MakersAsylumIndia/Arcade/datasheets/How-It-Works-MAX7219-8x8-LED-Matrix-768x463.webp

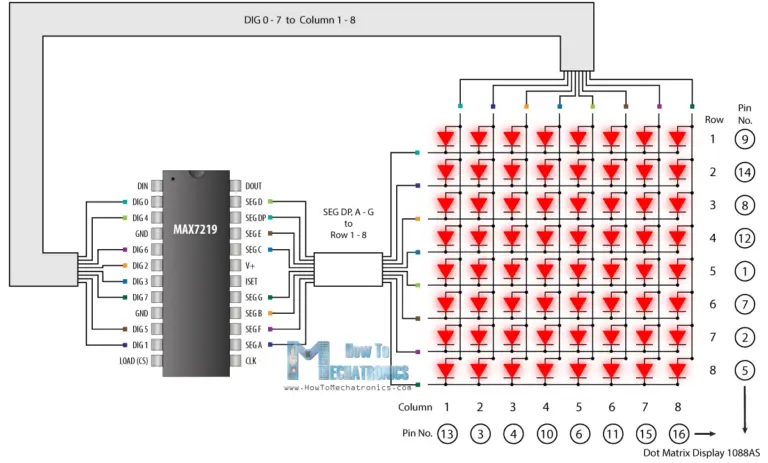
datasheets/How-It-Works-MAX7219-8x8-LED-Matrix-768x463.webp
