MakersAsylumIndia/Arcade/datasheets/led_matrix_fabprint.png

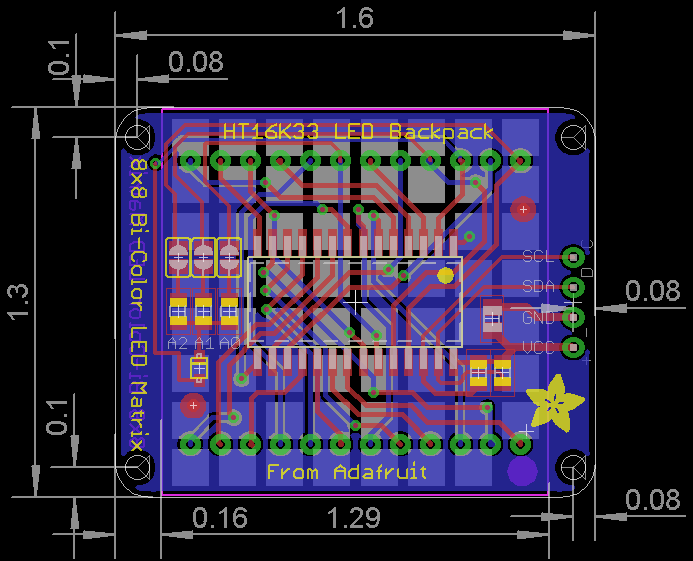
datasheets/led_matrix_fabprint.png
