MakersAsylumIndia/Arcade/datasheets/MAX7219-8-Digit-LED-Display-Driver.jpg

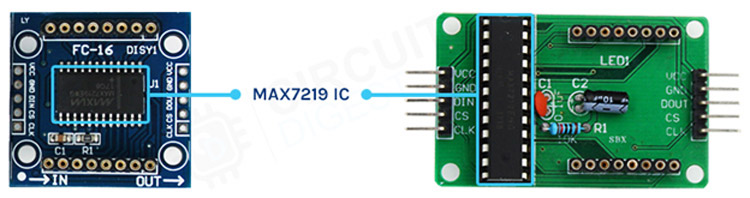
datasheets/MAX7219-8-Digit-LED-Display-Driver.jpg
