MakersAsylumIndia/Arcade/datasheets/max7219-8x8-dot-led-matrix-display-module3-1000x1000.png

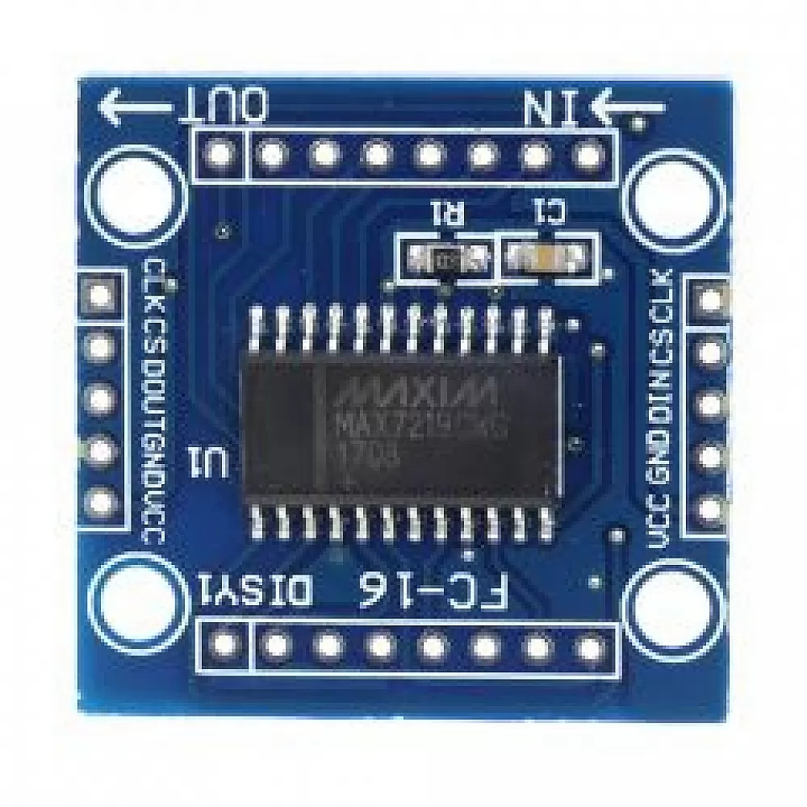
datasheets/max7219-8x8-dot-led-matrix-display-module3-1000x1000.png
