MakersAsylumIndia/Arcade/datasheets/MAX7219-LED-Dot-Matrix-Display-Module-Circuit-Diagram.png

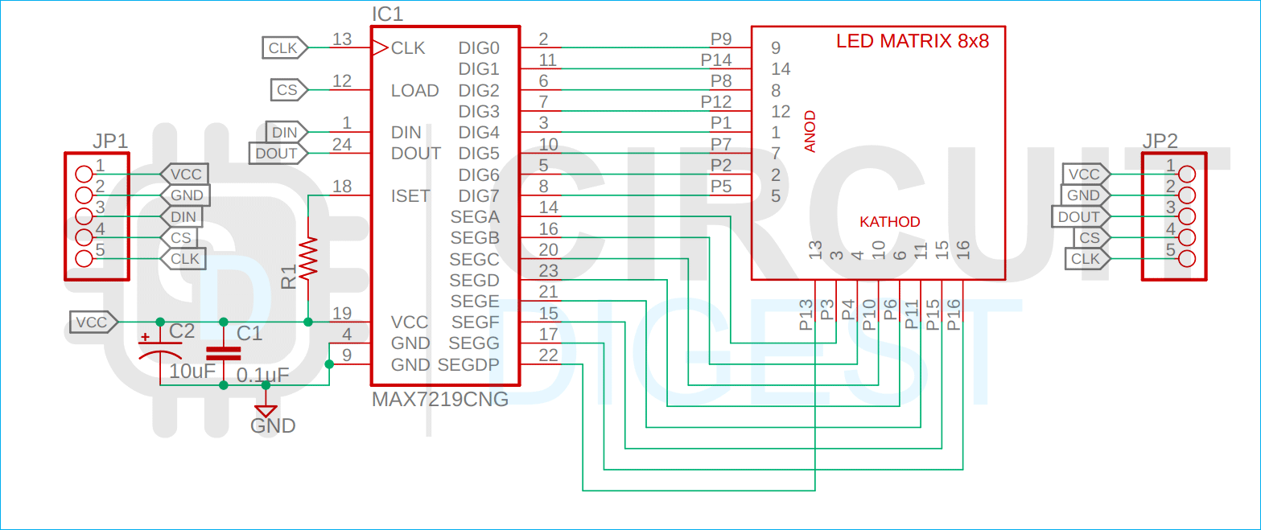
datasheets/MAX7219-LED-Dot-Matrix-Display-Module-Circuit-Diagram.png
