MakersAsylumIndia/Arcade/datasheets/original.jpg

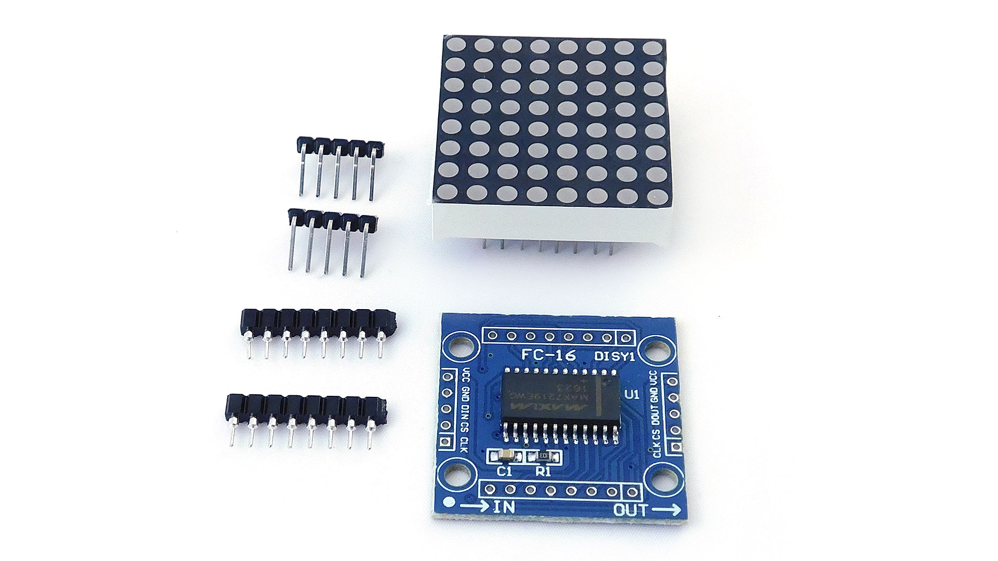
datasheets/original.jpg
