MakersAsylumIndia/Arcade/enclosure/images_prototype/proto_01.jpeg

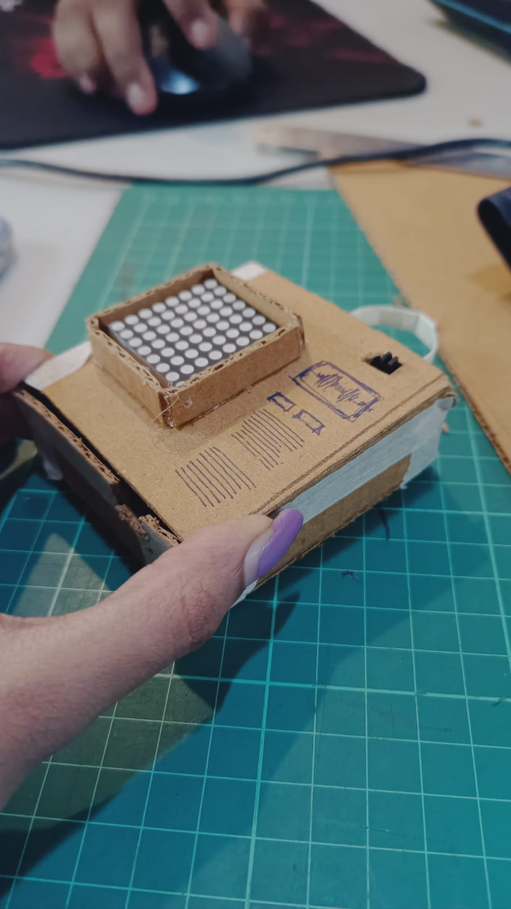
enclosure/images_prototype/proto_01.jpeg
