MakersAsylumIndia/Arcade/enclosure/images_prototype/proto_02.jpeg

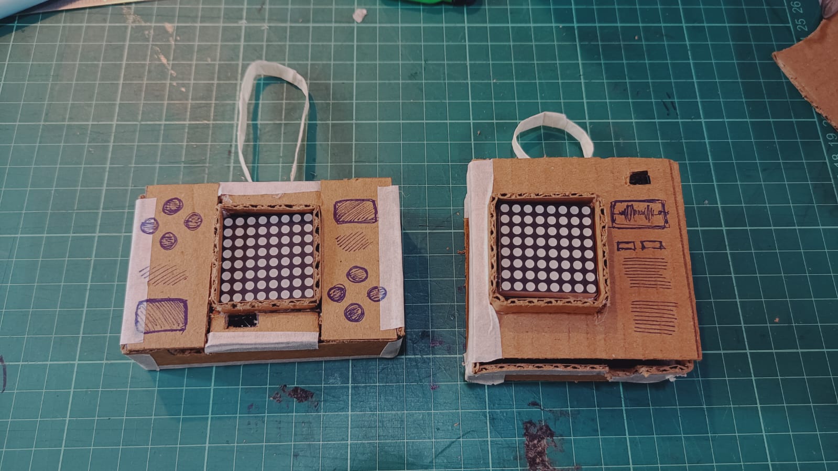
enclosure/images_prototype/proto_02.jpeg
