MakersAsylumIndia/Arcade/enclosure/images_prototype/proto_03.jpeg

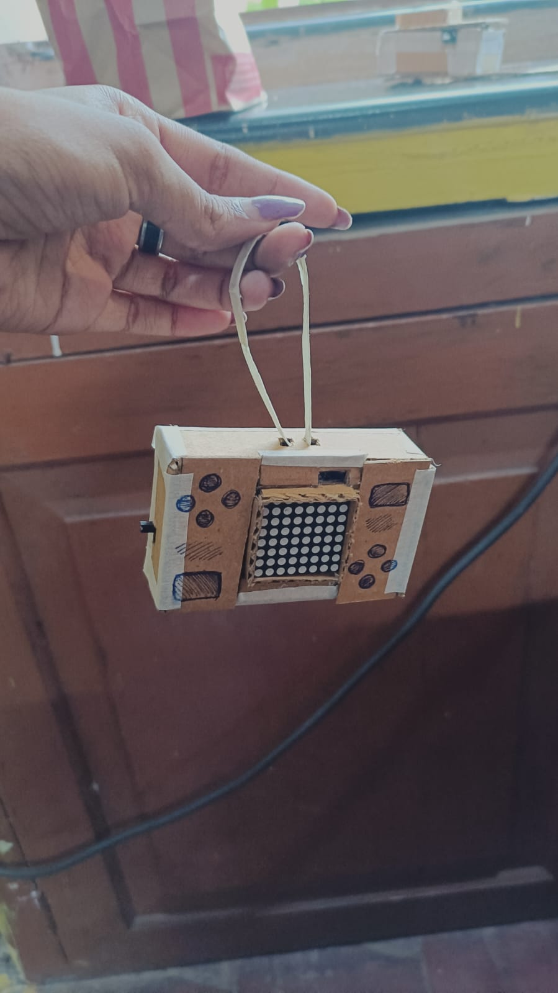
enclosure/images_prototype/proto_03.jpeg
