MakersAsylumIndia/Arcade/enclosure/images_prototype/proto_04.jpeg

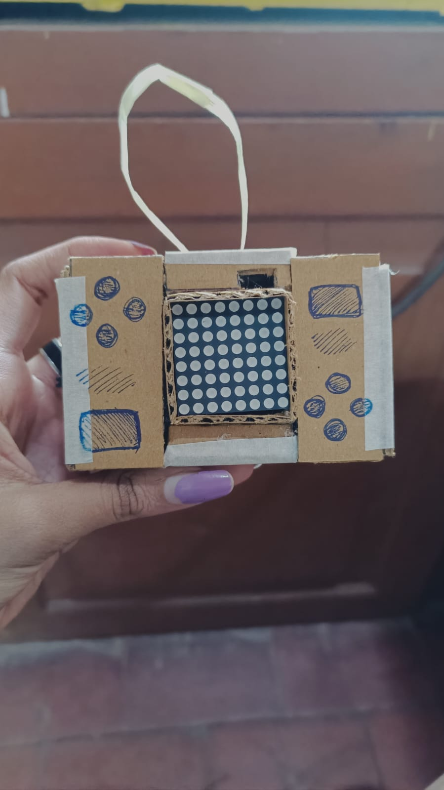
enclosure/images_prototype/proto_04.jpeg
