MakersAsylumIndia/Arcade/enclosure/images_prototype/proto_05.jpeg

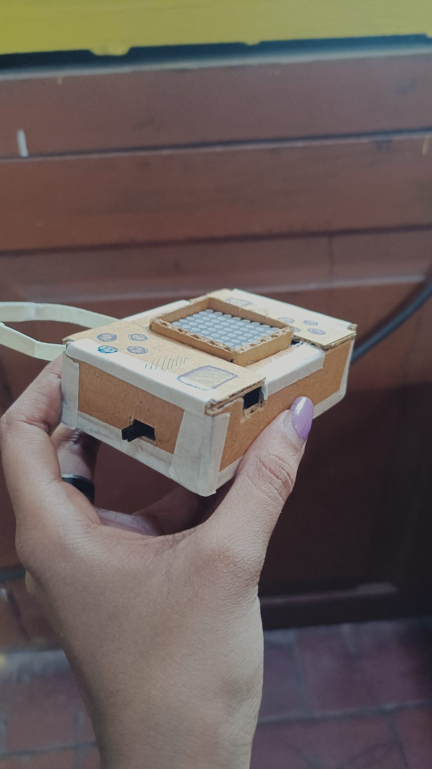
enclosure/images_prototype/proto_05.jpeg
