MakersAsylumIndia/Arcade/enclosure/images_prototype/proto_06.jpeg

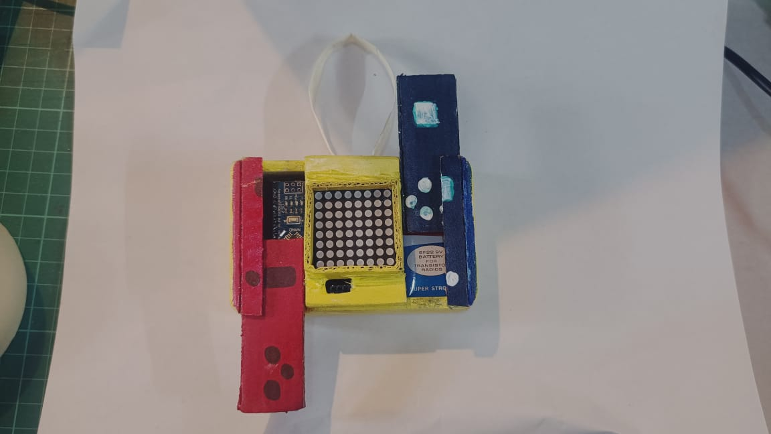
enclosure/images_prototype/proto_06.jpeg
