MakersAsylumIndia/Arcade/enclosure/images_prototype/proto_07.jpeg

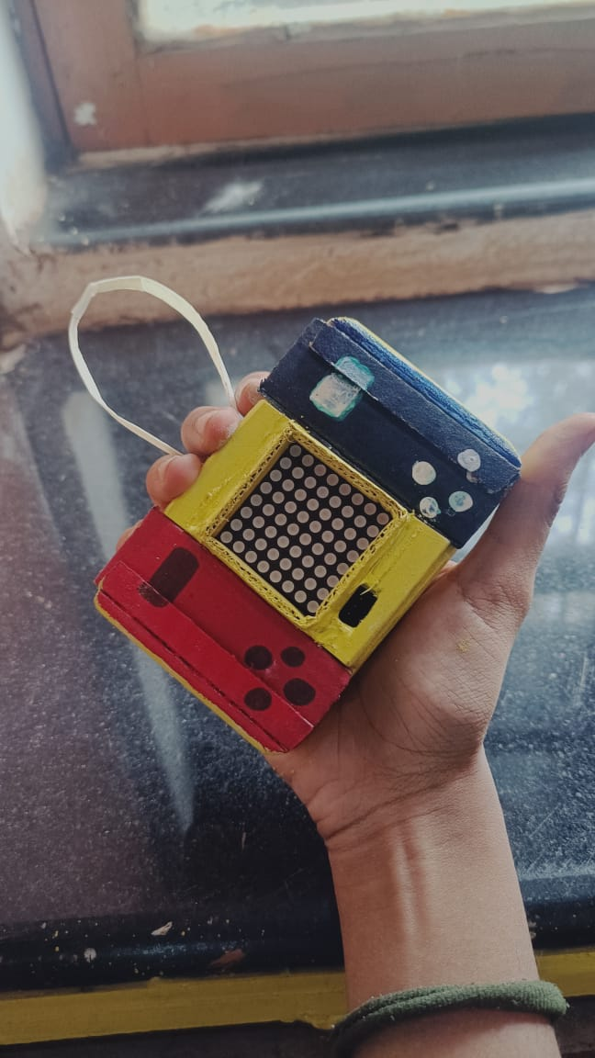
enclosure/images_prototype/proto_07.jpeg
