MakersAsylumIndia/Arcade/enclosure/images_prototype/proto_08.jpeg

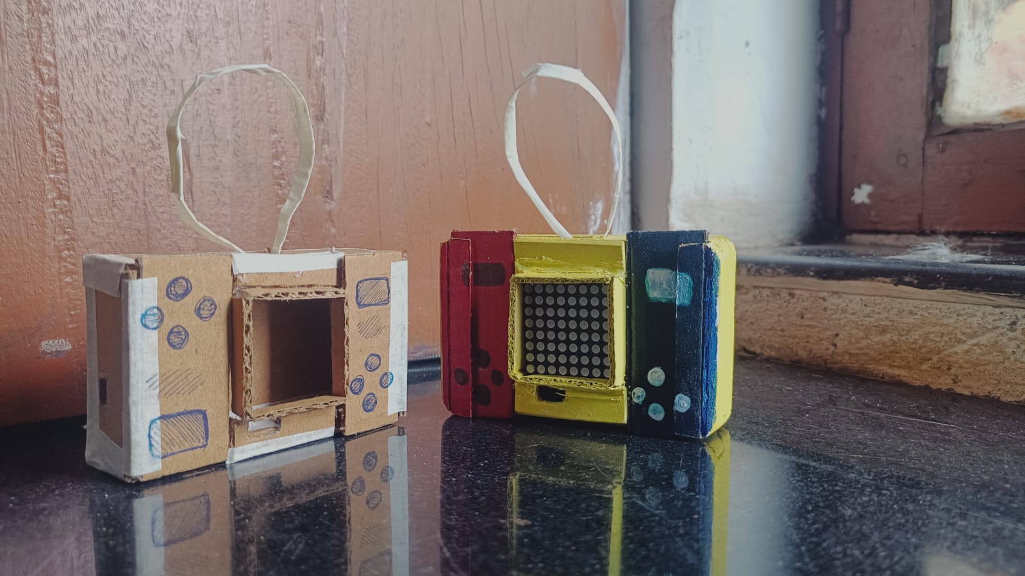
enclosure/images_prototype/proto_08.jpeg
