MakersAsylumIndia/Arcade/enclosure/images_prototype/proto_09.jpeg

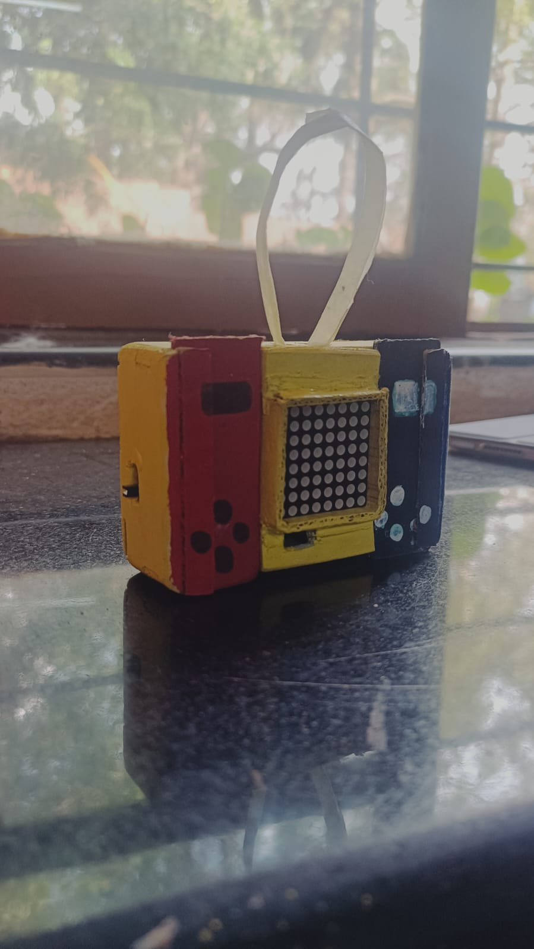
enclosure/images_prototype/proto_09.jpeg
