MakersAsylumIndia/Arcade/enclosure/images_prototype/TheThing_Arcade_v1_01.png

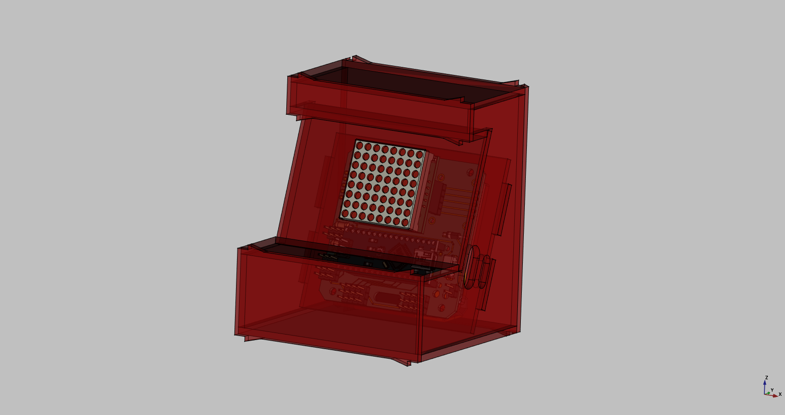
enclosure/images_prototype/TheThing_Arcade_v1_01.png
