MakersAsylumIndia/Arcade/enclosure/renders/Arcade_v7_01.png

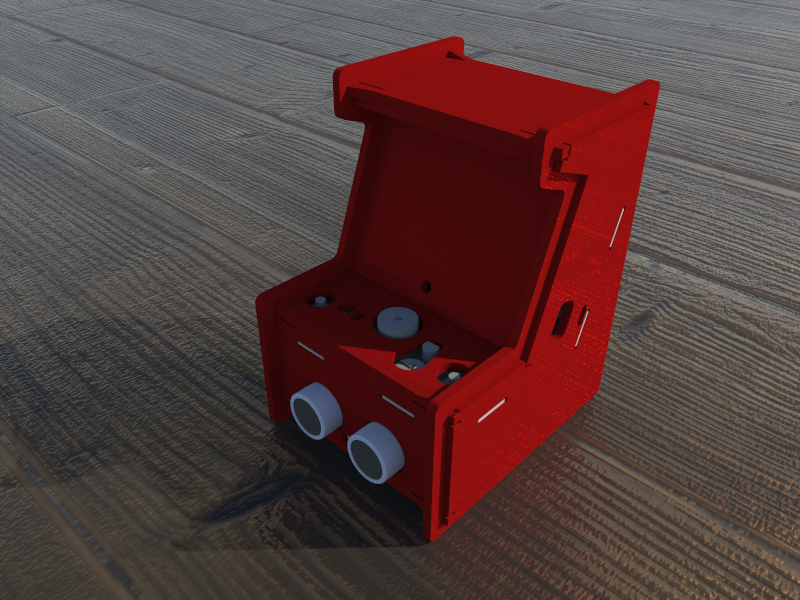
enclosure/renders/Arcade_v7_01.png
