MakersAsylumIndia/Arcade/enclosure/renders/Arcade_v7_02.png

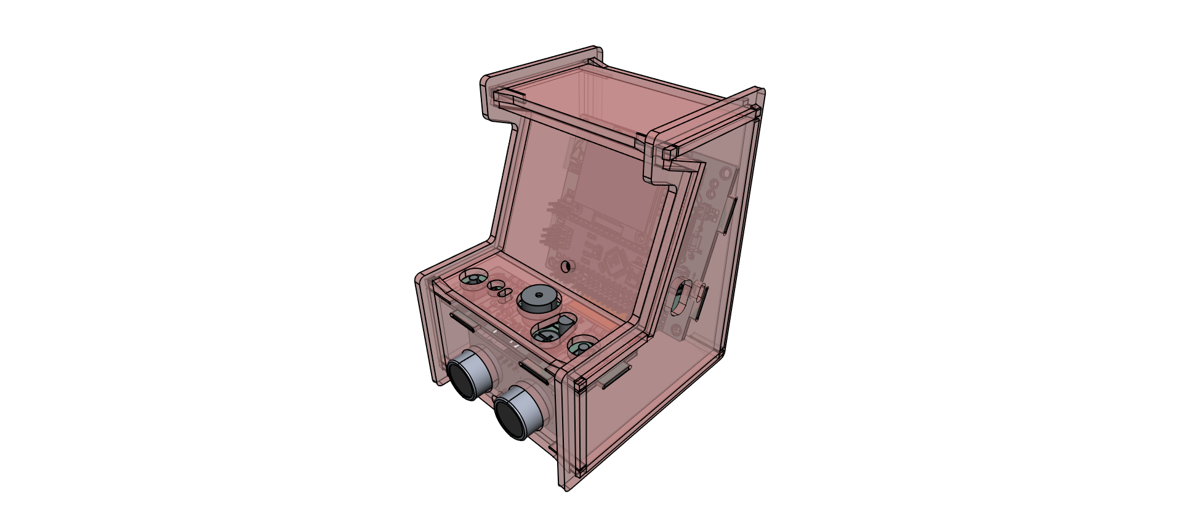
enclosure/renders/Arcade_v7_02.png
