MakersAsylumIndia/Arcade/enclosure/renders/Arcade_v7_04.png

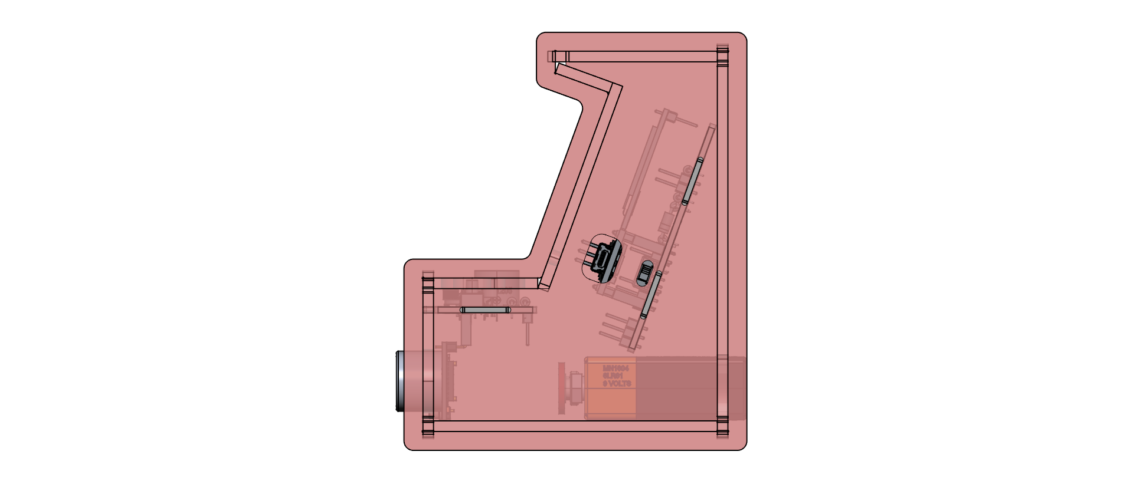
enclosure/renders/Arcade_v7_04.png
