MakersAsylumIndia/Arcade/enclosure/renders/Arcade_v7_09.png

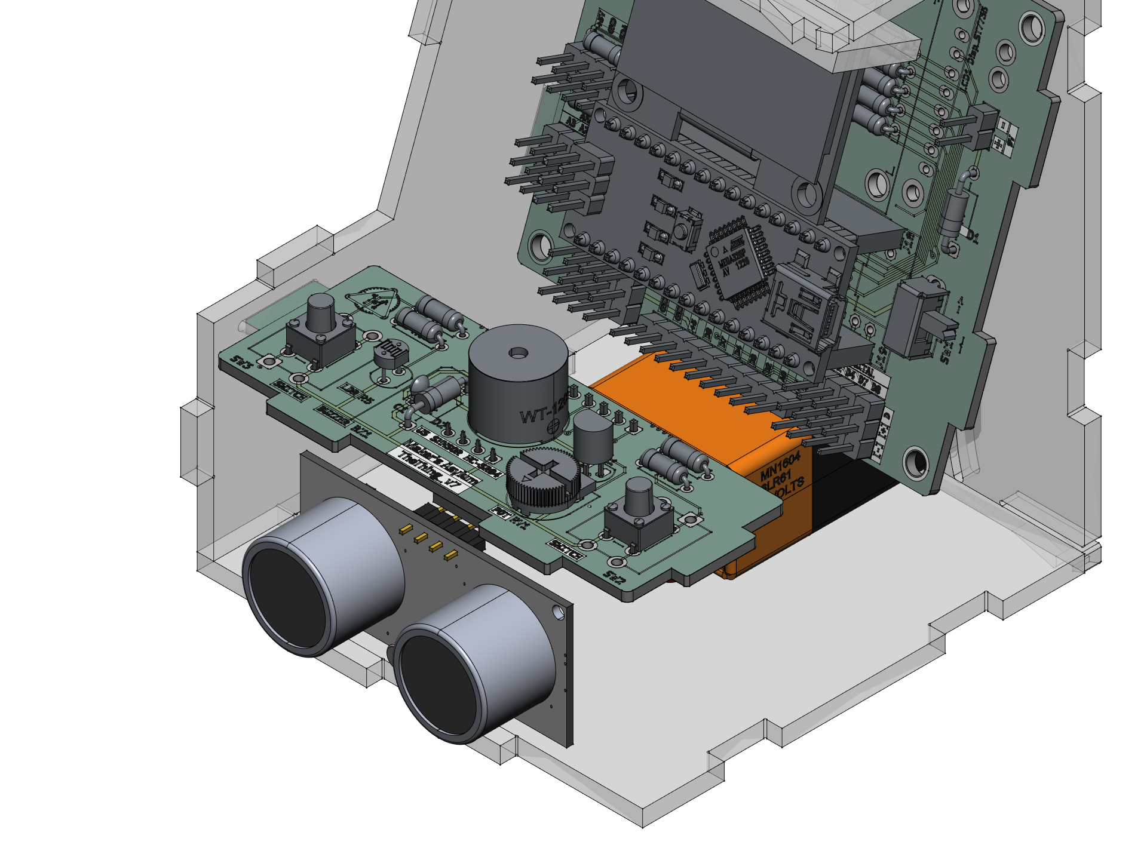
enclosure/renders/Arcade_v7_09.png
