MakersAsylumIndia/Arcade/enclosure/renders/Arcade_v7_10.png

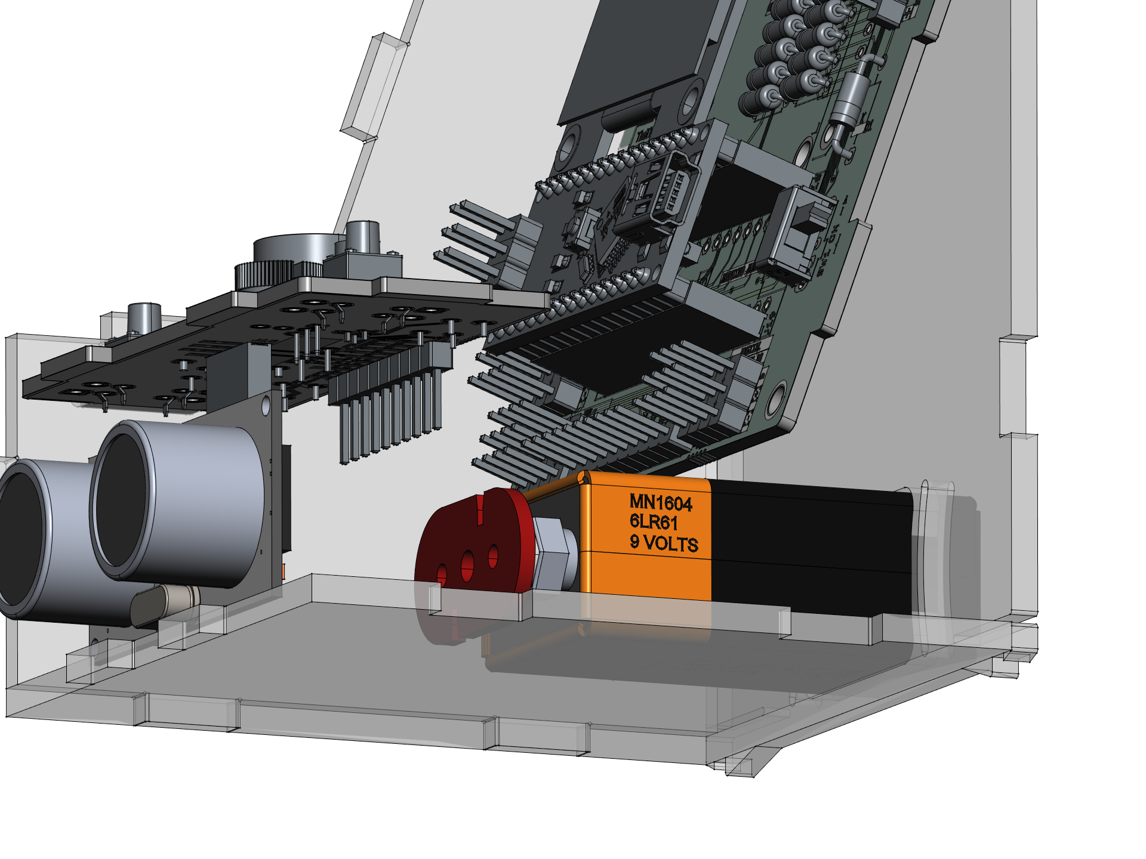
enclosure/renders/Arcade_v7_10.png
