MakersAsylumIndia/Arcade/enclosure/renders/Arcade_v7_11.png

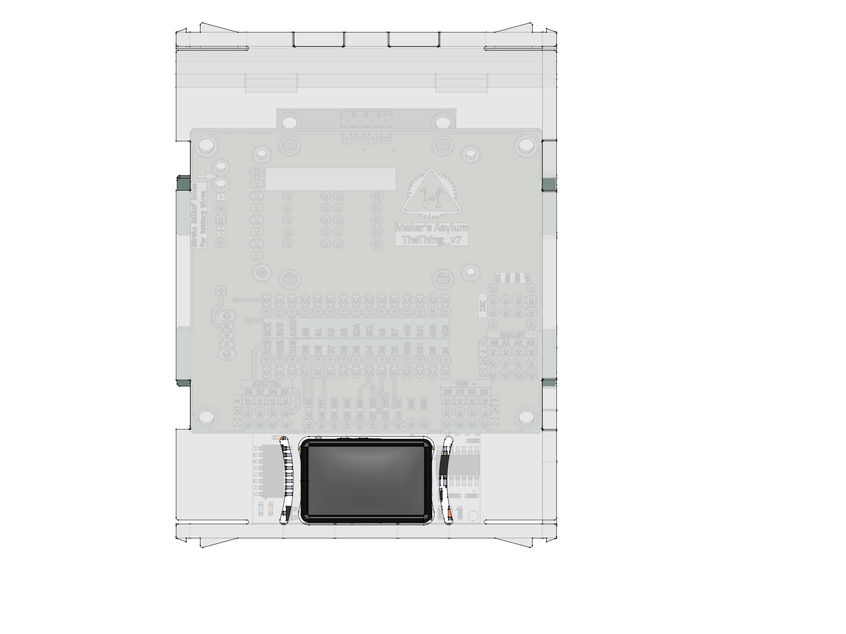
enclosure/renders/Arcade_v7_11.png
