MakersAsylumIndia/Arcade/enclosure/renders/Arcade_v7_12.png

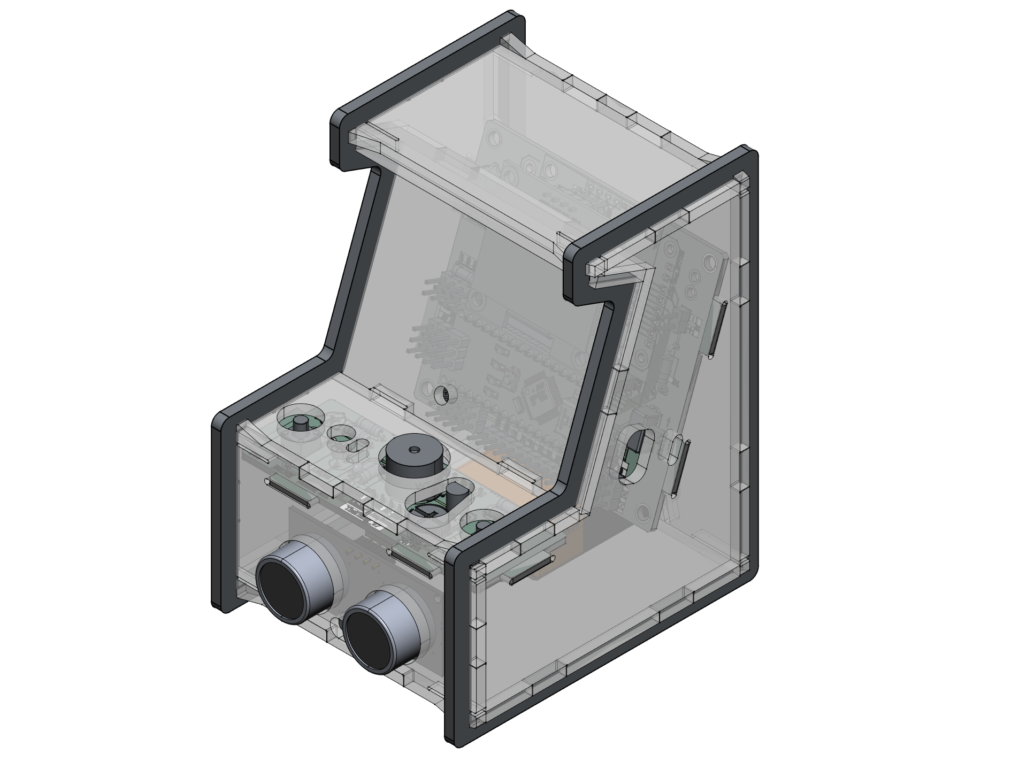
enclosure/renders/Arcade_v7_12.png
