MakersAsylumIndia/Arcade/enclosure/renders/Arcade_v7_13.png

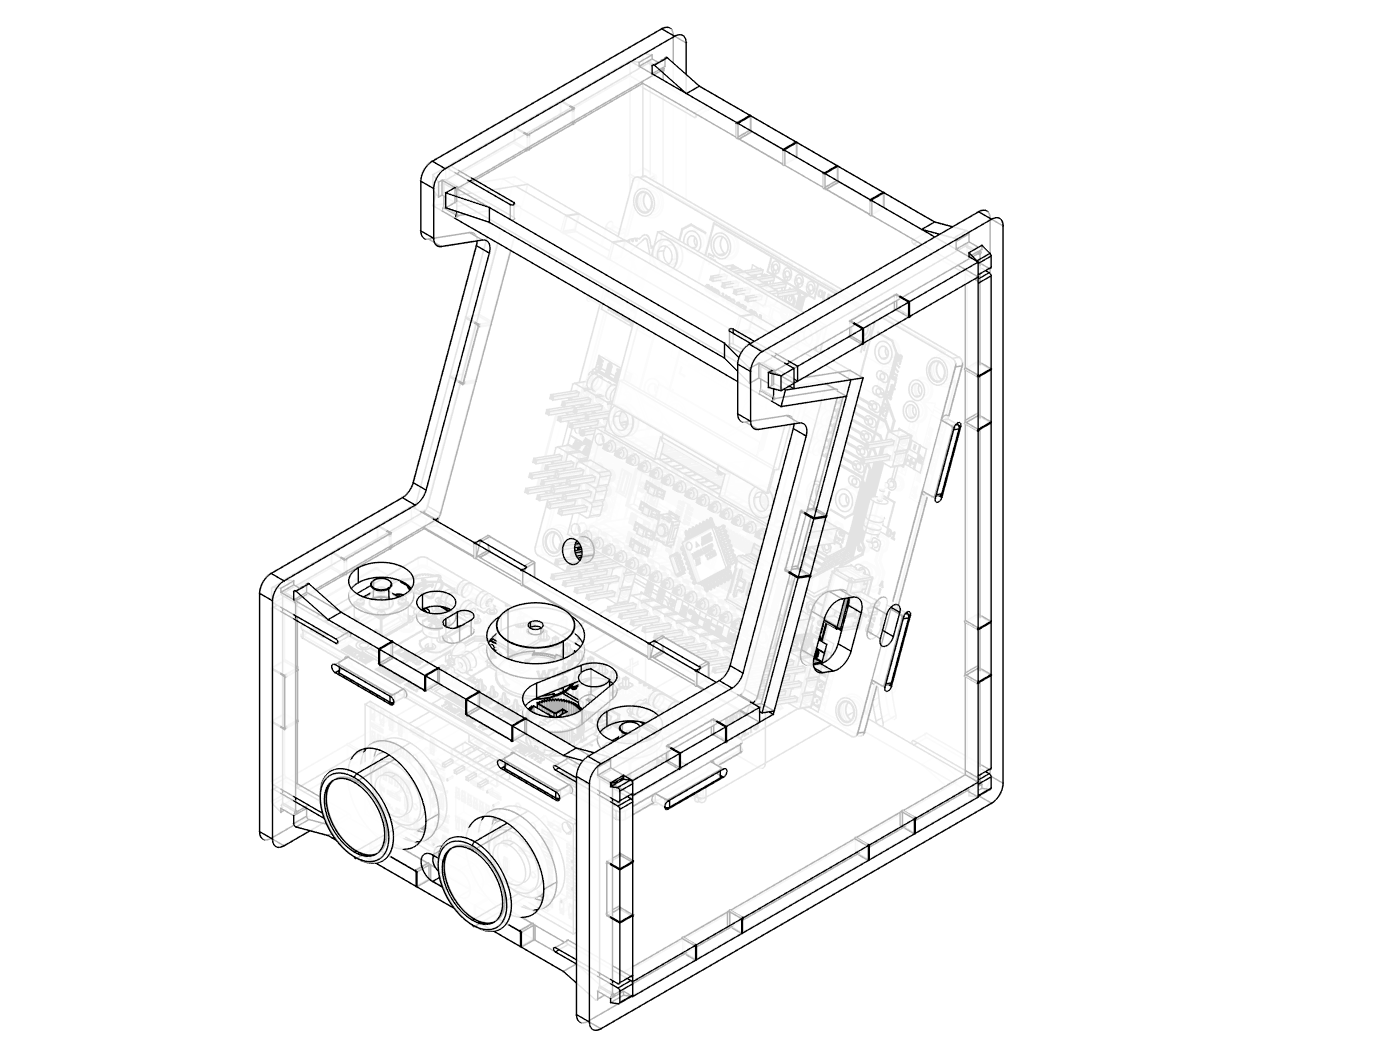
enclosure/renders/Arcade_v7_13.png
