MakersAsylumIndia/Arcade/enclosure/renders/TheThing_v5_TD01_pg2.png

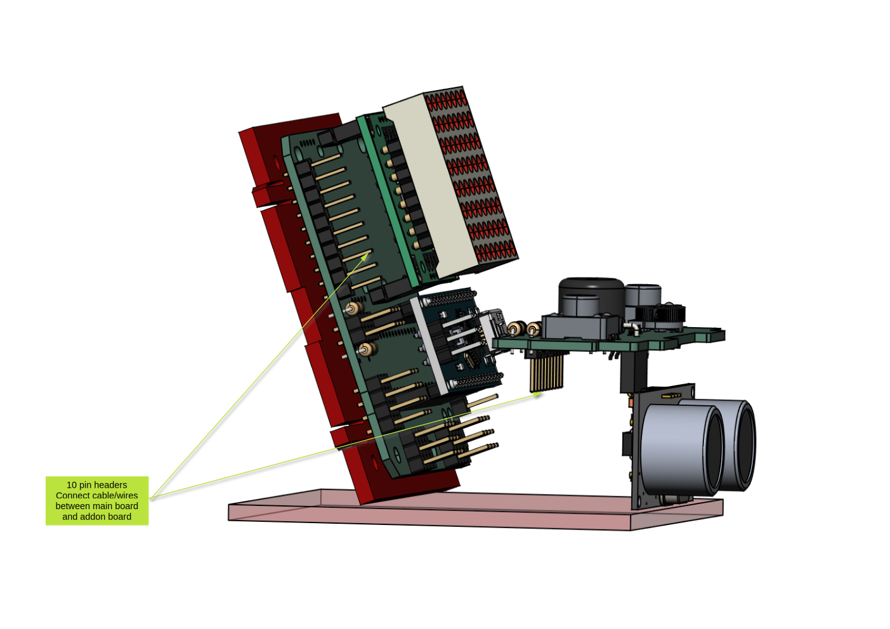
enclosure/renders/TheThing_v5_TD01_pg2.png
