MakersAsylumIndia/Arcade/hardware_PCB/TheThing_v8/images/TheThing_pcb_02.png

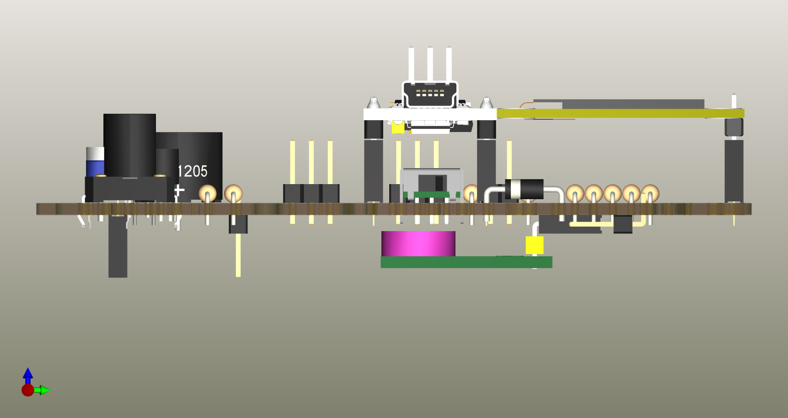
hardware_PCB/TheThing_v8/images/TheThing_pcb_02.png
