MakersAsylumIndia/Arcade/hardware_PCB/TheThing_v8/images/TheThing_pcb_03.png

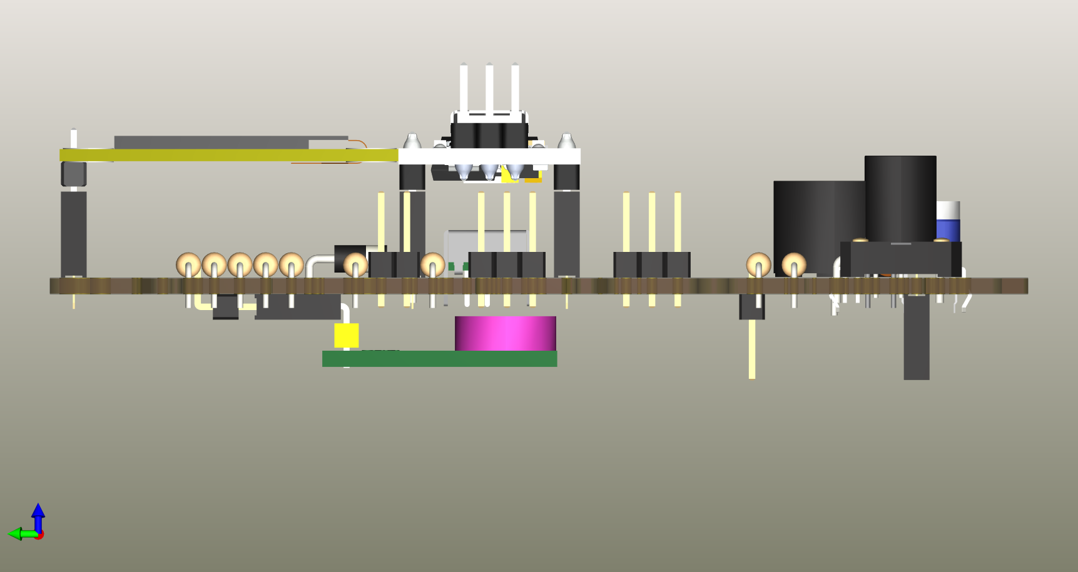
hardware_PCB/TheThing_v8/images/TheThing_pcb_03.png
