MakersAsylumIndia/Arcade/hardware_PCB/TheThing_v8/images/TheThing_pcb_07.png

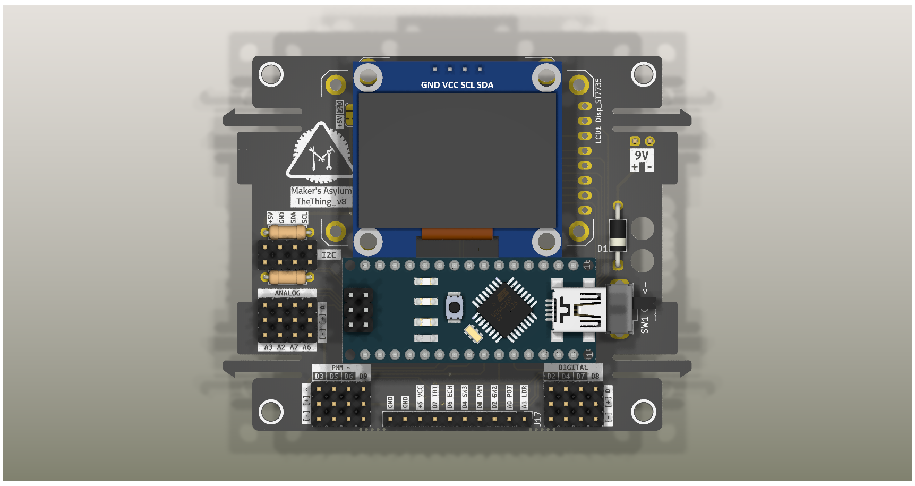
hardware_PCB/TheThing_v8/images/TheThing_pcb_07.png
