MakersAsylumIndia/Arcade/hardware_PCB/TheThing_v8/images/TheThing_pcb_10.png

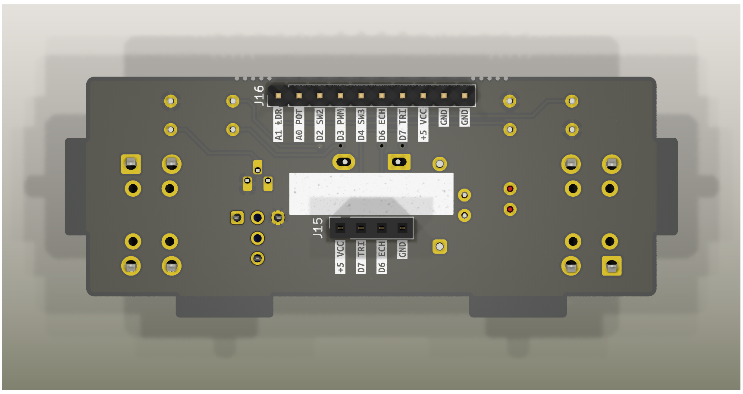
hardware_PCB/TheThing_v8/images/TheThing_pcb_10.png
