MakersAsylumIndia/Arcade/hardware_PCB/TheThing_v8/images/TheThing_pcb_12.png

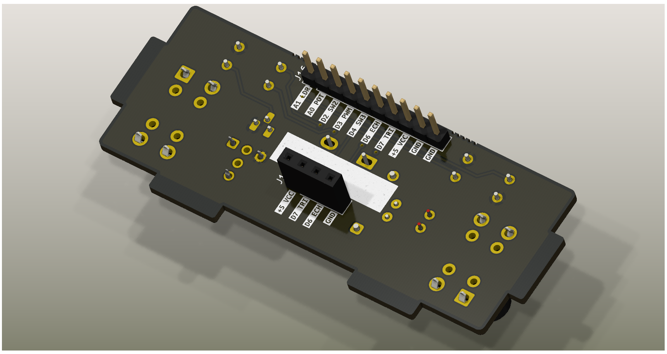
hardware_PCB/TheThing_v8/images/TheThing_pcb_12.png
