MakersAsylumIndia/Arcade/hardware_PCB/TheThing_v8/images/TheThing_PCB_B.png

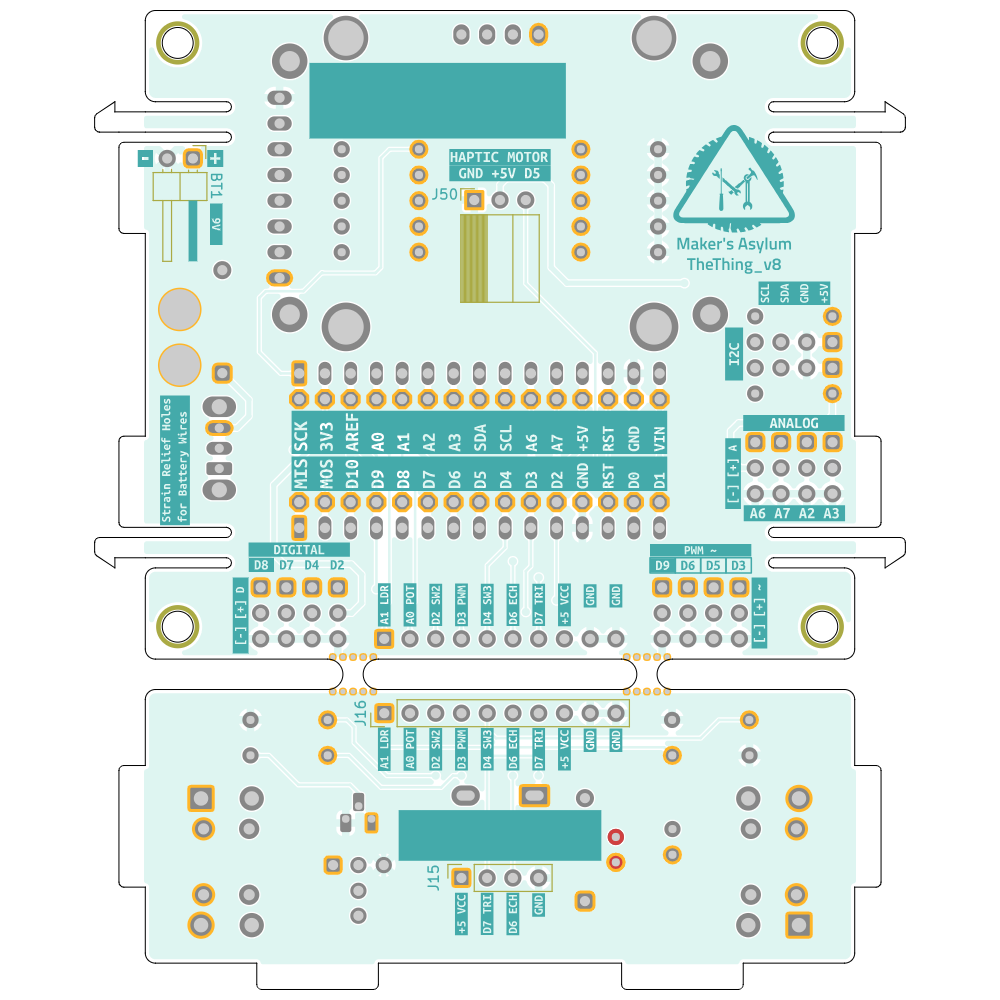
hardware_PCB/TheThing_v8/images/TheThing_PCB_B.png
