MakersAsylumIndia/Arcade/hardware_PCB/TheThing_v8/images/TheThing_PCB_F.png

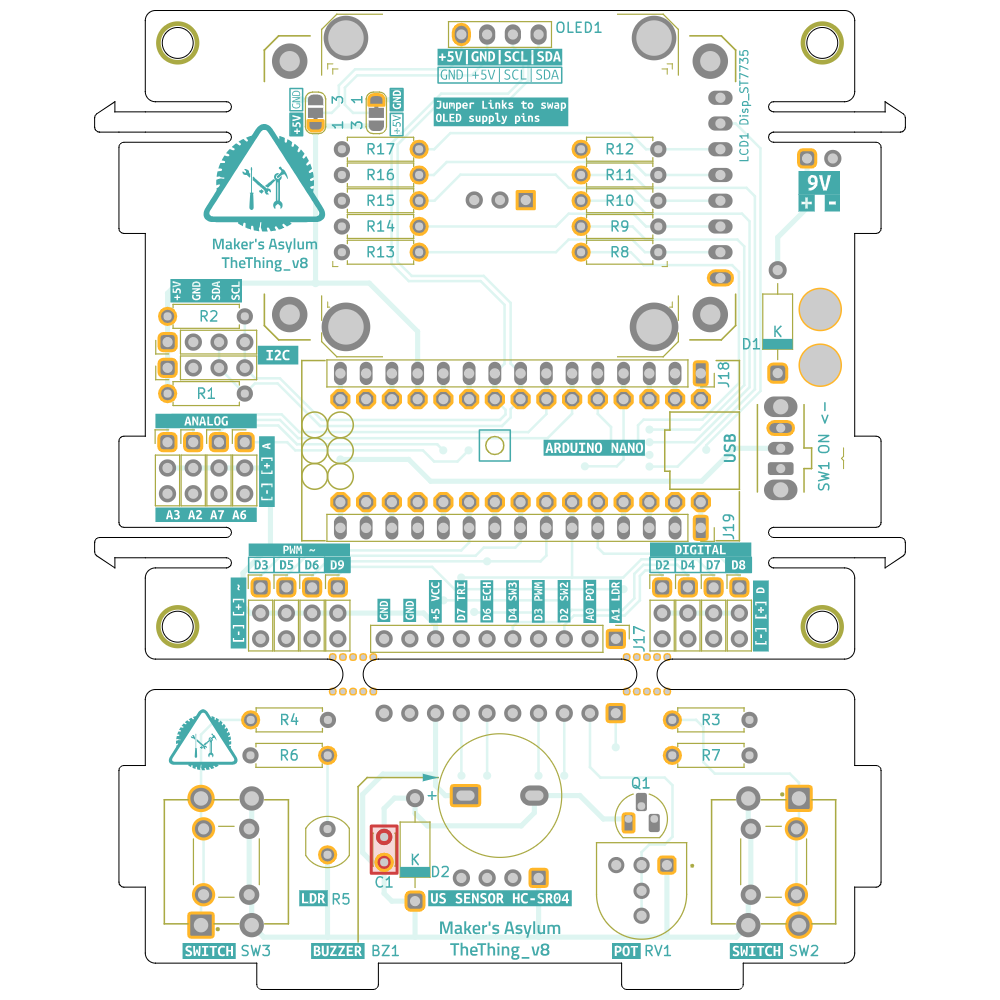
hardware_PCB/TheThing_v8/images/TheThing_PCB_F.png
