MakersAsylumIndia/Arcade/hardware_PCB/TheThing_v8/vegg_production/MA_TheThing_v8_vegg/TheThing_pcb_06.png

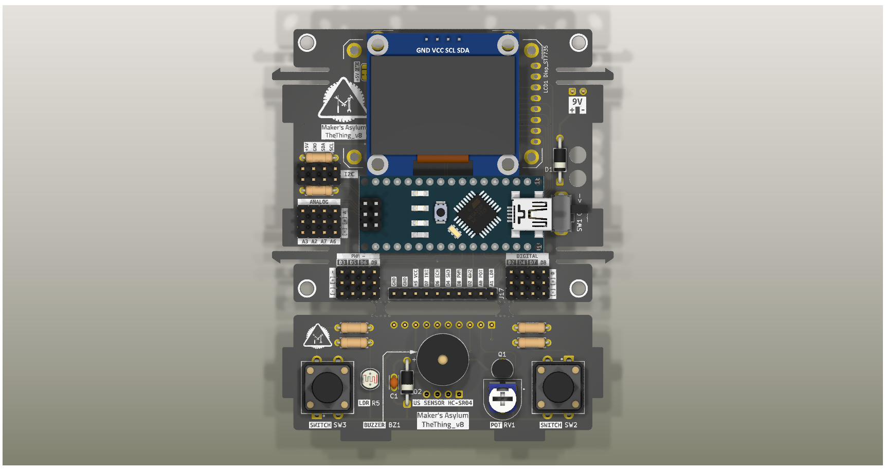
hardware_PCB/TheThing_v8/vegg_production/MA_TheThing_v8_vegg/TheThing_pcb_06.png
