MakersAsylumIndia/Arcade/kicad_v5/TheThing/images/TheThing_pcb_07.png

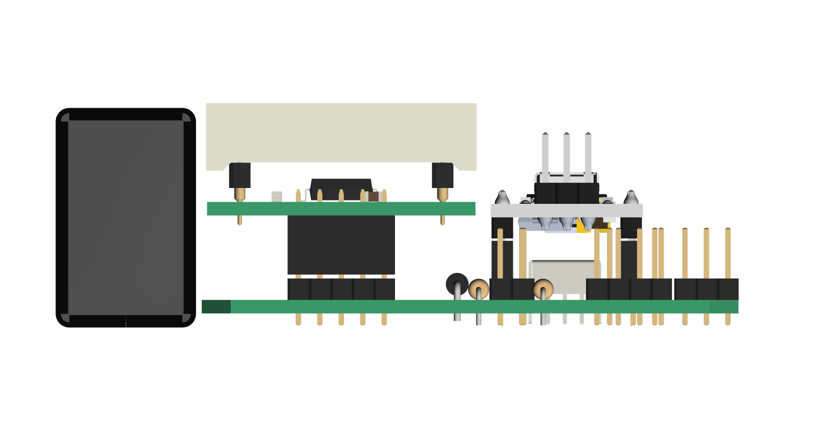
kicad_v5/TheThing/images/TheThing_pcb_07.png
