MakersAsylumIndia/Arcade/enclosure/DXF/TheThing_v8B_tabs_export_fix1-Sketch.dxf

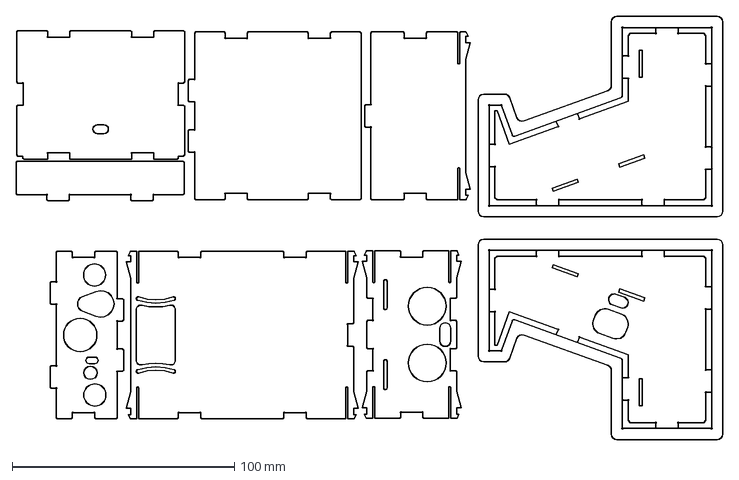
[picture p103: CAD file, 2025-10-11]
enclosure/DXF/TheThing_v8B_tabs_export_fix1-Sketch.dxf
318.2 x 190.6 mm
