MakersAsylumIndia/Arcade/enclosure/footprints_for_kicad/HC_SR04.FCStd

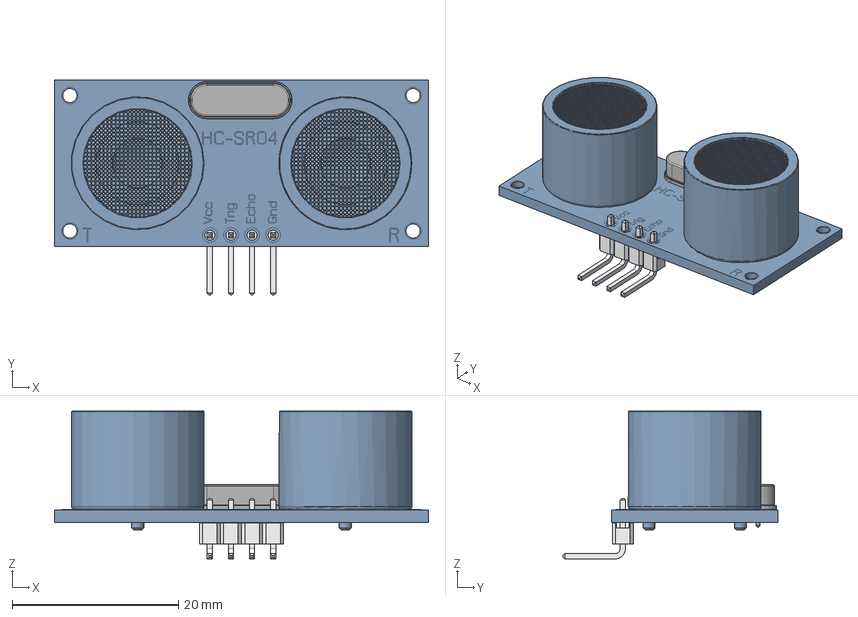
[picture p104: CAD file, 2025-11-04]
enclosure/footprints_for_kicad/HC_SR04.FCStd
45.0 x 25.8 x 17.8 mm
Quarz
Platine
Pins_4fach_90Grad_001
HC_SR04_gitter_001
HC_SR04_gitter_002
