MakersAsylumIndia/Arcade/enclosure/footprints_for_kicad/Tactile_Switch/TL1105BF160Q.step

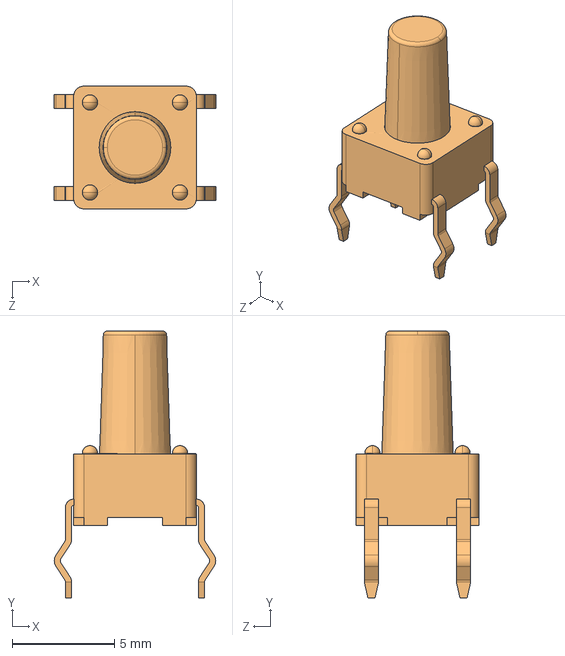
[picture p105: CAD file, 2024-11-12]
enclosure/footprints_for_kicad/Tactile_Switch/TL1105BF160Q.step
7.89 x 13.0 x 6.00 mm
Body1.STEP
Body2.STEP
