MakersAsylumIndia/Arcade/enclosure/TheThing_v8.FCStd

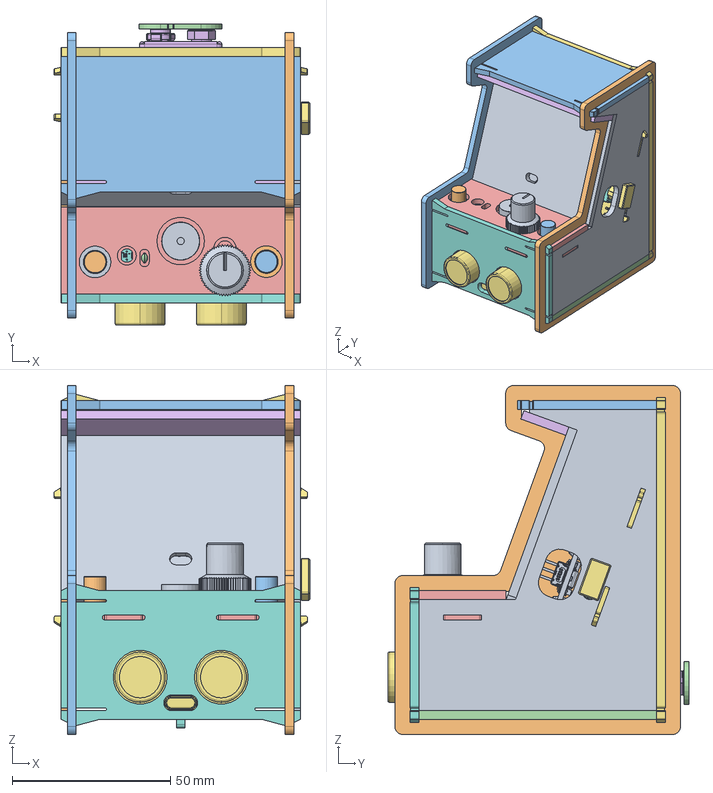
[picture p106: CAD file, 2026-05-04]
enclosure/TheThing_v8.FCStd
80.8 x 95.1 x 110.2 mm
Body_right
Body_left
Body_top
Body_bottom
Body_keys
Body_under
Body_back
Body_front
Body_face
Body_right_clip
Body_left_clip
_68005_cp005_cp
_68005_cp005_cp003
_68005_cp005_cp004
hc-sr04
SW_CuK_OS102011MA1QN1_SPDT_Angled001
PinHeader_1x04_P2.54mm_Vertical007
R_Axial_DIN0207_L6.3mm_D2.5mm_P7.62mm_Horizontal035
D_DO-41_SOD81_P10.16mm_Horizontal008
PinHeader_1x10_P2.54mm_Vertical004
PinHeader_1x03_P2.54mm_Vertical047
R_Axial_DIN0207_L6.3mm_D2.5mm_P7.62mm_Horizontal036
R_Axial_DIN0207_L6.3mm_D2.5mm_P7.62mm_Horizontal037
PinSocket_1x15_P2.54mm_Vertical
arduino_nano
arduino_nano006
R_Axial_DIN0207_L6.3mm_D2.5mm_P7.62mm_Horizontal038
PinHeader_1x03_P2.54mm_Vertical048
PinHeader_1x03_P2.54mm_Vertical049
PinHeader_1x03_P2.54mm_Vertical050
PinHeader_1x03_P2.54mm_Vertical051
Display_OLED-1_3-128X64
Display_OLED-1_3-128X072
Display_OLED-1_3-128X073
PinSocket_1x04_P2.54mm_Vertical001
PinSocket_1x15_P2.54mm_Vertical004
R_Axial_DIN0207_L6.3mm_D2.5mm_P7.62mm_Horizontal039
R_Axial_DIN0207_L6.3mm_D2.5mm_P7.62mm_Horizontal040
PinHeader_1x03_P2.54mm_Vertical052
R_Axial_DIN0207_L6.3mm_D2.5mm_P7.62mm_Horizontal041
PinHeader_1x03_P2.54mm_Vertical053
R_Axial_DIN0207_L6.3mm_D2.5mm_P7.62mm_Horizontal042
R_Axial_DIN0207_L6.3mm_D2.5mm_P7.62mm_Horizontal043
R_Axial_DIN0207_L6.3mm_D2.5mm_P7.62mm_Horizontal044
PinHeader_1x03_P2.54mm_Vertical054
R_Axial_DIN0207_L6.3mm_D2.5mm_P7.62mm_Horizontal045
PinHeader_1x03_P2.54mm_Vertical055
R_Axial_DIN0207_L6.3mm_D2.5mm_P7.62mm_Horizontal046
PinHeader_1x03_P2.54mm_Vertical056
PinHeader_1x03_P2.54mm_Vertical057
PinHeader_1x04_P2.54mm_Vertical008
PinHeader_1x03_P2.54mm_Vertical058
PinSocket_1x03_P2.54mm_Horizontal_haptic
PinSocket_1x03_P2.54mm_Horizontal_haptic001
PinSocket_1x03_P2.54mm_Horizontal_haptic002
PinSocket_1x03_P2.54mm_Horizontal_haptic003
PinSocket_1x03_P2.54mm_Horizontal_haptic004
PinSocket_1x03_P2.54mm_Horizontal_haptic005
PinSocket_1x03_P2.54mm_Horizontal_haptic006
PinSocket_1x03_P2.54mm_Horizontal_haptic007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
