MakersAsylumIndia/Arcade/fabricate/DXF/#TheThing_v3_tabs.dxf

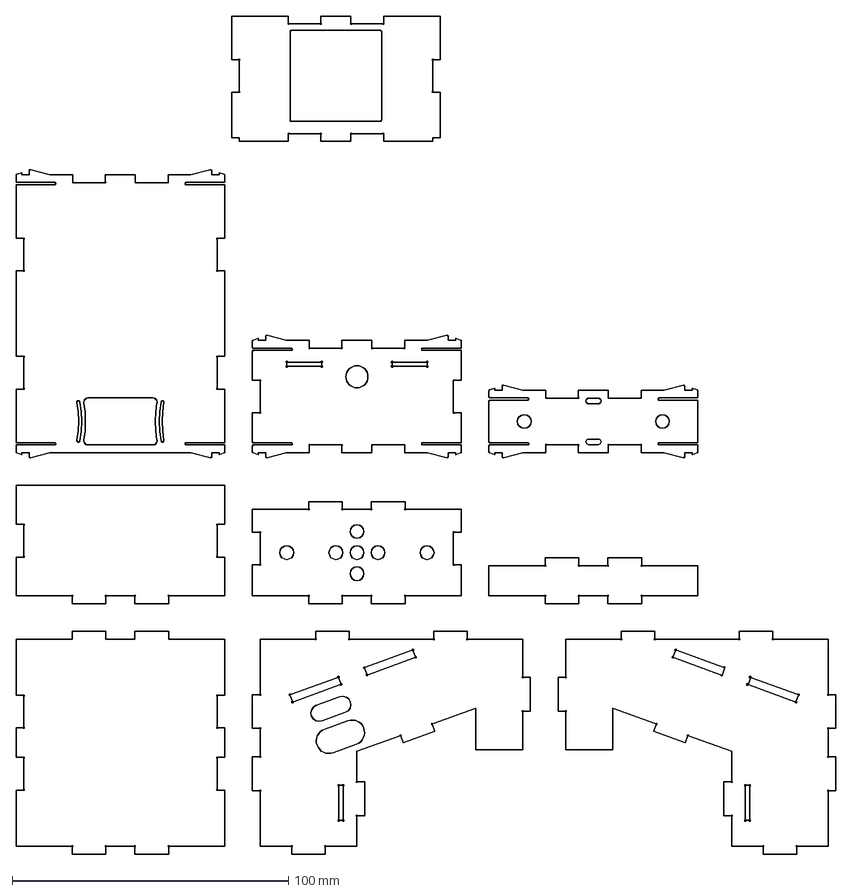
[picture p107: CAD file, 2025-02-07]
fabricate/DXF/#TheThing_v3_tabs.dxf
296.8 x 303.3 mm
