MakersAsylumIndia/Arcade/fabricate/TheThing_v3_multijoin.FCStd

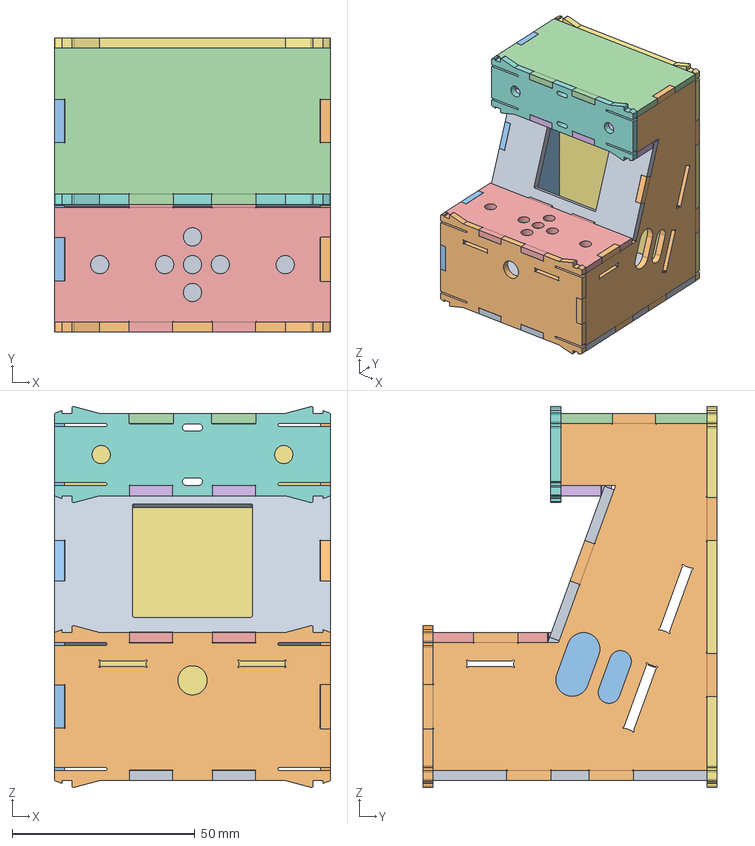
[picture p108: CAD file, 2024-12-13]
fabricate/TheThing_v3_multijoin.FCStd
75.6 x 80.6 x 104.4 mm
Pad014_tab
Pocket011_tab
Pocket013_tab
Pad013_tab
Pad015_tab
Pad016_tab
Pocket007_tab
Pocket_tab
