MakersAsylumIndia/Arcade/hardware_PCB/TheThing_v8/3D_models/PinSocket_1x03_P2.54mm_Horizontal_haptic.step

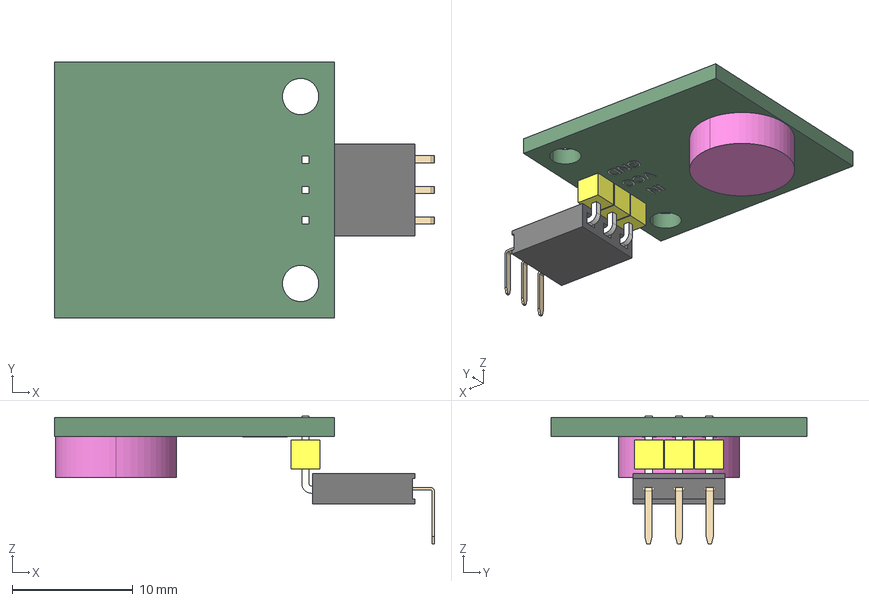
[picture p109: CAD file, 2025-08-25]
hardware_PCB/TheThing_v8/3D_models/PinSocket_1x03_P2.54mm_Horizontal_haptic.step
31.5 x 21.2 x 10.6 mm
