MakersAsylumIndia/Arcade/enclosure/3D_print/TheThing_v8-trimpot_knob_v4.step

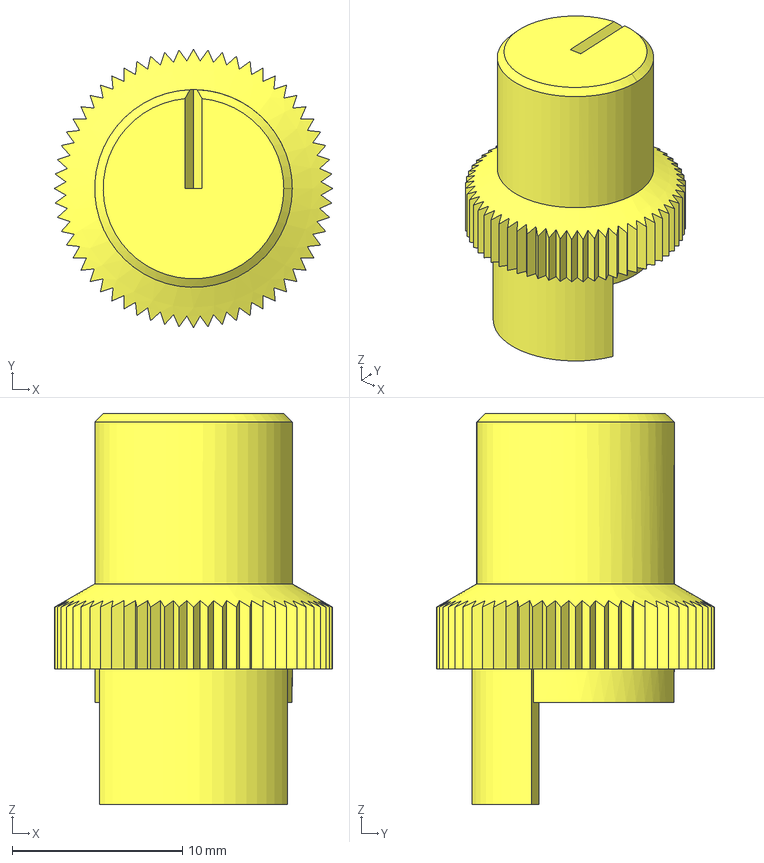
[picture p110: CAD file, 2026-05-04]
enclosure/3D_print/TheThing_v8-trimpot_knob_v4.step
16.3 x 16.3 x 22.9 mm
