MakersAsylumIndia/Arcade/enclosure/footprints_for_kicad/pot_knob-BodyChamfer.step

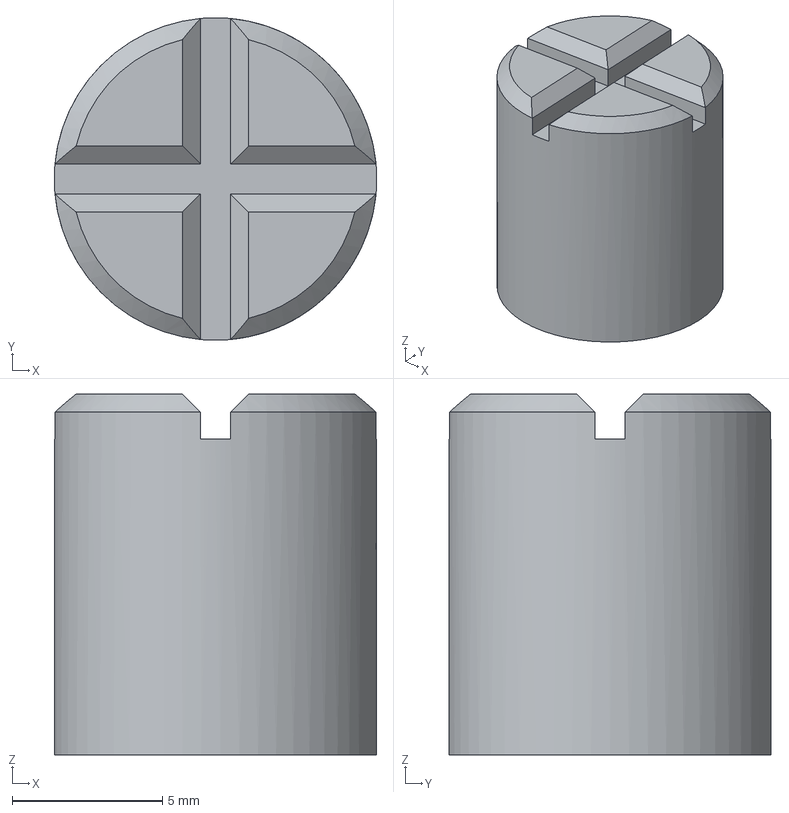
[picture p111: CAD file, 2025-07-18]
enclosure/footprints_for_kicad/pot_knob-BodyChamfer.step
10.7 x 10.7 x 12.0 mm
