MakersAsylumIndia/Arcade/enclosure/3D_print/TheThing_v8-trimpot_knob_v3.3mf

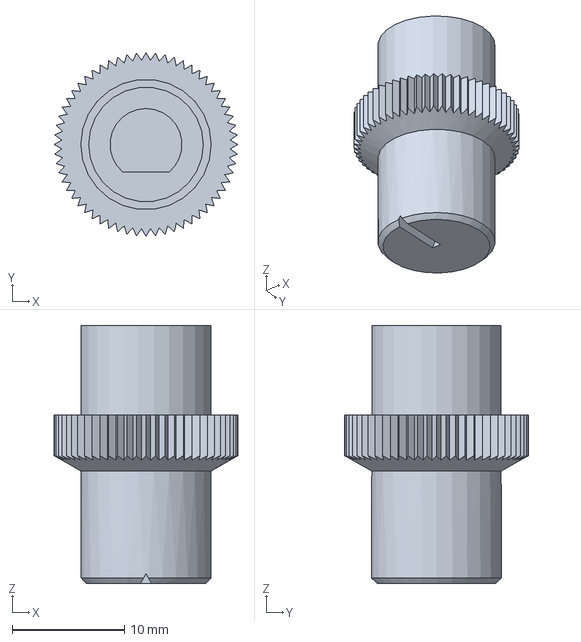
[picture p113: CAD file, 2025-11-04]
enclosure/3D_print/TheThing_v8-trimpot_knob_v3.3mf
16.3 x 16.3 x 22.9 mm
