MakersAsylumIndia/Arcade/enclosure/footprints_for_kicad/pot_knob.FCStd

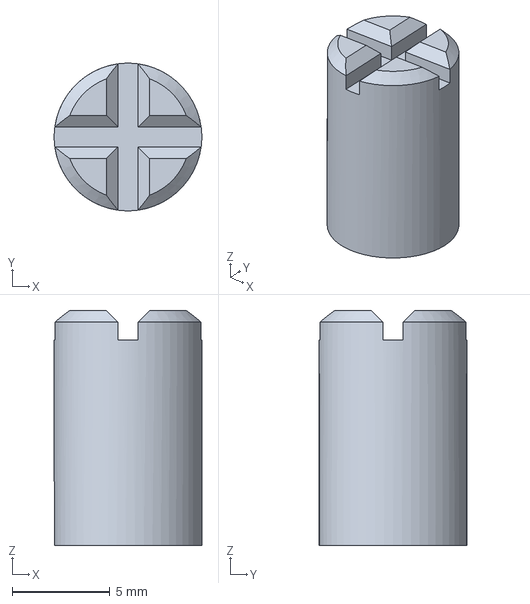
[picture p114: CAD file, 2025-07-18]
enclosure/footprints_for_kicad/pot_knob.FCStd
7.54 x 7.54 x 12.0 mm
