MakersAsylumIndia/Arcade/fabricate/DXF/TheThing_v3-right_clip.dxf

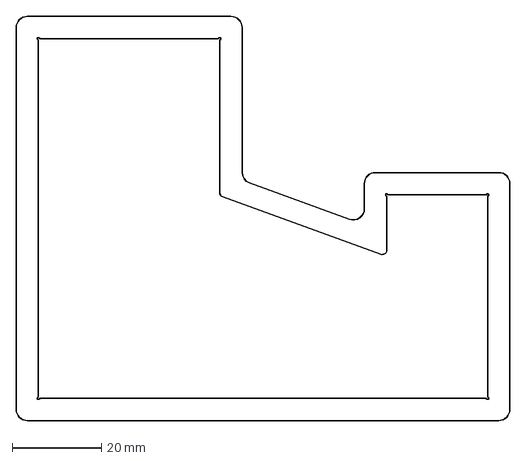
[picture p115: CAD file, 2024-11-12]
fabricate/DXF/TheThing_v3-right_clip.dxf
110.6 x 90.6 mm
