MakersAsylumIndia/Arcade/fabricate/FC-16_v1.FCStd

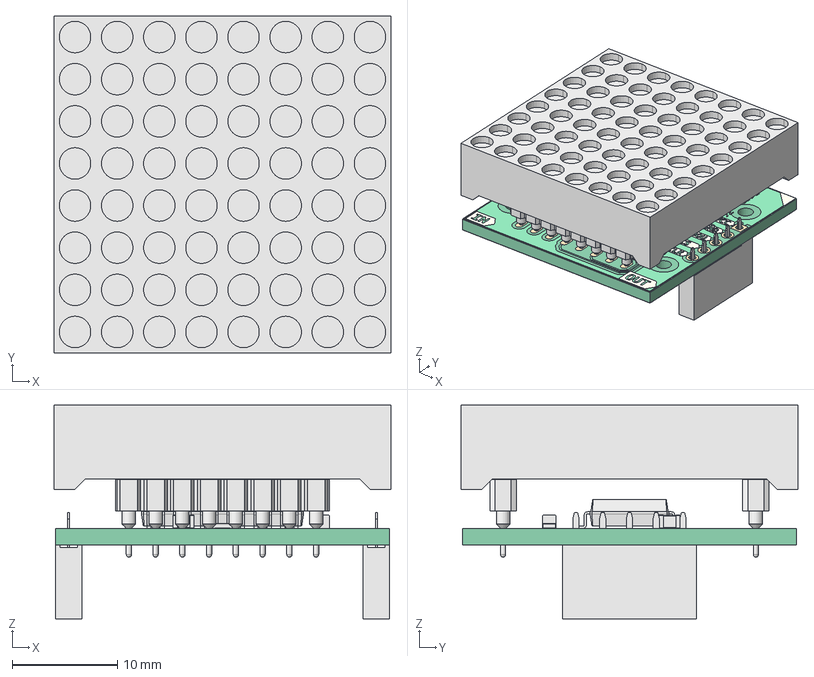
[picture p116: CAD file, 2023-06-06]
fabricate/FC-16_v1.FCStd
32.0 x 32.0 x 20.3 mm
Pcb_8d0b
topPads_8d0b
topTracks_8d0b
topZones_8d0b
botPads_8d0b
botTracks_8d0b
botZones_8d0b
botSilks_144d
topSilks_1999
C1_C_0805_2012Metric_cfb301e16dec x 2
8x8_LED_M1088AS
8x8_LED_M1088AS001
8x8_LED_M1088AS002
8x8_LED_M1088AS003
8x8_LED_M1088AS004
8x8_LED_M1088AS005
8x8_LED_M1088AS006
8x8_LED_M1088AS007
8x8_LED_M1088AS008
8x8_LED_M1088AS009
8x8_LED_M1088AS010
8x8_LED_M1088AS011
8x8_LED_M1088AS012
8x8_LED_M1088AS013
8x8_LED_M1088AS014
8x8_LED_M1088AS015
8x8_LED_M1088AS016
8x8_LED_M1088AS017
8x8_LED_M1088AS018
8x8_LED_M1088AS019
8x8_LED_M1088AS020
8x8_LED_M1088AS021
8x8_LED_M1088AS022
8x8_LED_M1088AS023
8x8_LED_M1088AS024
8x8_LED_M1088AS025
8x8_LED_M1088AS026
8x8_LED_M1088AS027
8x8_LED_M1088AS028
8x8_LED_M1088AS029
8x8_LED_M1088AS030
8x8_LED_M1088AS031
8x8_LED_M1088AS032
8x8_LED_M1088AS033
8x8_LED_M1088AS034
R1_R_0805_2012Metric_cfec1ef89428
U1_SOIC_24W_75x154mm_P127mm_1b15a27e0f1a
J1_PinSocket_1x05_P254mm_Vertical_976f558c7c31 x 2
