MakersAsylumIndia/Arcade/hardware_PCB/TheThing_v8/3D_models/PinSocket_1x02_P2.54mm_Horizontal.step

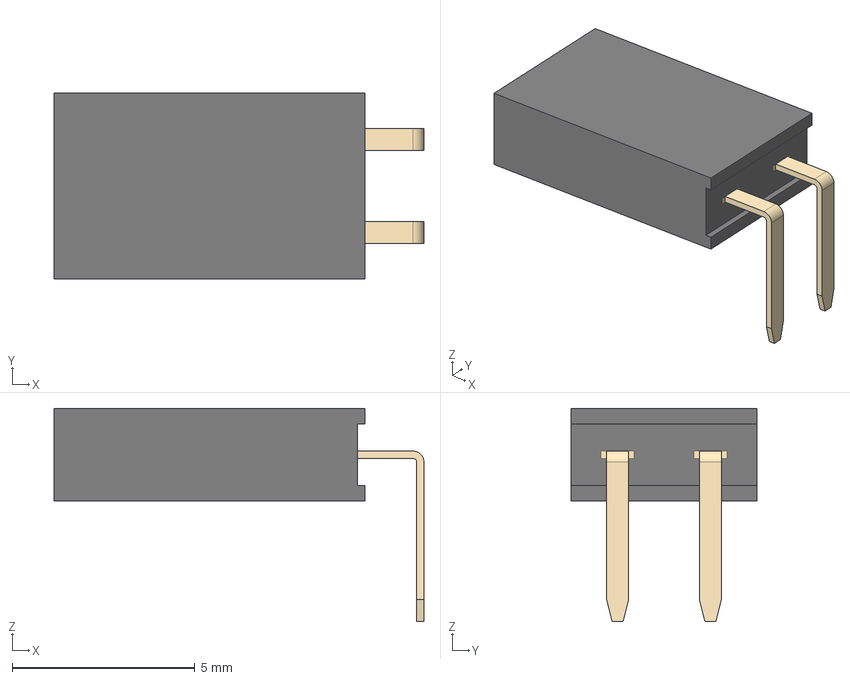
[picture p117: CAD file, 2025-08-25]
hardware_PCB/TheThing_v8/3D_models/PinSocket_1x02_P2.54mm_Horizontal.step
10.1 x 5.08 x 5.84 mm
