MakersAsylumIndia/Arcade/enclosure/3D_print/TheThing_v8-trimpot_knob_v3x50nos.3mf

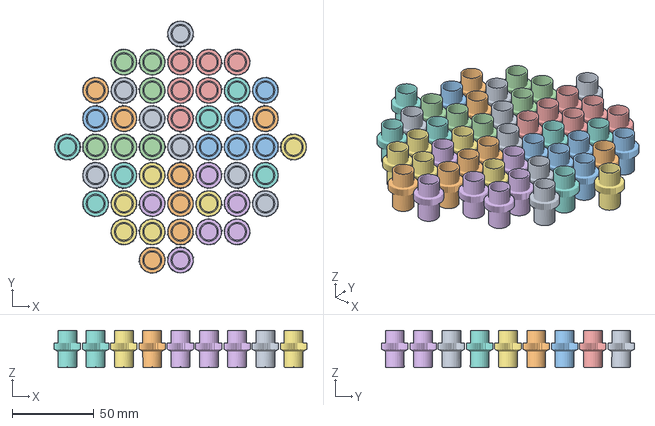
[picture p118: CAD file, 2025-11-04]
enclosure/3D_print/TheThing_v8-trimpot_knob_v3x50nos.3mf
155.1 x 155.1 x 23.0 mm
TheThing_v8-trimpot_knob_v3.stl x 50
