MakersAsylumIndia/Arcade/enclosure/footprints_for_kicad/1048 1.2in 8x8 matrix backpack.step

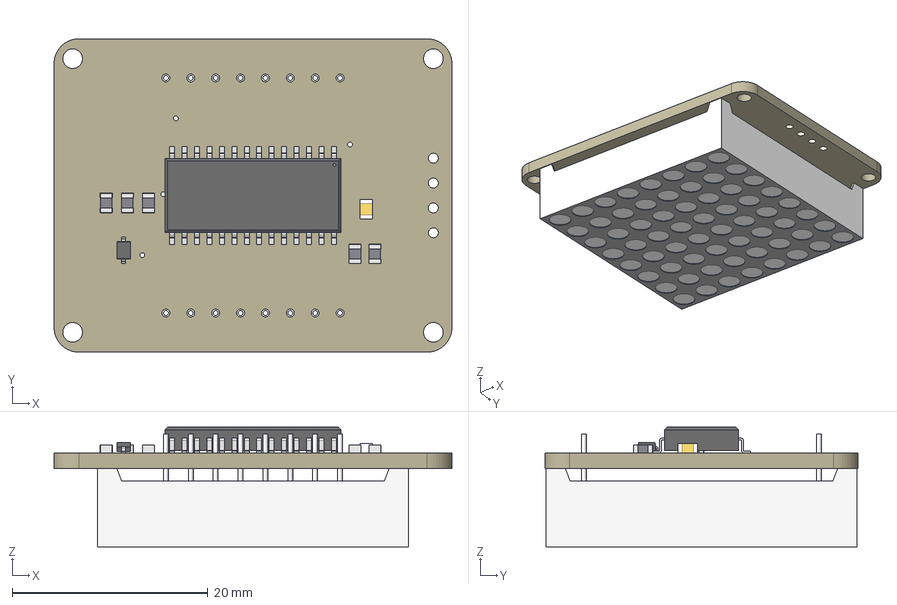
[picture p119: CAD file, 2023-04-18]
enclosure/footprints_for_kicad/1048 1.2in 8x8 matrix backpack.step
40.6 x 32.0 x 12.2 mm
Board
BL-M07C881UR
10K x 5
1N4148
10uF
SOP28_300MIL
