MakersAsylumIndia/Arcade/fabricate/DXF/TheThing_v3-PCB_plate.dxf

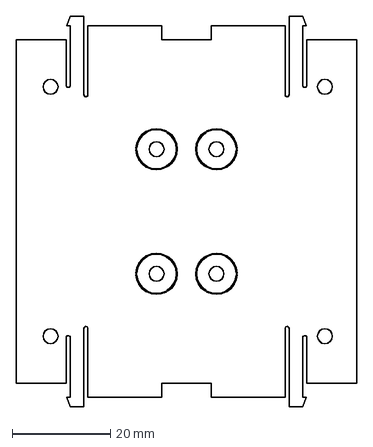
[picture p120: CAD file, 2024-11-12]
fabricate/DXF/TheThing_v3-PCB_plate.dxf
69.4 x 79.6 mm
