MakersAsylumIndia/Arcade/hardware_PCB/TheThing_v8/3D_models/PinSocket_1x03_P2.54mm_Horizontal.step

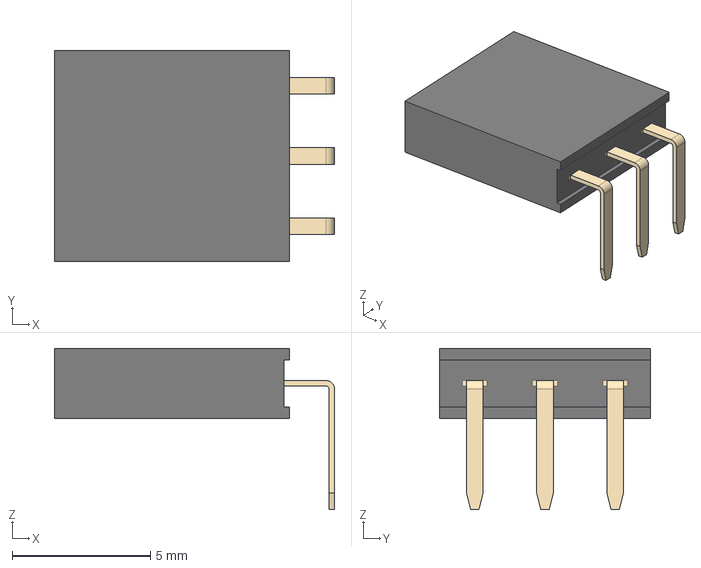
[picture p121: CAD file, 2025-08-25]
hardware_PCB/TheThing_v8/3D_models/PinSocket_1x03_P2.54mm_Horizontal.step
10.1 x 7.62 x 5.84 mm
