MakersAsylumIndia/Arcade/enclosure/3D_print/TheThing_v8-Stopper_bat.step

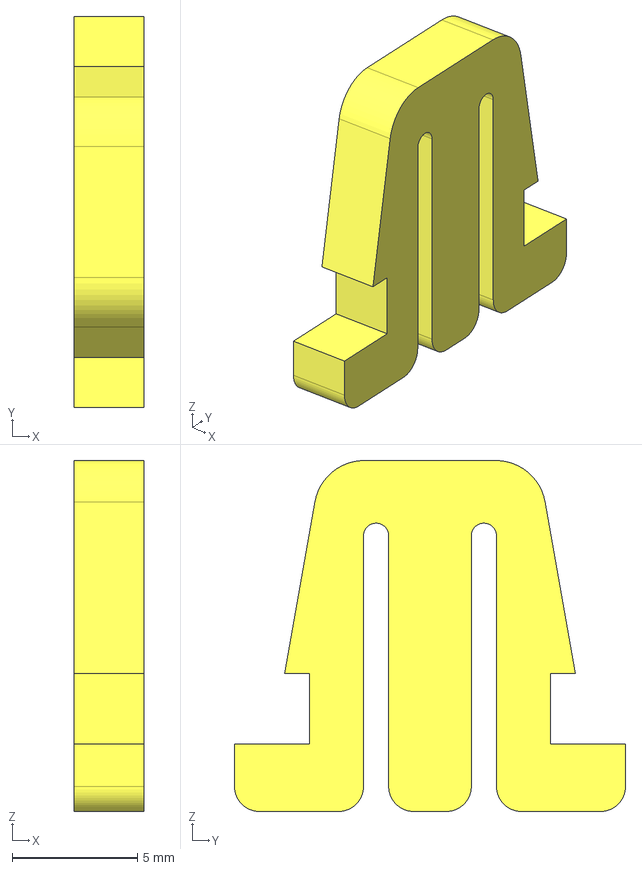
[picture p122: CAD file, 2025-10-29]
enclosure/3D_print/TheThing_v8-Stopper_bat.step
2.80 x 15.6 x 14.0 mm
