MakersAsylumIndia/Arcade/fabricate/DXF/TheThing_v3-left_clip.dxf

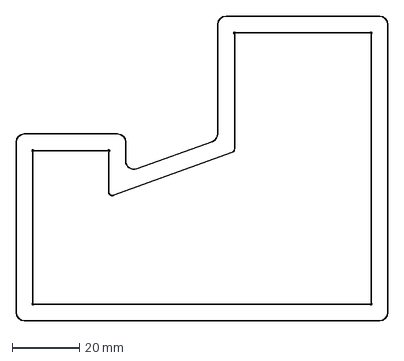
[picture p123: CAD file, 2024-11-12]
fabricate/DXF/TheThing_v3-left_clip.dxf
110.6 x 90.6 mm
