MakersAsylumIndia/Arcade/hardware_PCB/TheThing_v8/3D_models/SW_pushbutton_12mm.step

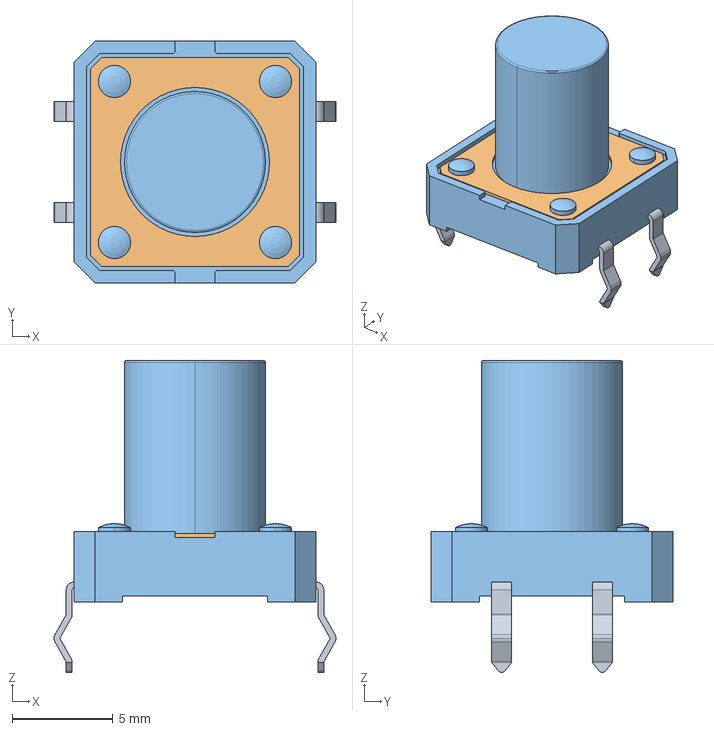
[picture p124: CAD file, 2025-08-25]
hardware_PCB/TheThing_v8/3D_models/SW_pushbutton_12mm.step
14.0 x 12.0 x 15.5 mm
