MakersAsylumIndia/Arcade/enclosure/3D_print/TheThing_v8-switch_slide.step

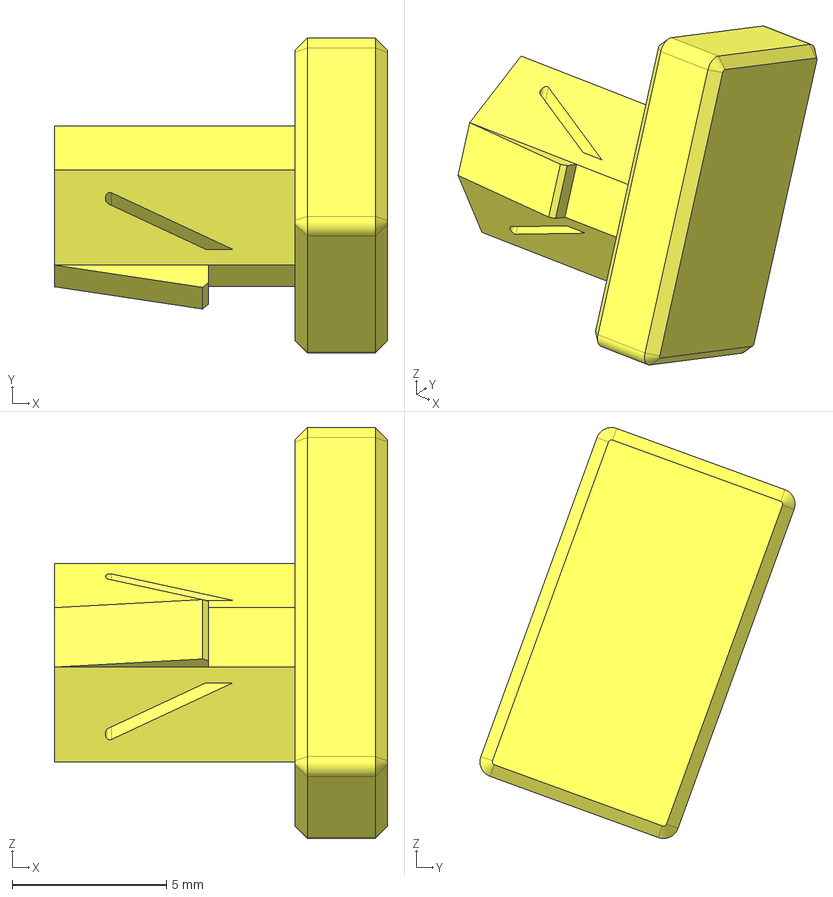
[picture p125: CAD file, 2025-10-29]
enclosure/3D_print/TheThing_v8-switch_slide.step
10.8 x 10.2 x 13.3 mm
