MakersAsylumIndia/Arcade/enclosure/footprints_for_kicad/footprint_LED_matrix_8x8_socket_v2.FCStd

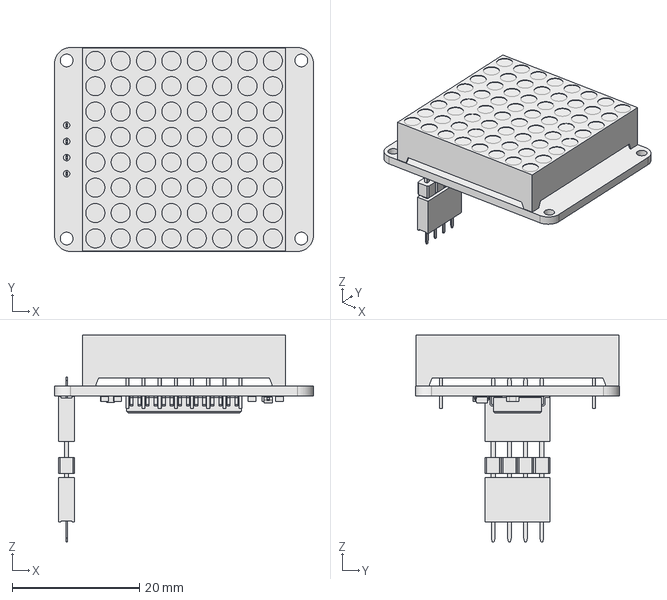
[picture p126: CAD file, 2023-04-18]
enclosure/footprints_for_kicad/footprint_LED_matrix_8x8_socket_v2.FCStd
40.6 x 32.0 x 32.4 mm
