MakersAsylumIndia/Arcade/enclosure/TheThing_v81_tabs_export_fix.FCStd

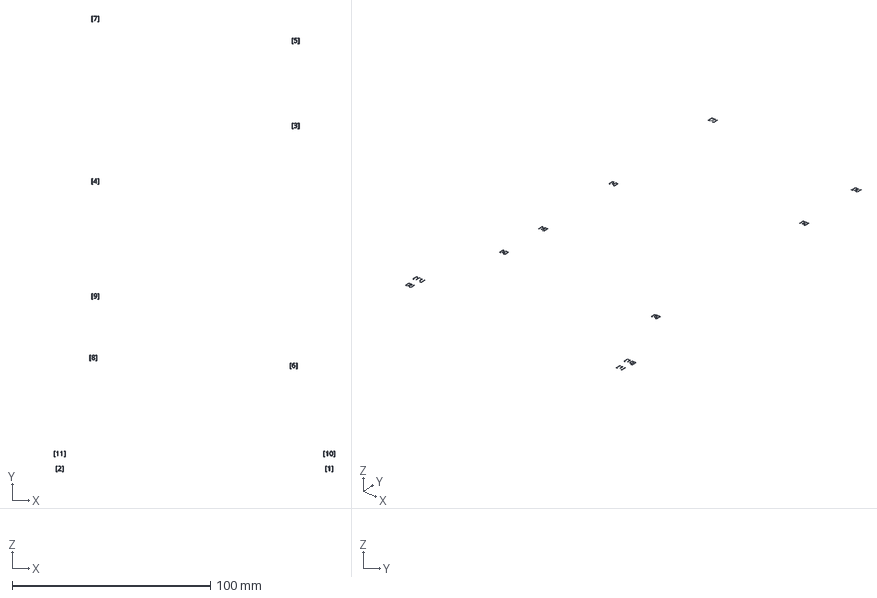
[picture p127: CAD file, 2025-11-04]
enclosure/TheThing_v81_tabs_export_fix.FCStd
141.8 x 230.1 x 0 mm
ShapeString
ShapeString001
ShapeString002
ShapeString003
ShapeString004
ShapeString005
ShapeString006
ShapeString007
ShapeString008
ShapeString009
ShapeString010
