MakersAsylumIndia/Arcade/hardware_PCB/TheThing_v8/3D_models/PinSocket_1x10_P2.54mm_Vertical.step

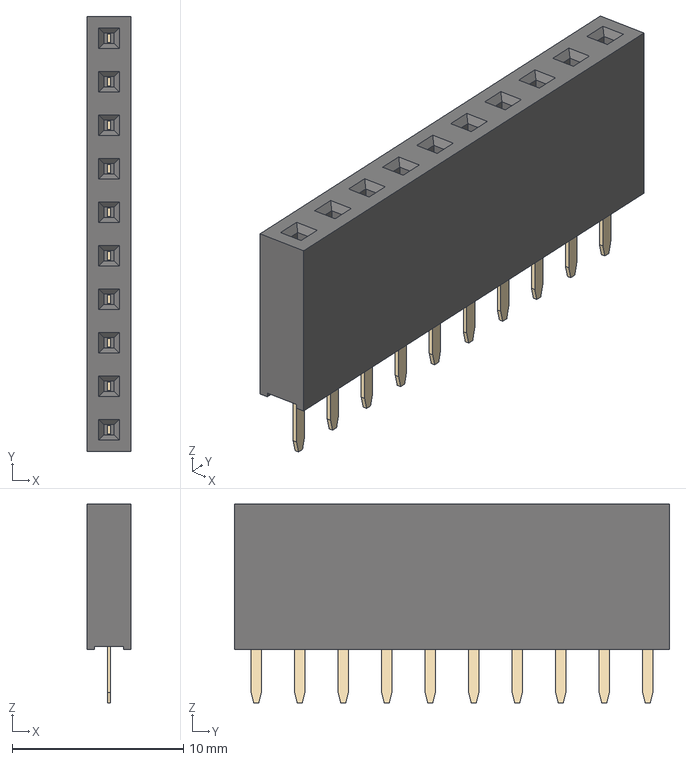
[picture p128: CAD file, 2025-08-25]
hardware_PCB/TheThing_v8/3D_models/PinSocket_1x10_P2.54mm_Vertical.step
2.54 x 25.4 x 11.6 mm
