MakersAsylumIndia/Arcade/enclosure/3D_print/TheThing_v8-Stopper_batx50nos.3mf

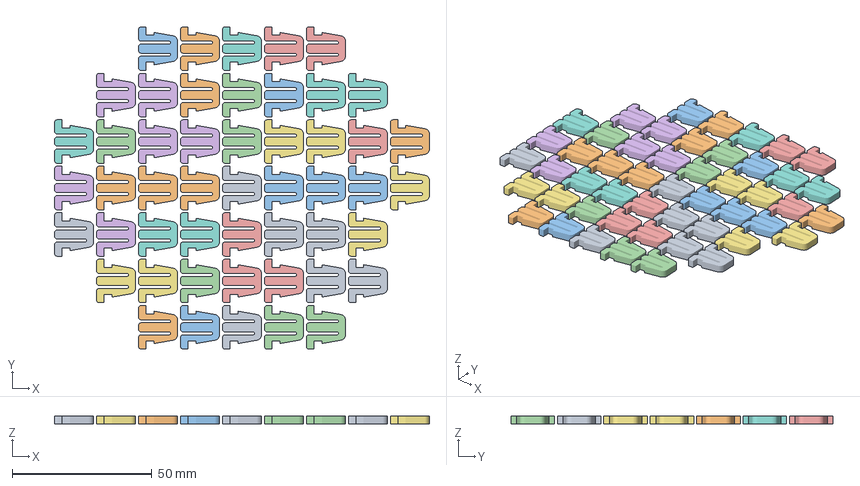
[picture p129: CAD file, 2025-10-16]
enclosure/3D_print/TheThing_v8-Stopper_batx50nos.3mf
134.0 x 115.2 x 2.80 mm
TheThing_v8-Stopper_bat.stl x 50
