MakersAsylumIndia/Arcade/enclosure/footprints_for_kicad/footprint_Arduino_Nano_V2.FCStd

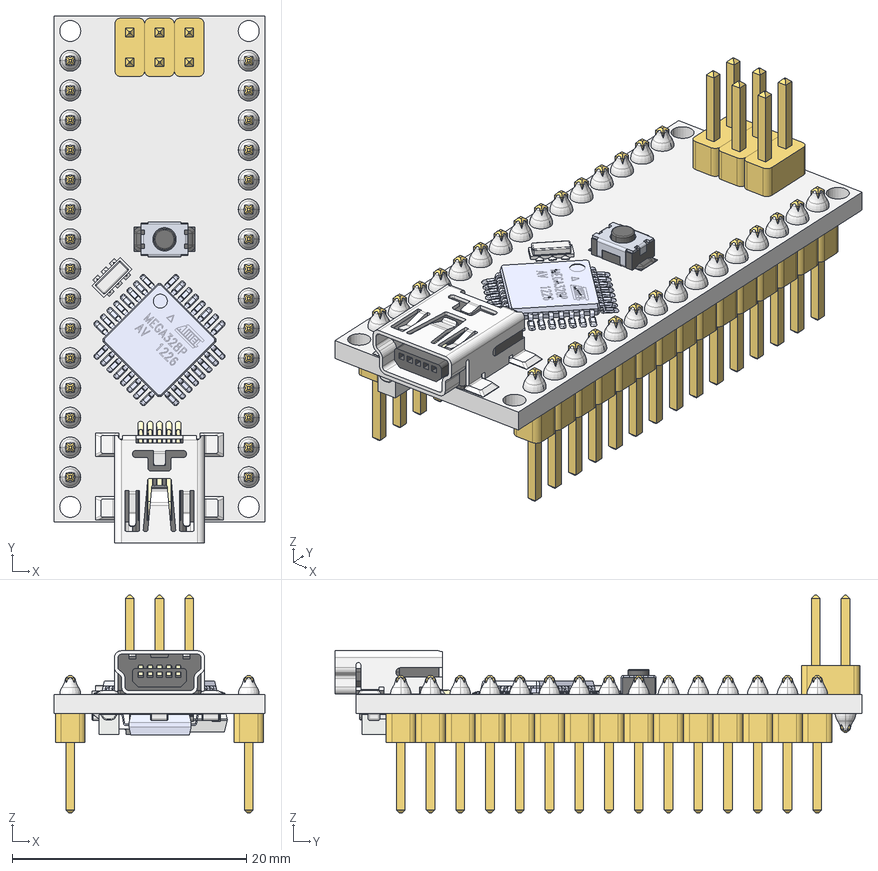
[picture p130: CAD file, 2023-04-18]
enclosure/footprints_for_kicad/footprint_Arduino_Nano_V2.FCStd
18.0 x 45.0 x 18.6 mm
nano-board
2pin_header__02 x 3
15pin_header__ x 2
atmega328
ftdi FT232rl
smt_resistor222 x 5
16mhz crystal - measured
MINIUSBSHELL
MINIUSBCORE
MINI USB CONTACT x 5
cap106C x 2
reset core
reset shell
nano - reg
NANO DIODE
