MakersAsylumIndia/Arcade/enclosure/TheThing_v81_multiJoin_parts.FCStd

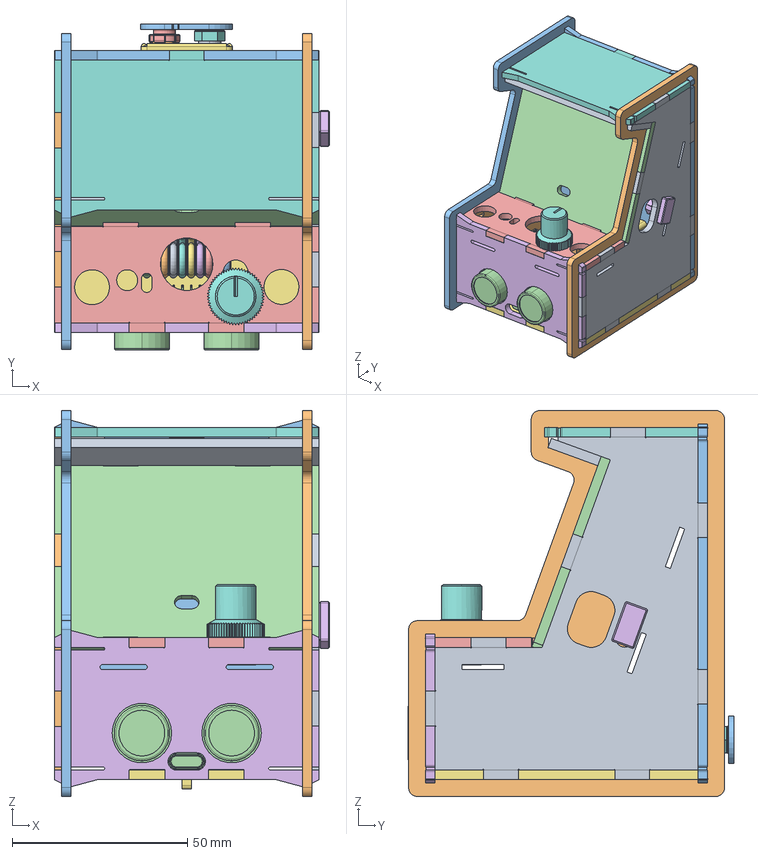
[picture p131: CAD file, 2025-11-04]
enclosure/TheThing_v81_multiJoin_parts.FCStd
78.6 x 93.1 x 110.2 mm
Pad001_tab
Pad002_tab
Pocket_tab
Pocket016_tab
Pad018_tab
Pocket017_tab
Pocket021_tab
Fillet_tab
Pad016_tab
Body_right_clip_tab
Body_left_clip_tab
hc-sr04
User Library-9V Duracell Battery
User Library-9V Duracell Battery001
User Library-9V Duracell Battery002
User Library-9V Duracell Battery003
User Library-9V Duracell Battery004
User Library-9V Duracell Battery005
_68005_cp005_cp
_68005_cp005_cp003
_68005_cp005_cp004
switch_slide
Stopper_bat
trimpot_knob_v3
PinSocket_1x10_P2.54mm_Vertical
PinSocket_1x10_P2.54mm_Vertical001
Cable_flat_10x
