MakersAsylumIndia/Arcade/enclosure/footprints_for_kicad/footprint_Arduino_Nano.FCStd

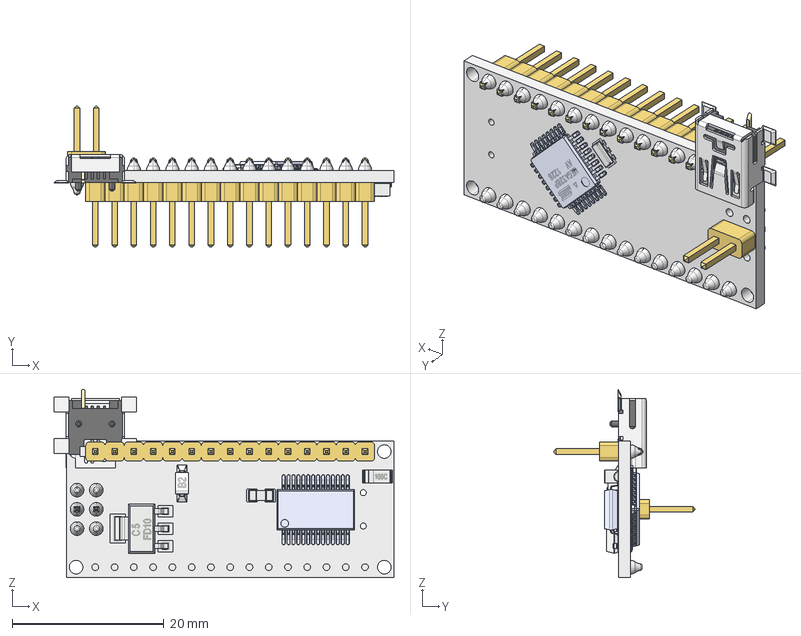
[picture p132: CAD file, 2023-04-18]
enclosure/footprints_for_kicad/footprint_Arduino_Nano.FCStd
44.8 x 18.6 x 24.8 mm
nano-board
2pin_header__02
15pin_header__
atmega328
ftdi FT232rl
smt_resistor222
16mhz crystal - measured
MINIUSBSHELL
MINIUSBCORE
MINI USB CONTACT
cap106C
reset core
reset shell
nano - reg
NANO DIODE
