MakersAsylumIndia/Arcade/enclosure/footprints_for_kicad/footprint_LED_matrix_8x8_socket.FCStd

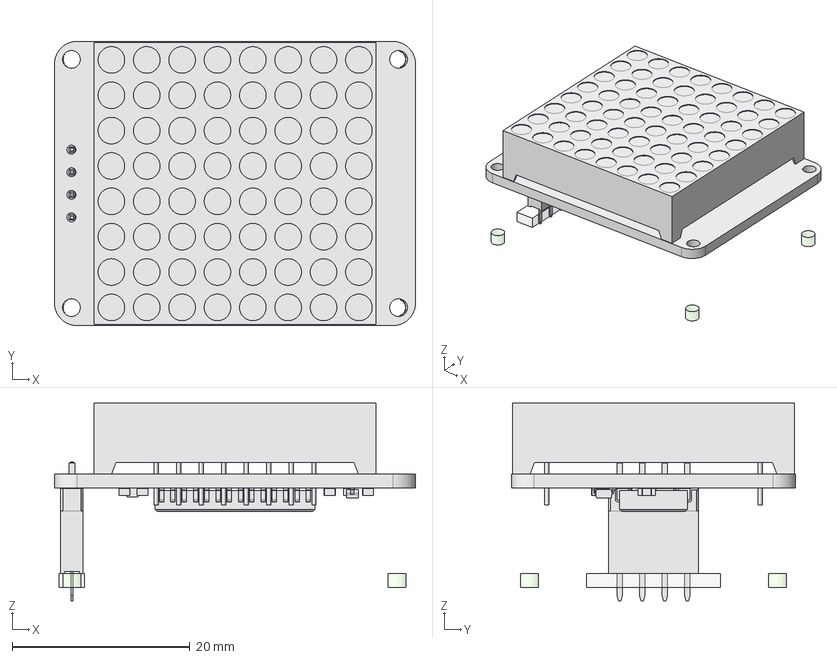
[picture p134: CAD file, 2023-04-18]
enclosure/footprints_for_kicad/footprint_LED_matrix_8x8_socket.FCStd
40.6 x 32.0 x 22.3 mm
TopPads
BotPads
PTHs
Pcb
Adafruit_1_2inch_8x8_backpack_v2_cp001_sp
