MakersAsylumIndia/Arcade/hardware_PCB/TheThing_v8/3D_models/TO-92.step

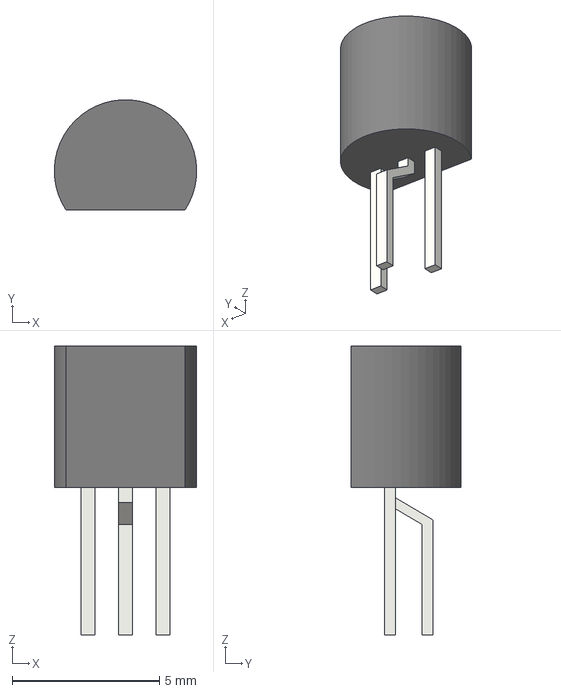
[picture p136: CAD file, 2025-05-09]
hardware_PCB/TheThing_v8/3D_models/TO-92.step
4.83 x 3.74 x 9.80 mm
