MakersAsylumIndia/Arcade/enclosure/TheThing_v8-trimpot_knob.step

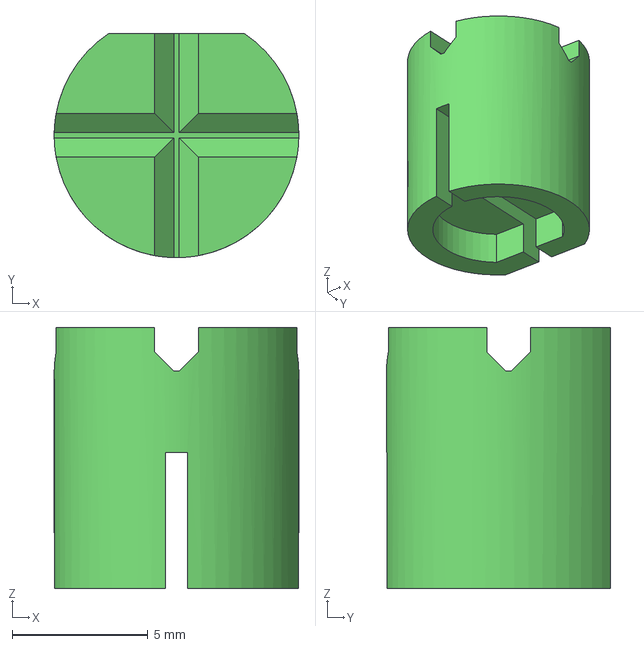
[picture p137: CAD file, 2025-08-25]
enclosure/TheThing_v8-trimpot_knob.step
9.00 x 8.25 x 9.60 mm
