MakersAsylumIndia/Arcade/hardware_PCB/TheThing_v8/3D_models/Buzzer_12x9.5RM7.6.step

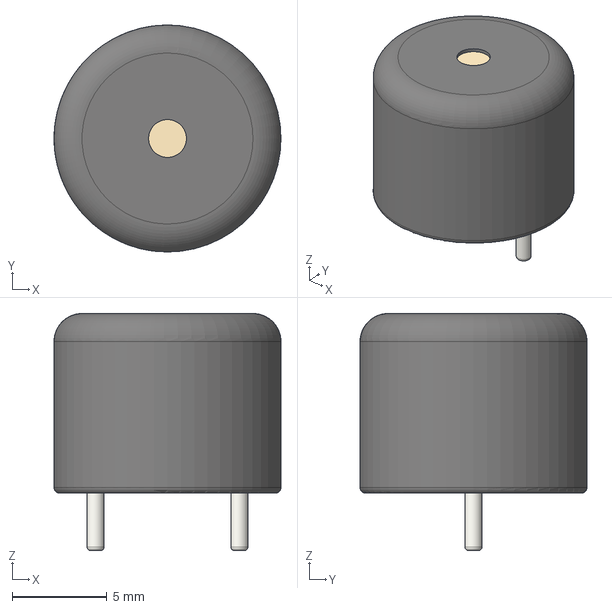
[picture p138: CAD file, 2025-05-09]
hardware_PCB/TheThing_v8/3D_models/Buzzer_12x9.5RM7.6.step
12.0 x 12.0 x 12.5 mm
