MakersAsylumIndia/Arcade/enclosure/TheThing_v8_addon.step

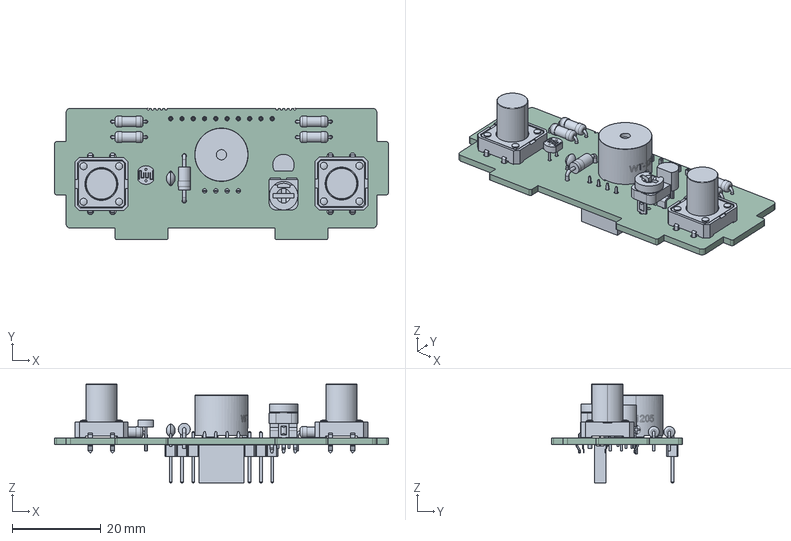
[picture p139: CAD file, 2025-08-25]
enclosure/TheThing_v8_addon.step
75.2 x 29.6 x 22.3 mm
R_Axial_DIN0207_L6.3mm_D2.5mm_P7.62mm_Horizontal x 4
SW_TS14-1212-120-BK-160-SCR-D x 2
R_LDR_4.2x3.5mm_P2.54mm_Vertical
Trimpot_THT
C_Disc_D3.0mm_W2.0mm_P2.50mm
TO-92
D_DO-41_SOD81_P10.16mm_Horizontal
Buzzer_D12_P6.5_WT-1205
PinSocket_1x04_P2.54mm_Vertical
PinHeader_1x10_P2.54mm_Vertical
TheThing_addon_PCB
