MakersAsylumIndia/Arcade/hardware_PCB/TheThing_v8/3D_models/C_Disc_D3.0mm_W2.0mm_P2.50mm.step

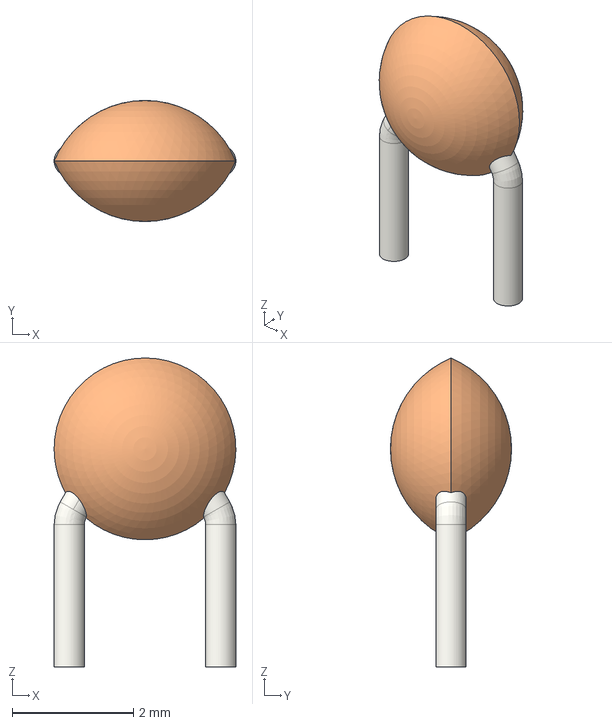
[picture p140: CAD file, 2025-05-09]
hardware_PCB/TheThing_v8/3D_models/C_Disc_D3.0mm_W2.0mm_P2.50mm.step
3.00 x 2.00 x 5.10 mm
