MakersAsylumIndia/Arcade/enclosure/9V Duracell Battery.step

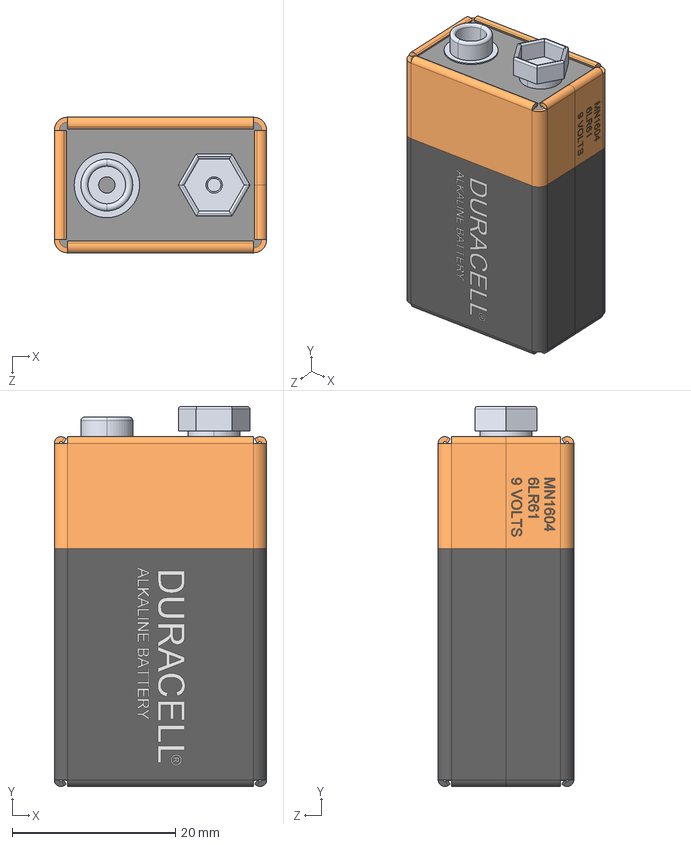
[picture p141: CAD file, 2025-05-09]
enclosure/9V Duracell Battery.step
26.0 x 46.5 x 16.6 mm
