MakersAsylumIndia/Arcade/hardware_PCB/TheThing_v8/3D_models/POT_3352T-1-253LF.step

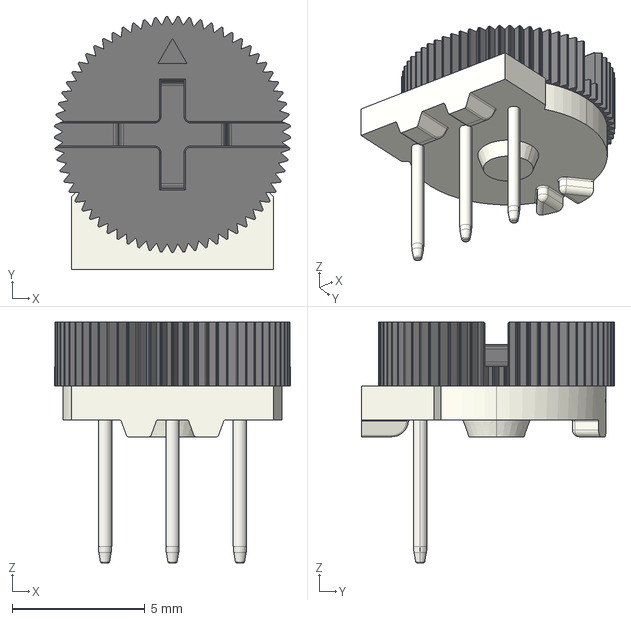
[picture p142: CAD file, 2025-05-09]
hardware_PCB/TheThing_v8/3D_models/POT_3352T-1-253LF.step
8.89 x 9.52 x 9.07 mm
