MakersAsylumIndia/Arcade/hardware_PCB/TheThing_v8/3D_models/PinHeader_1x10_P2.54mm_Vertical.step

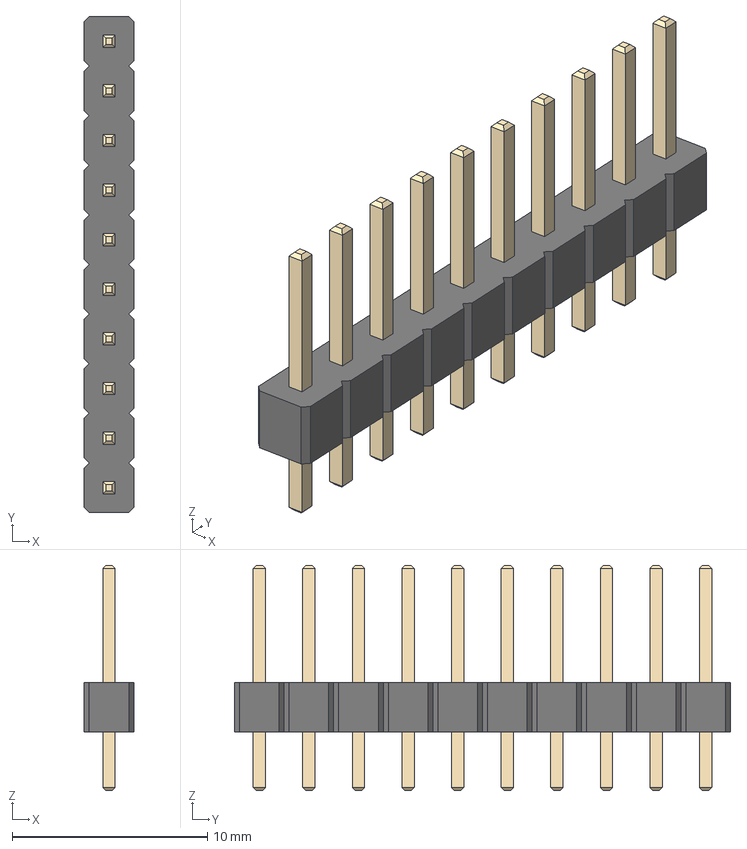
[picture p144: CAD file, 2025-05-09]
hardware_PCB/TheThing_v8/3D_models/PinHeader_1x10_P2.54mm_Vertical.step
2.54 x 25.4 x 11.5 mm
