MakersAsylumIndia/Arcade/hardware_PCB/TheThing_v8/3D_models/SW_CuK_OS102011MA1QN1_SPDT_Angled.step

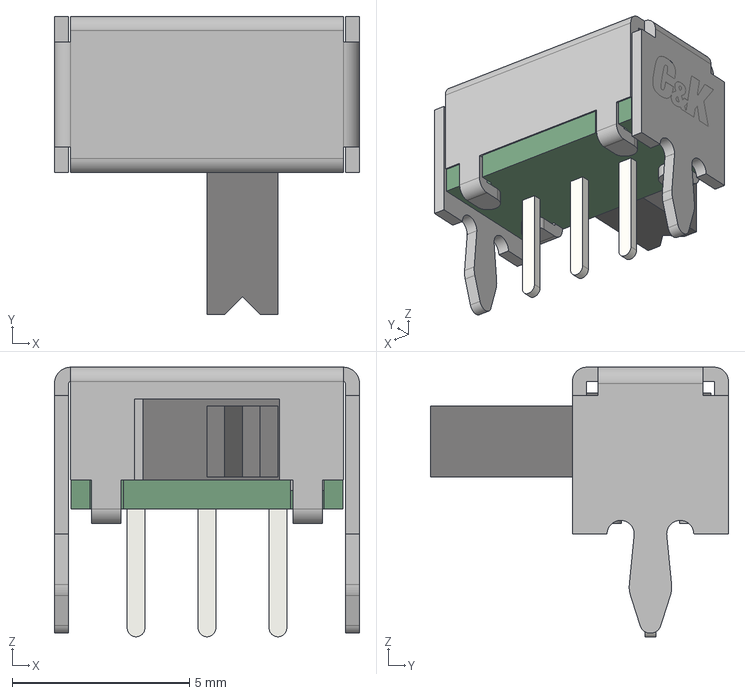
[picture p145: CAD file, 2025-05-09]
hardware_PCB/TheThing_v8/3D_models/SW_CuK_OS102011MA1QN1_SPDT_Angled.step
8.60 x 8.40 x 7.60 mm
