MakersAsylumIndia/Arcade/hardware_PCB/TheThing_v8/3D_models/SW_TS02-66-70-BK-160-LCR-D.step

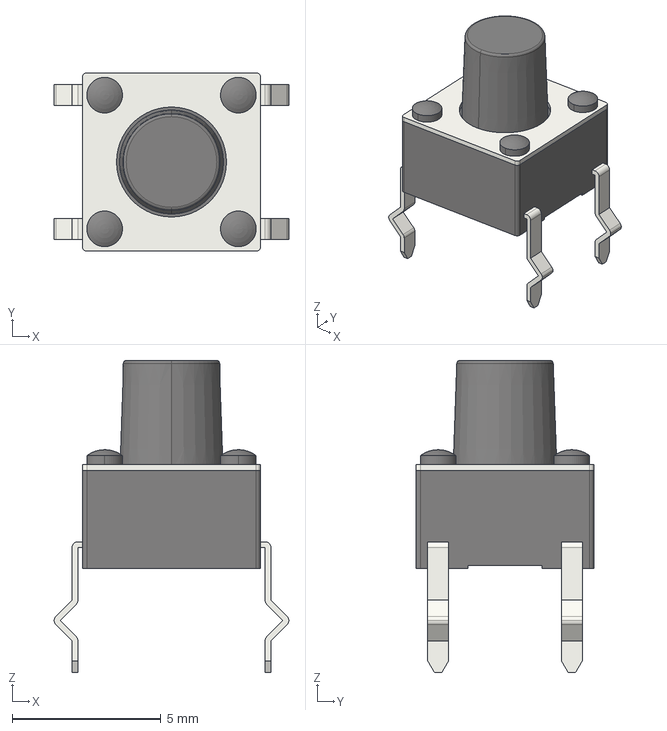
[picture p147: CAD file, 2025-05-09]
hardware_PCB/TheThing_v8/3D_models/SW_TS02-66-70-BK-160-LCR-D.step
7.90 x 6.00 x 10.5 mm
