MakersAsylumIndia/Arcade/hardware_PCB/TheThing_v8/3D_models/Buzzer_D12_P6.5_WT-1205.step

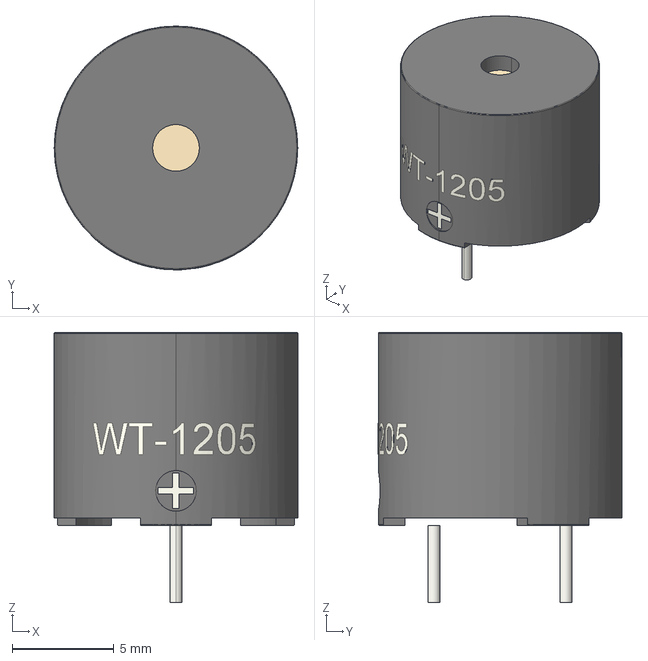
[picture p148: CAD file, 2025-05-09]
hardware_PCB/TheThing_v8/3D_models/Buzzer_D12_P6.5_WT-1205.step
12.0 x 12.0 x 13.3 mm
