MakersAsylumIndia/Arcade/hardware_PCB/TheThing_v8/3D_models/PinSocket_1x05_P2.54mm_Vertical.step

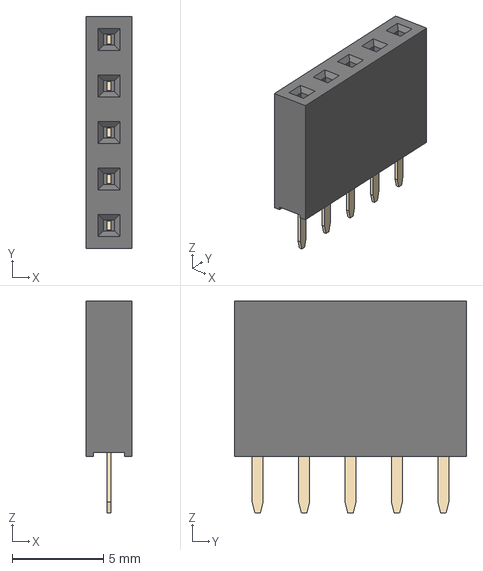
[picture p149: CAD file, 2025-05-09]
hardware_PCB/TheThing_v8/3D_models/PinSocket_1x05_P2.54mm_Vertical.step
2.54 x 12.7 x 11.6 mm
