MakersAsylumIndia/Arcade/hardware_PCB/TheThing_v8/3D_models/Display_OLED-1_3-128X64.step

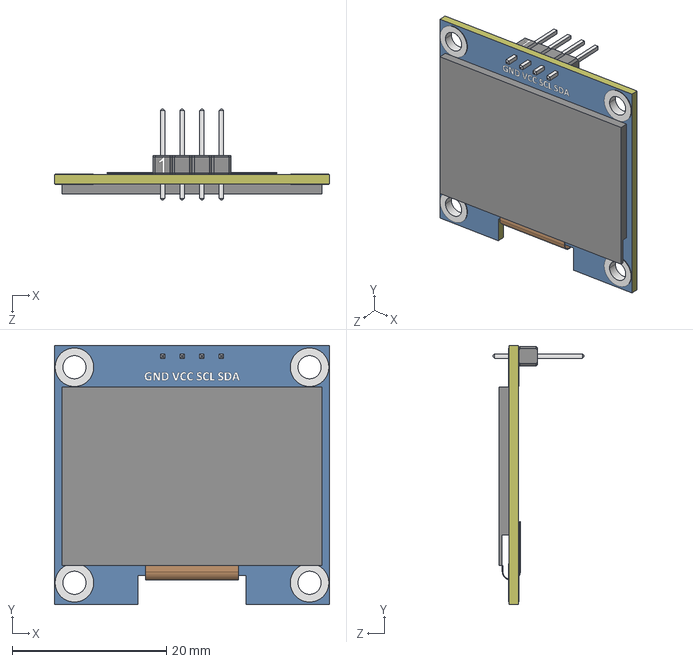
[picture p150: CAD file, 2025-05-09]
hardware_PCB/TheThing_v8/3D_models/Display_OLED-1_3-128X64.step
35.6 x 33.6 x 11.8 mm
