MakersAsylumIndia/Arcade/hardware_PCB/TheThing_v8/3D_models/R_LDR_4.2x3.5mm_P2.54mm_Vertical.step

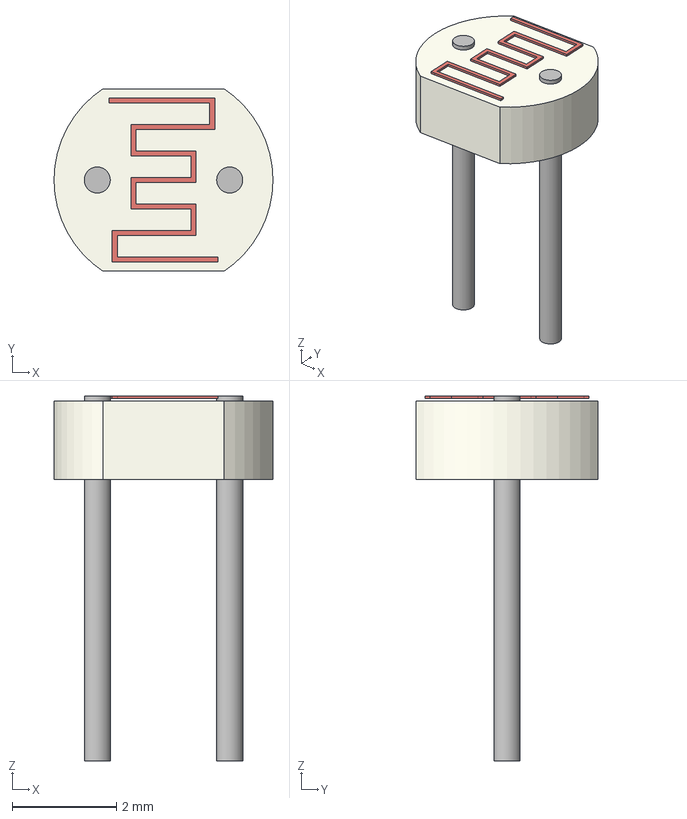
[picture p151: CAD file, 2025-02-07]
hardware_PCB/TheThing_v8/3D_models/R_LDR_4.2x3.5mm_P2.54mm_Vertical.step
4.20 x 3.50 x 7.00 mm
