MakersAsylumIndia/Arcade/hardware_PCB/TheThing_v8/3D_models/PinHeader_1x03_P2.54mm_Vertical.step

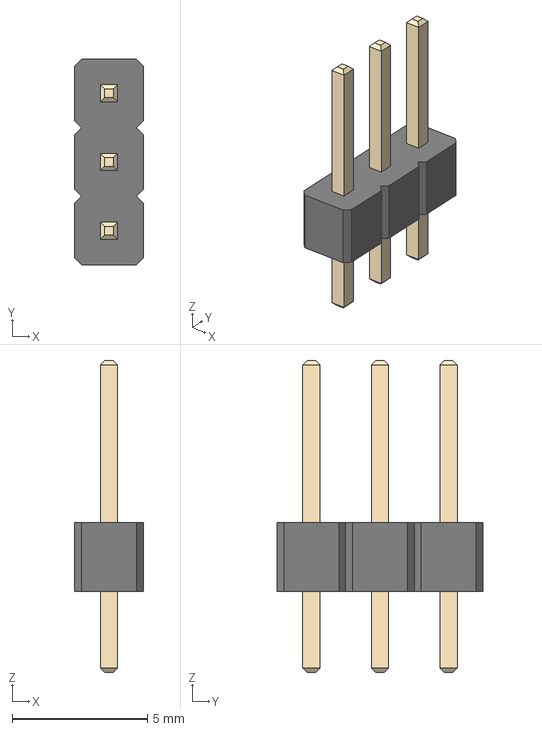
[picture p152: CAD file, 2024-05-09]
hardware_PCB/TheThing_v8/3D_models/PinHeader_1x03_P2.54mm_Vertical.step
2.54 x 7.62 x 11.5 mm
