MakersAsylumIndia/Arcade/hardware_PCB/TheThing_v8/3D_models/PinHeader_1x04_P2.54mm_Vertical.step

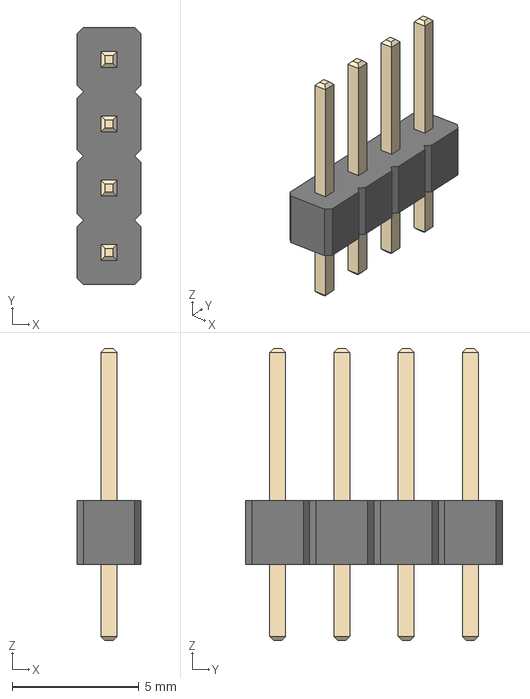
[picture p153: CAD file, 2023-06-06]
hardware_PCB/TheThing_v8/3D_models/PinHeader_1x04_P2.54mm_Vertical.step
2.54 x 10.2 x 11.5 mm
