MakersAsylumIndia/Arcade/hardware_PCB/TheThing_v8/3D_models/D_DO-41_SOD81_P10.16mm_Horizontal.step

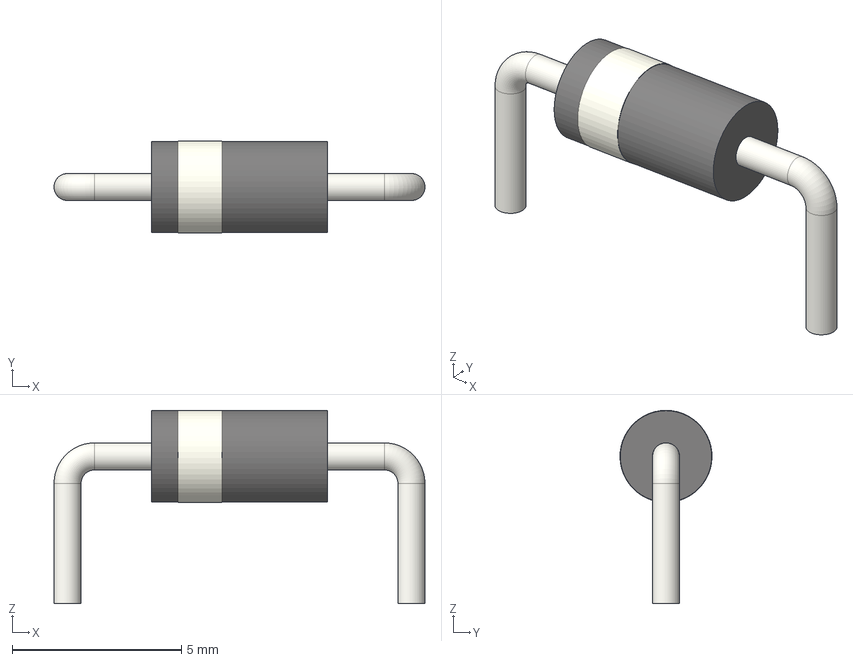
[picture p156: CAD file, 2023-04-18]
hardware_PCB/TheThing_v8/3D_models/D_DO-41_SOD81_P10.16mm_Horizontal.step
11.0 x 2.72 x 5.71 mm
