MakersAsylumIndia/Arcade/hardware_PCB/TheThing_v8/3D_models/pp3_battery.step

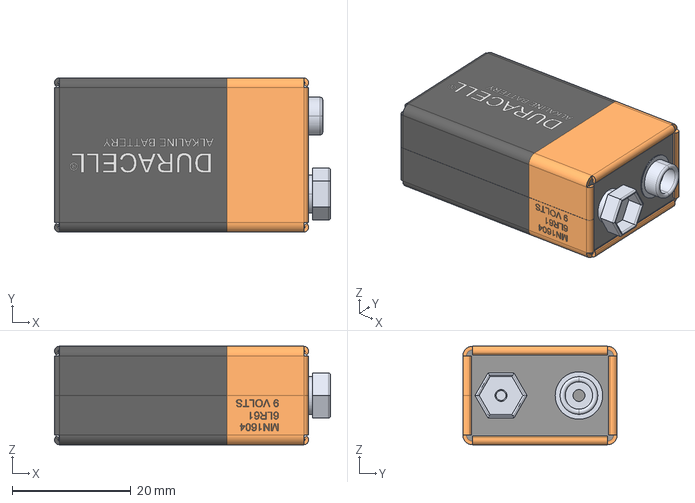
[picture p158: CAD file, 2023-04-18]
hardware_PCB/TheThing_v8/3D_models/pp3_battery.step
46.5 x 26.0 x 16.6 mm
