MakersAsylumIndia/Arcade/hardware_PCB/TheThing_v8/3D_models/LED_matrix_8x8_socket.step

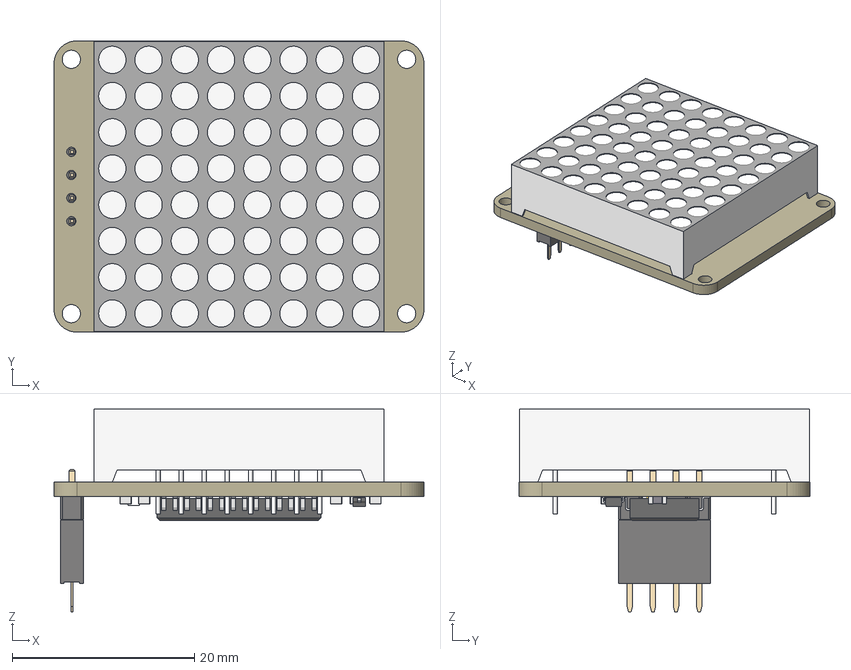
[picture p159: CAD file, 2023-04-18]
hardware_PCB/TheThing_v8/3D_models/LED_matrix_8x8_socket.step
40.6 x 32.0 x 22.3 mm
