MakersAsylumIndia/Arcade/hardware_PCB/TheThing_v8/3D_models/PinHeader_1x01_P2.54mm_Vertical.step

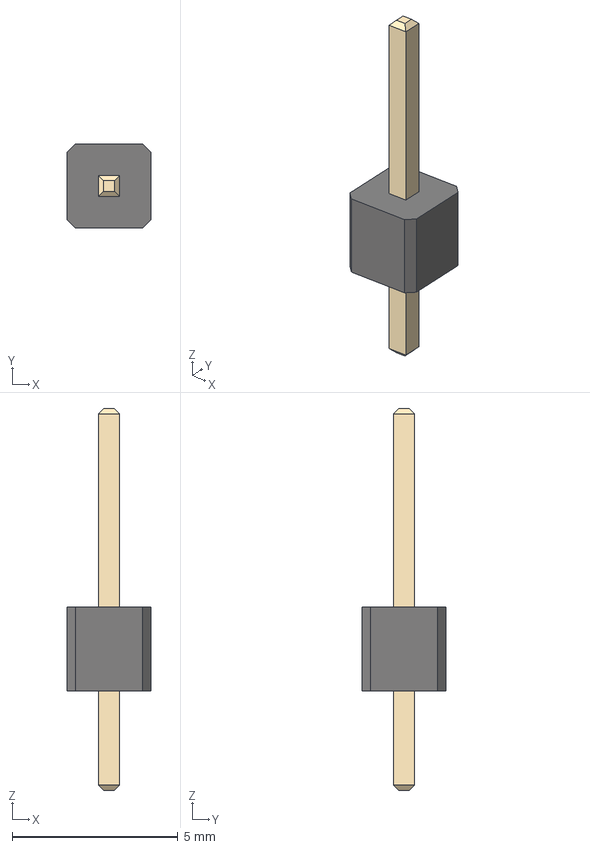
[picture p160: CAD file, 2023-04-18]
hardware_PCB/TheThing_v8/3D_models/PinHeader_1x01_P2.54mm_Vertical.step
2.54 x 2.54 x 11.5 mm
