MakersAsylumIndia/Arcade/datasheets/makebreakcreate.png

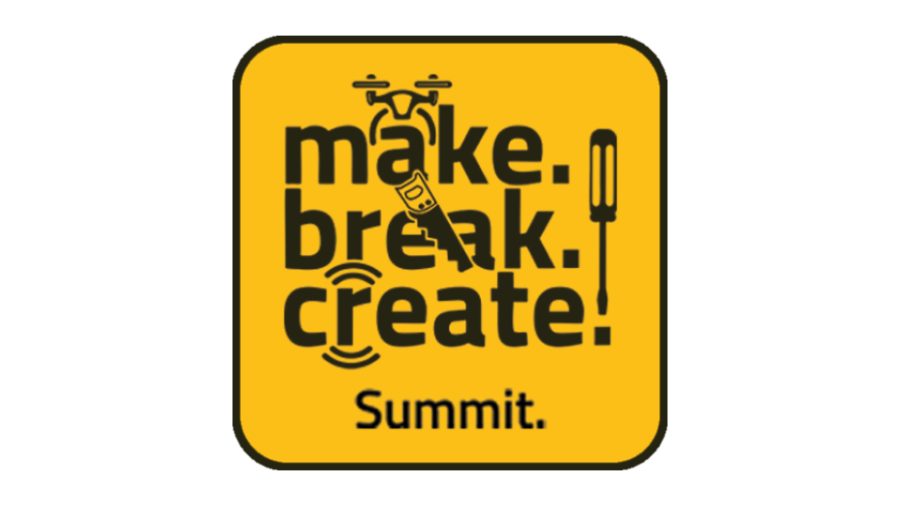
datasheets/makebreakcreate.png
