MakersAsylumIndia/Arcade/documentation/renders_for_user_guide/Arcade_01.png

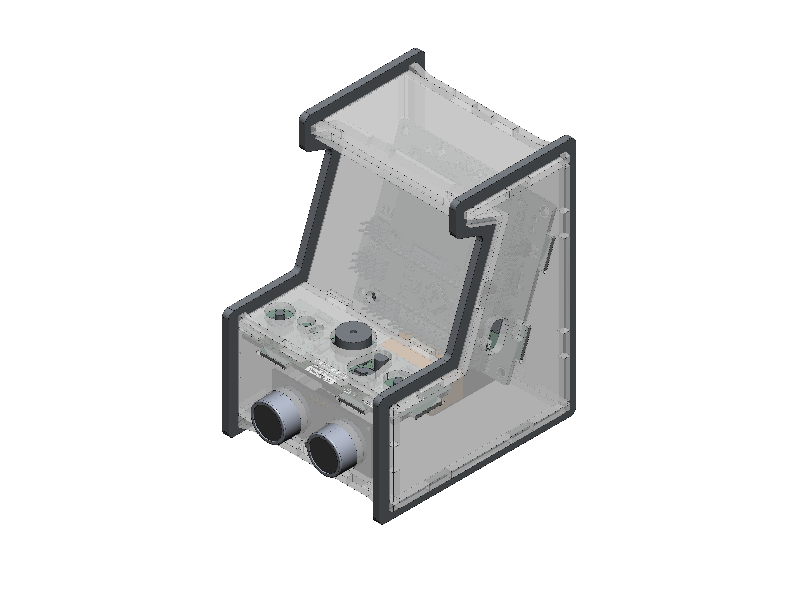
documentation/renders_for_user_guide/Arcade_01.png
