MakersAsylumIndia/Arcade/documentation/renders_for_user_guide/Arcade_02.png

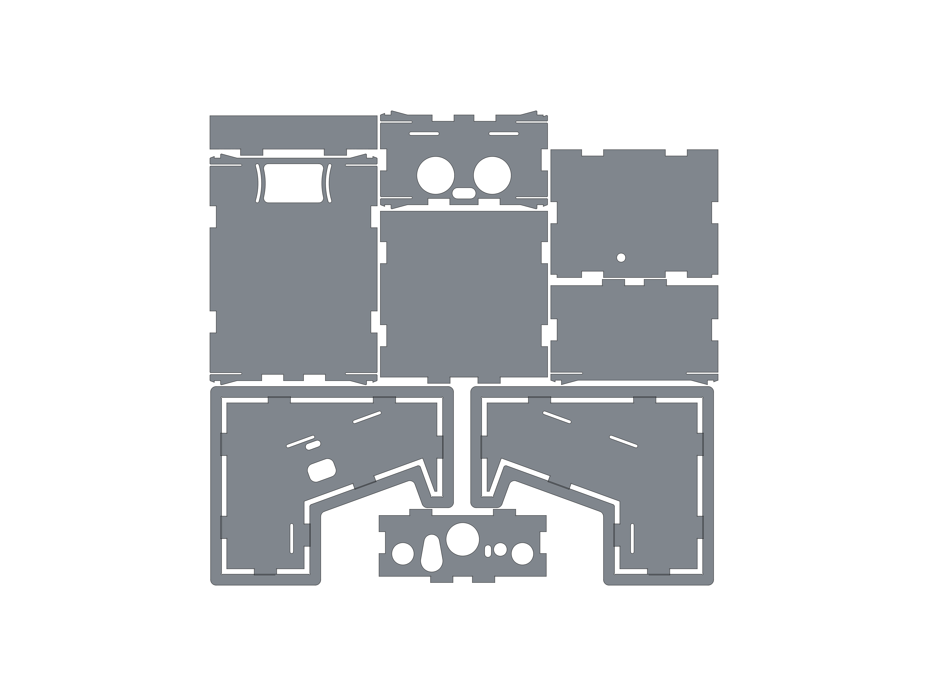
documentation/renders_for_user_guide/Arcade_02.png
