MakersAsylumIndia/Arcade/enclosure/images_user_guide/01a.png

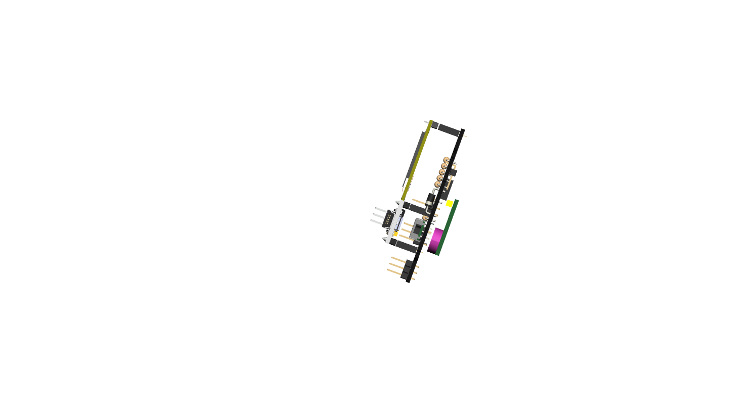
enclosure/images_user_guide/01a.png
