MakersAsylumIndia/Arcade/enclosure/images_user_guide/01c.png

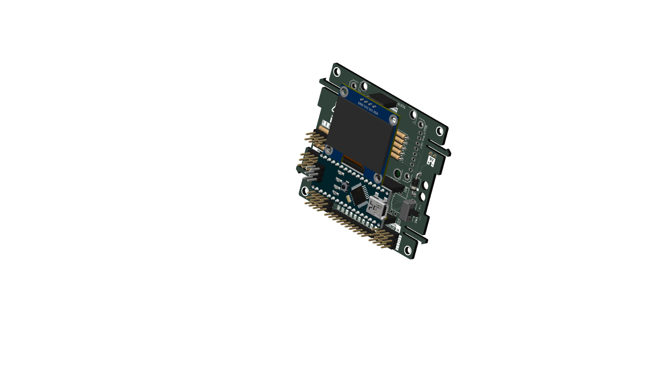
enclosure/images_user_guide/01c.png
