MakersAsylumIndia/Arcade/enclosure/images_user_guide/02b.png

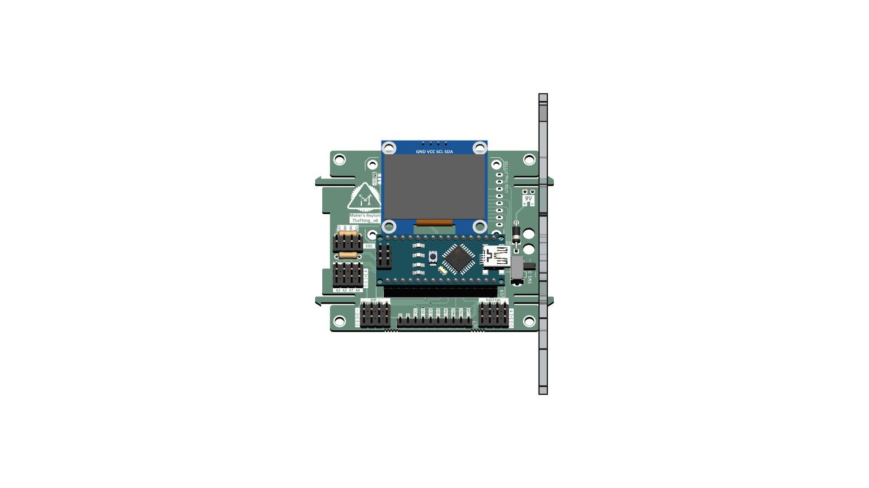
enclosure/images_user_guide/02b.png
