MakersAsylumIndia/Arcade/enclosure/images_user_guide/02c.png

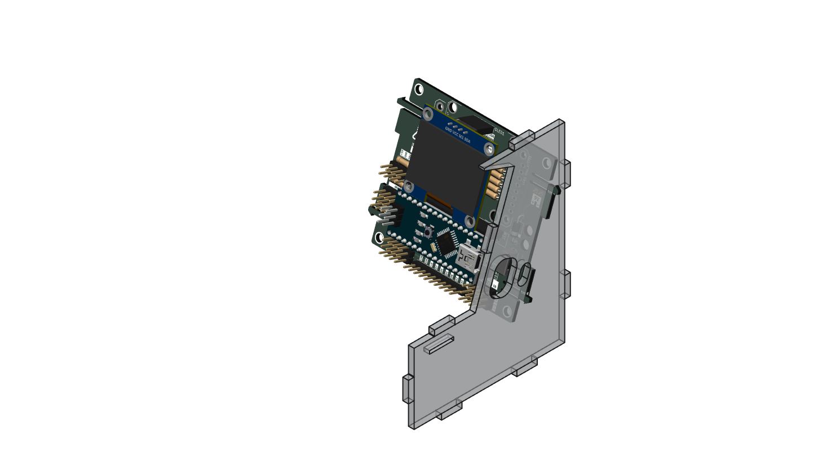
enclosure/images_user_guide/02c.png
