MakersAsylumIndia/Arcade/enclosure/images_user_guide/04a.png

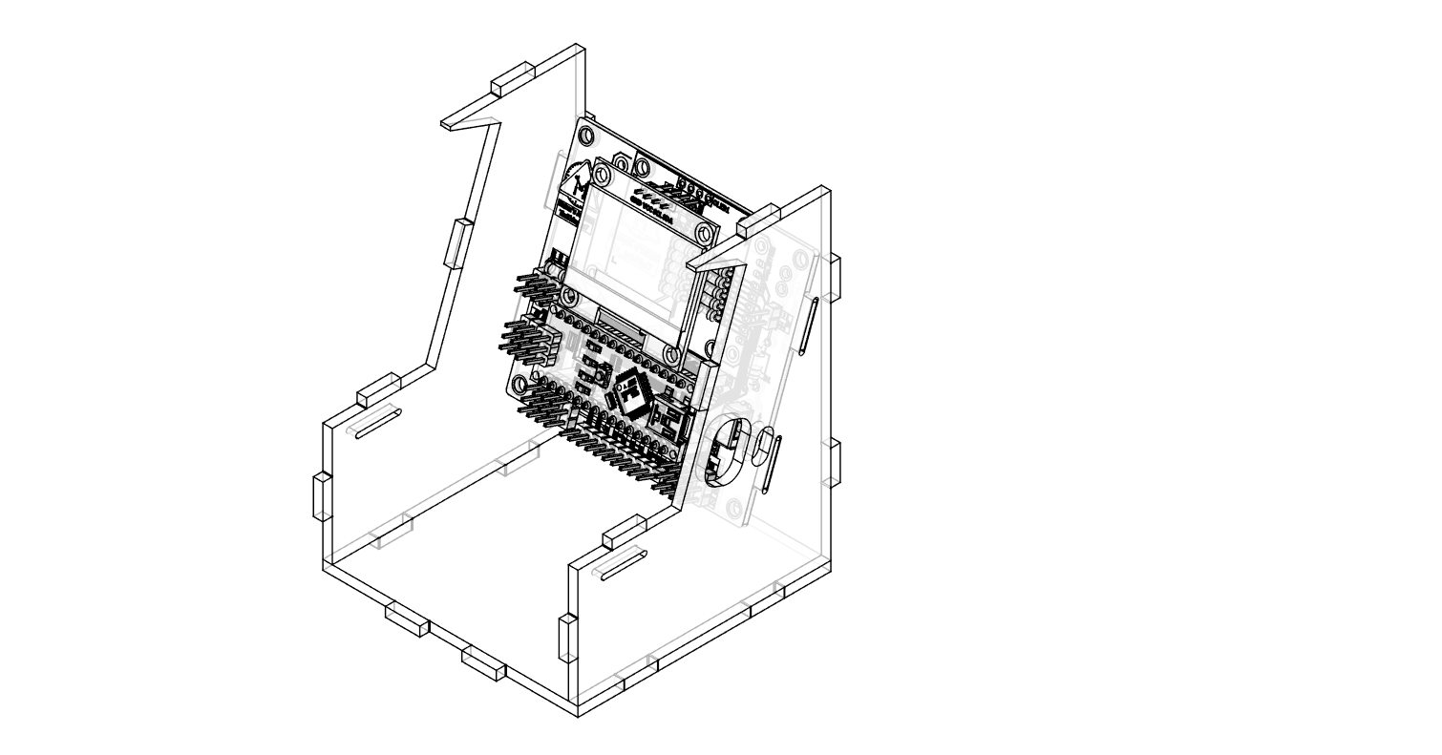
enclosure/images_user_guide/04a.png
