MakersAsylumIndia/Arcade/enclosure/images_user_guide/04b.png

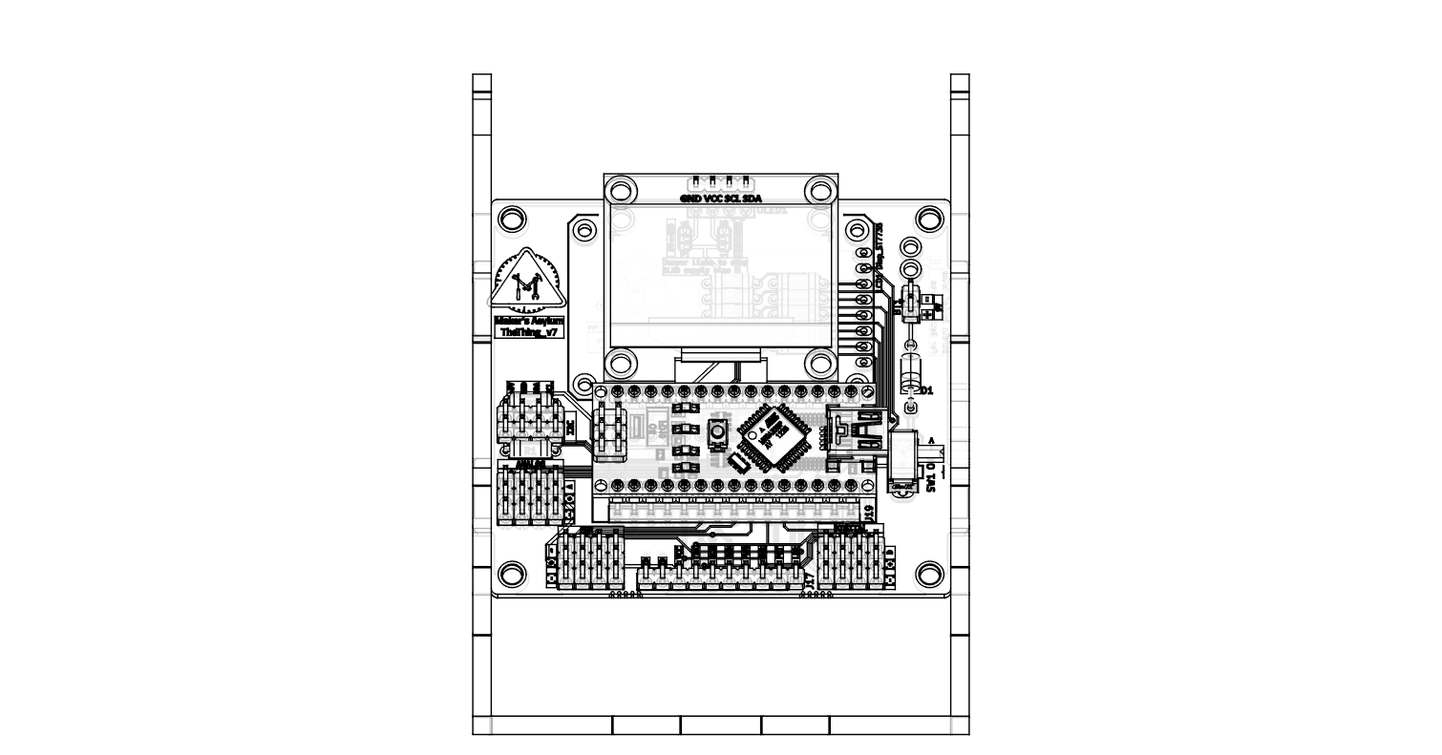
enclosure/images_user_guide/04b.png
