MakersAsylumIndia/Arcade/enclosure/images_user_guide/04c.png

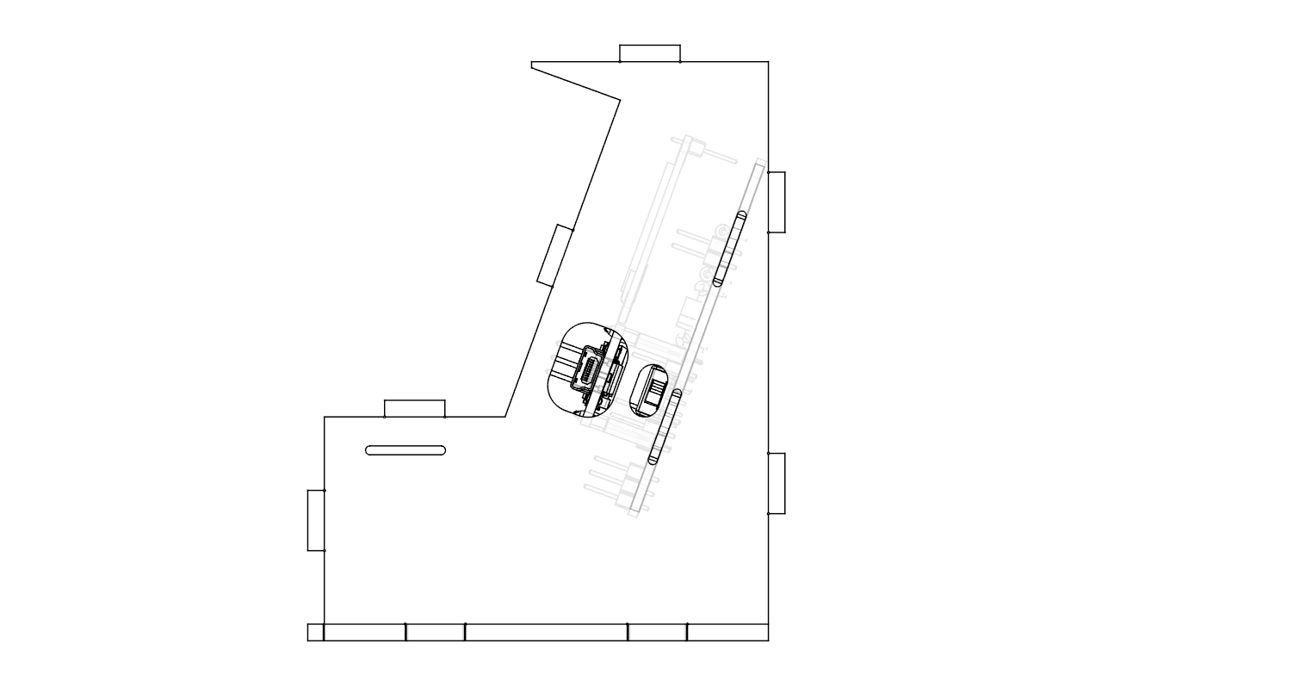
enclosure/images_user_guide/04c.png
