MakersAsylumIndia/Arcade/enclosure/images_user_guide/05a.png

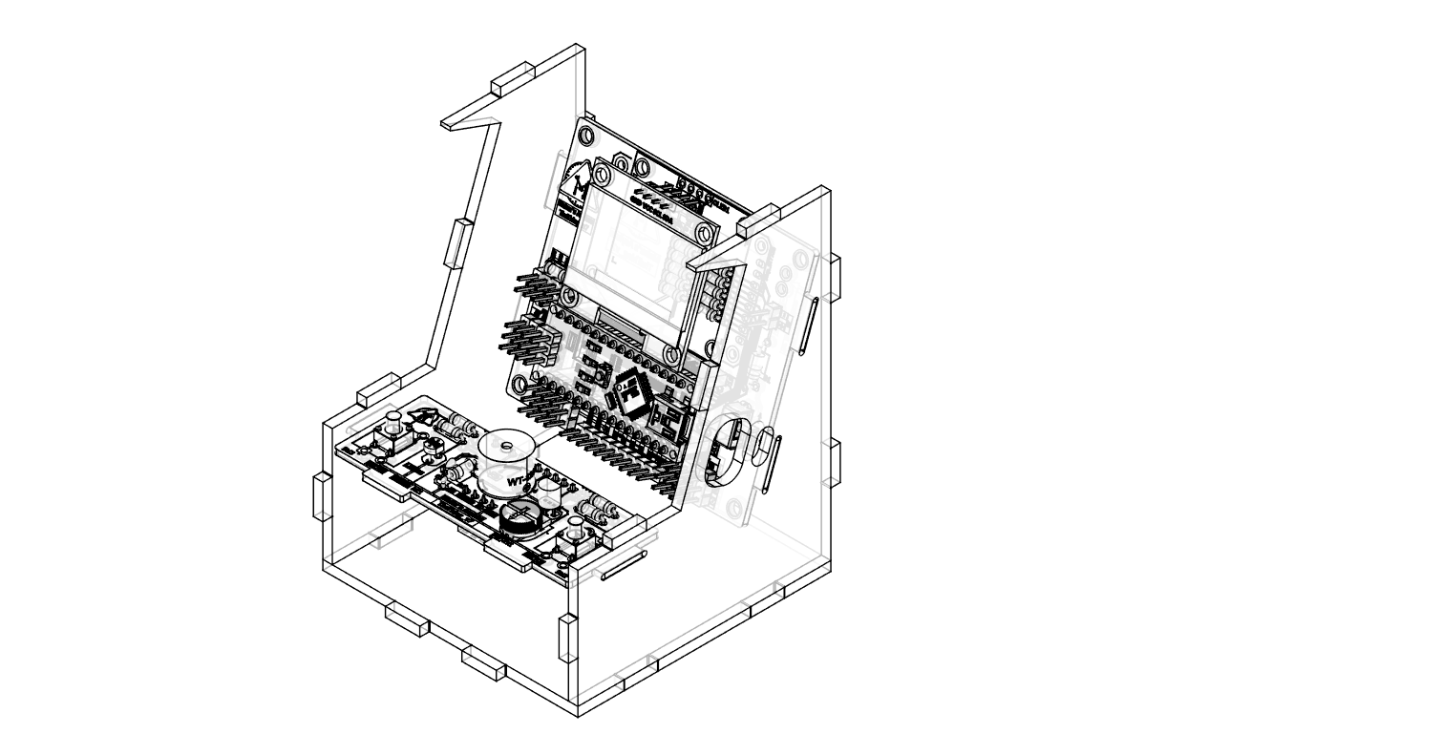
enclosure/images_user_guide/05a.png
