MakersAsylumIndia/Arcade/enclosure/images_user_guide/06b.png

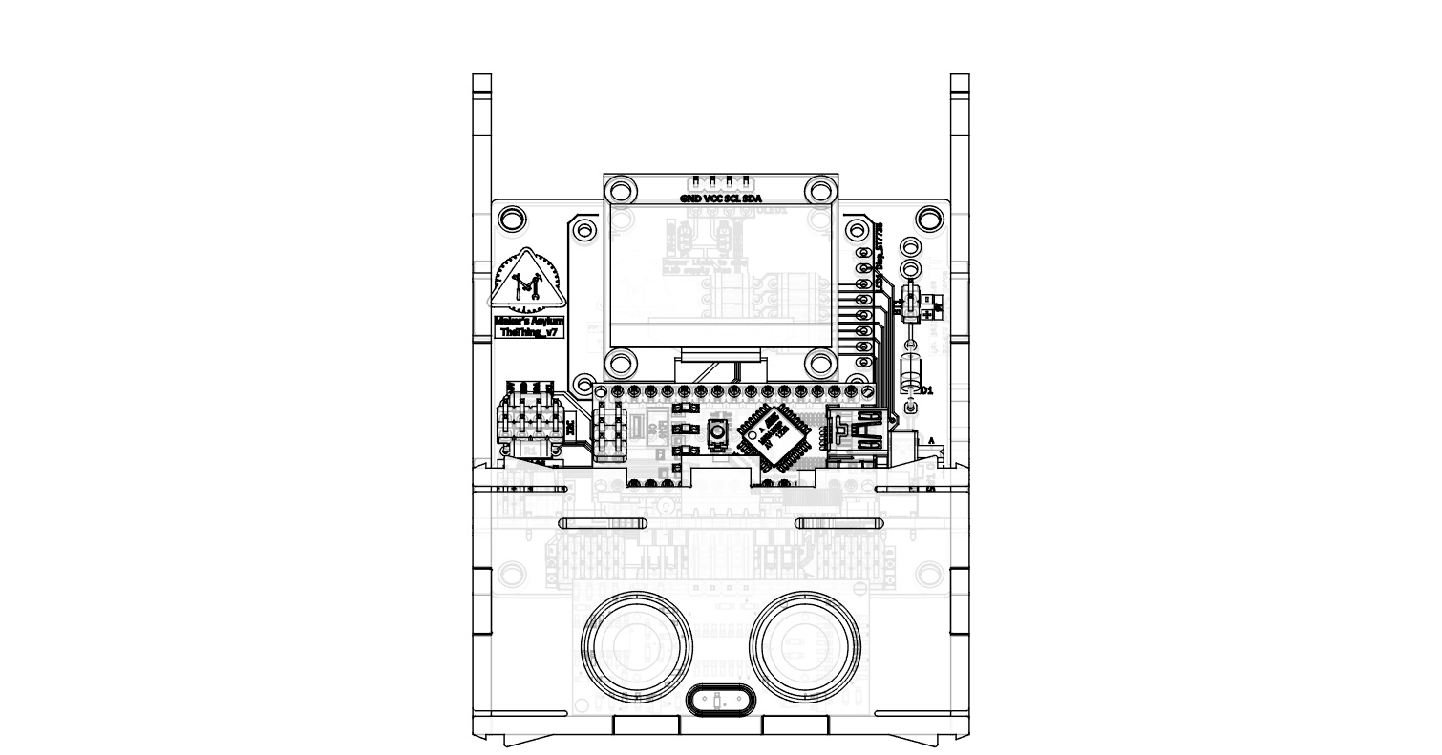
enclosure/images_user_guide/06b.png
