MakersAsylumIndia/Arcade/enclosure/images_user_guide/08a.png

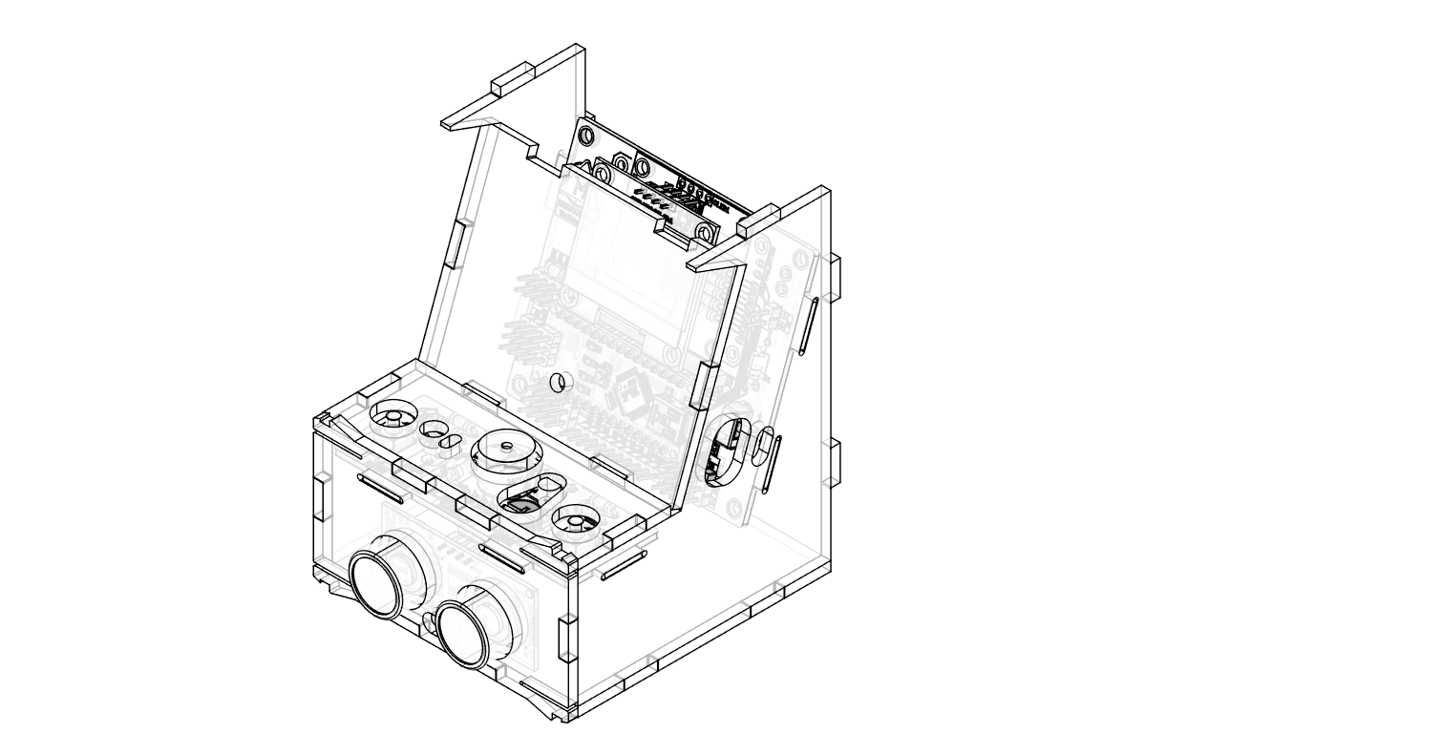
enclosure/images_user_guide/08a.png
