MakersAsylumIndia/Arcade/enclosure/images_user_guide/09c.png

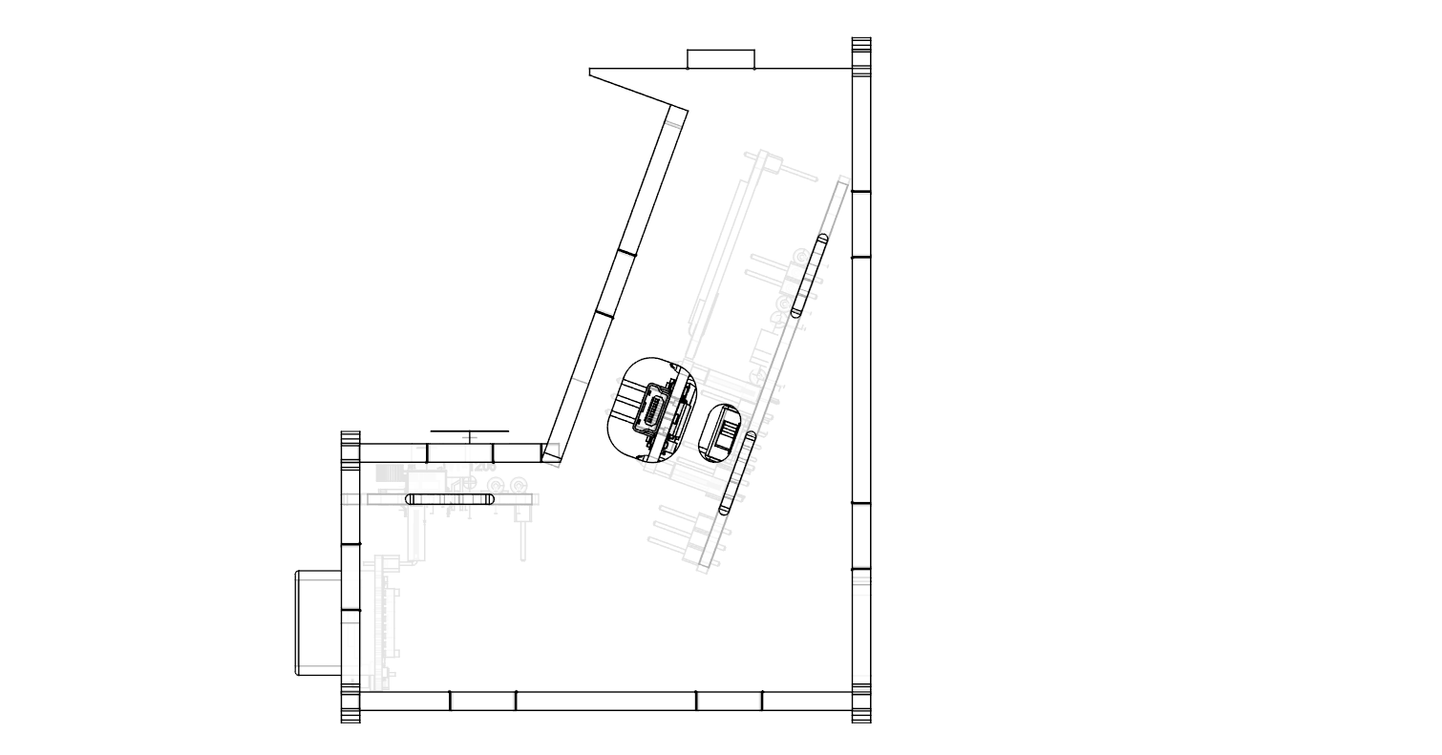
enclosure/images_user_guide/09c.png
