MakersAsylumIndia/Arcade/enclosure/images_user_guide/10a.png

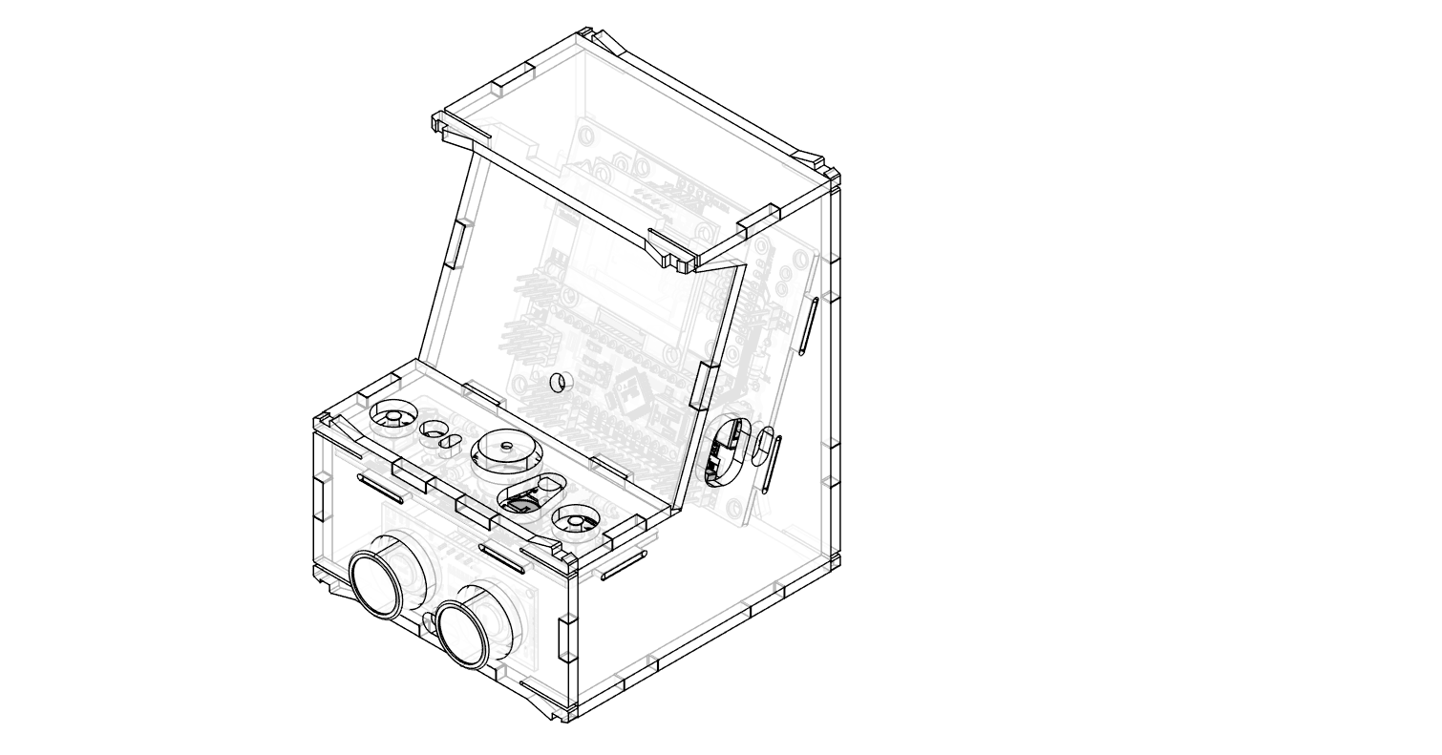
enclosure/images_user_guide/10a.png
