MakersAsylumIndia/Arcade/enclosure/images_user_guide/12c.png

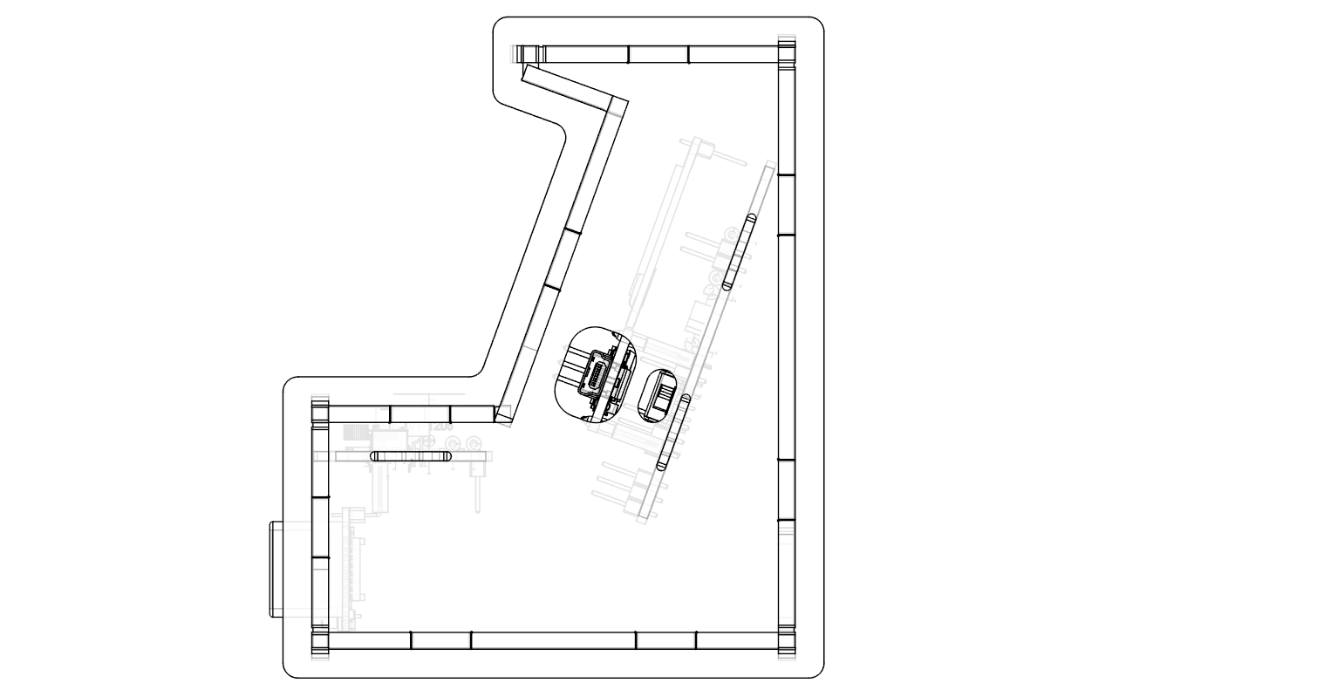
enclosure/images_user_guide/12c.png
