MakersAsylumIndia/Arcade/enclosure/images_user_guide/New Folder/015_A.png

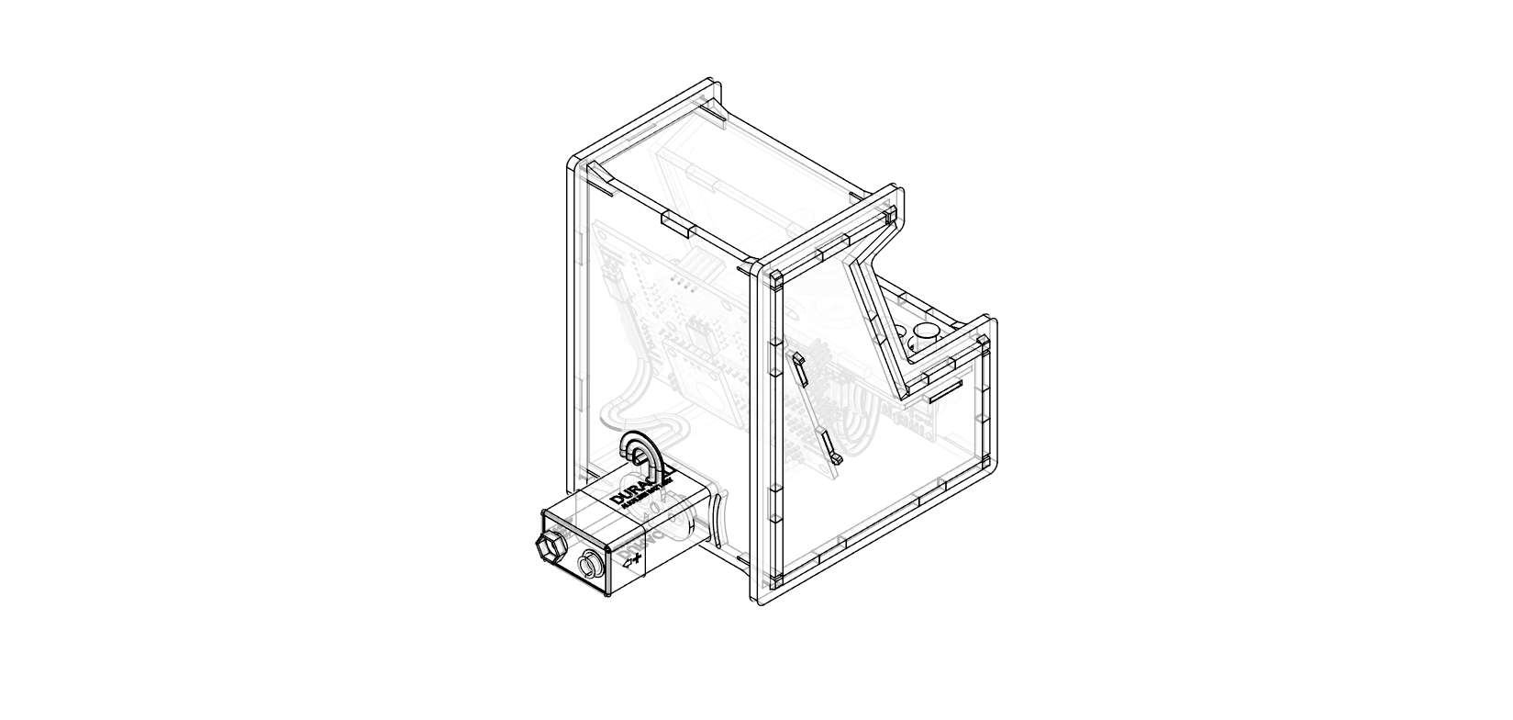
enclosure/images_user_guide/New Folder/015_A.png
