MakersAsylumIndia/Arcade/fabricate/renders/Arcade_v1_01.png

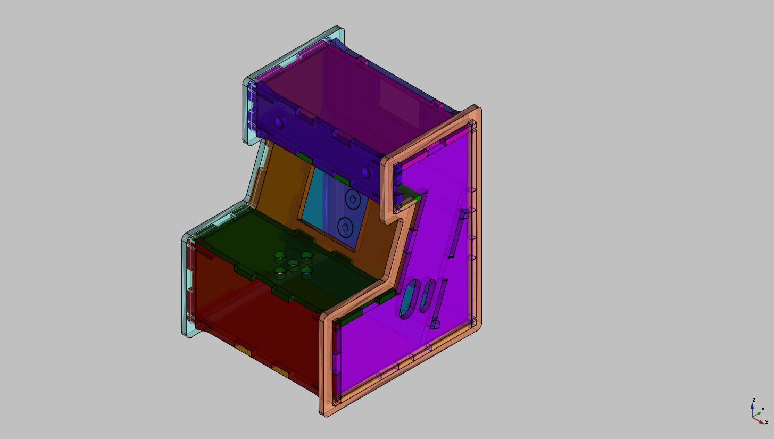
fabricate/renders/Arcade_v1_01.png
