MakersAsylumIndia/Arcade/fabricate/renders/Arcade_v1_03.png

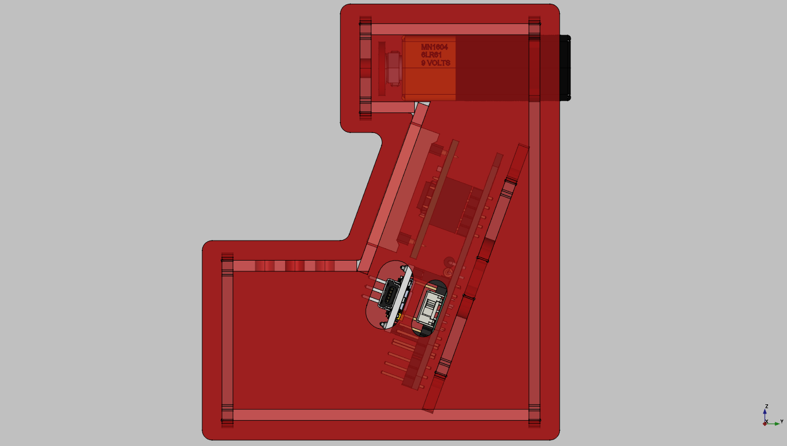
fabricate/renders/Arcade_v1_03.png
