MakersAsylumIndia/Arcade/fabricate/renders/Arcade_v1_04.png

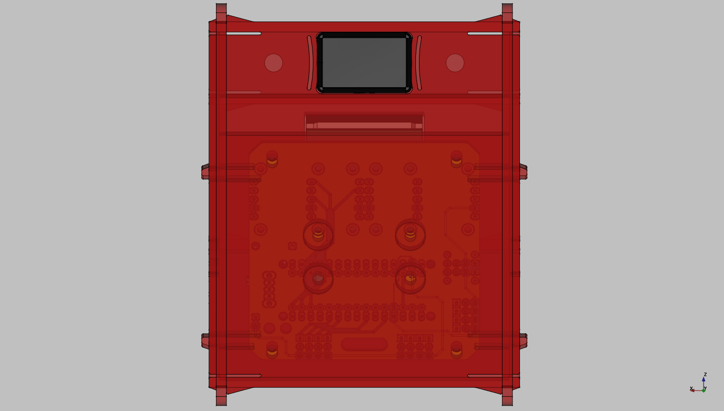
fabricate/renders/Arcade_v1_04.png
