MakersAsylumIndia/Arcade/fabricate/renders/Arcade_v1_05.png

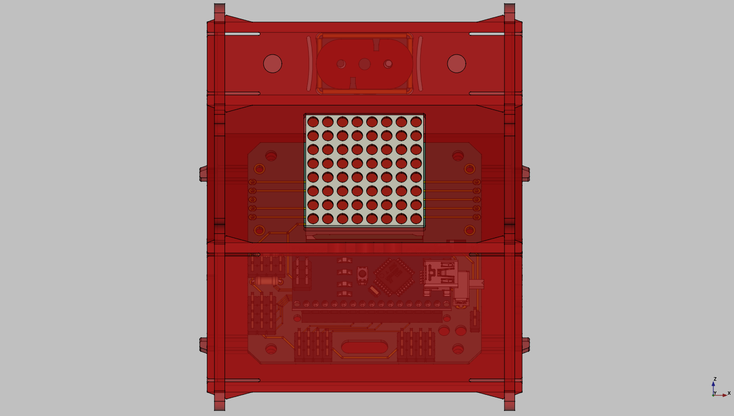
fabricate/renders/Arcade_v1_05.png
