MakersAsylumIndia/Arcade/fabricate/renders/BagTag_01.png

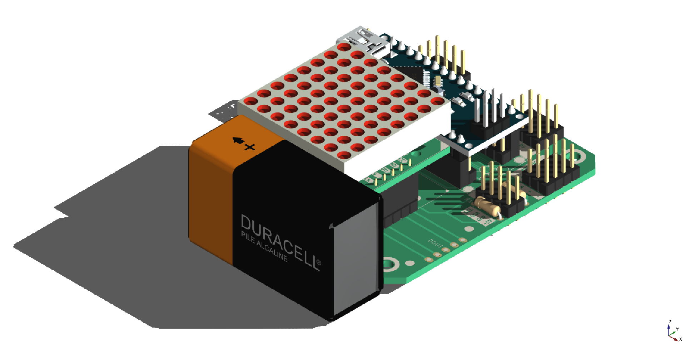
fabricate/renders/BagTag_01.png
