MakersAsylumIndia/Arcade/fabricate/renders/BagTag_02.png

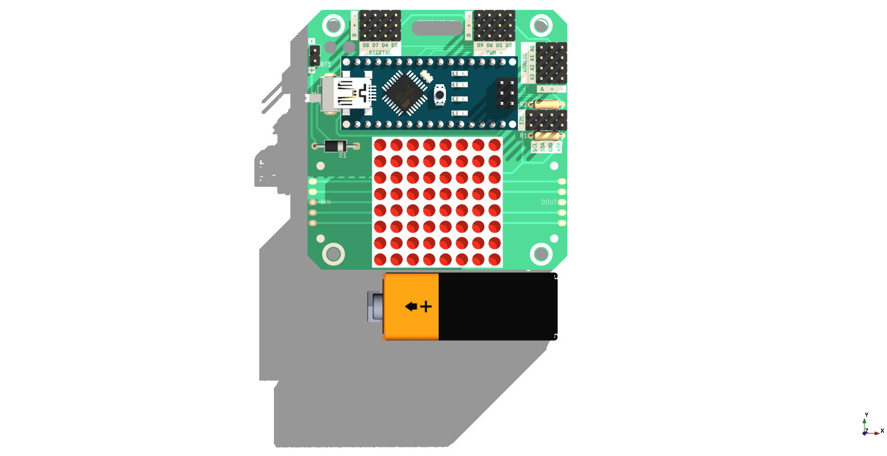
fabricate/renders/BagTag_02.png
