MakersAsylumIndia/Arcade/fabricate/renders/BagTag_03.png

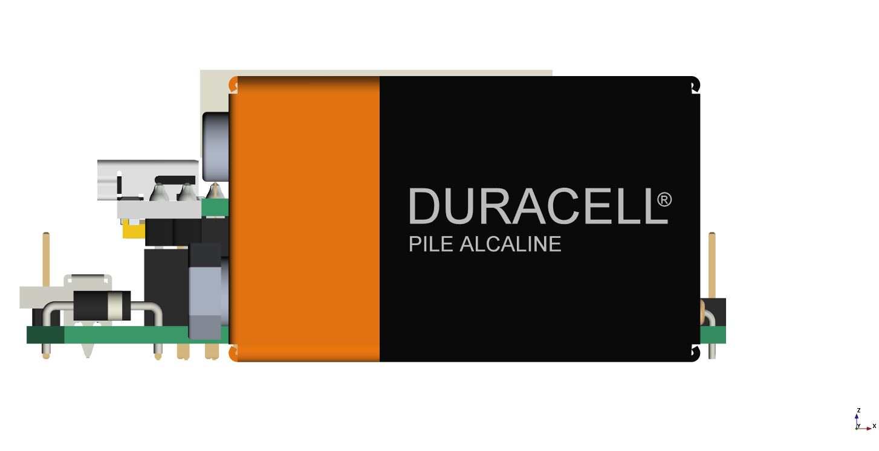
fabricate/renders/BagTag_03.png
