MakersAsylumIndia/Arcade/fabricate/renders/BagTag_04.png

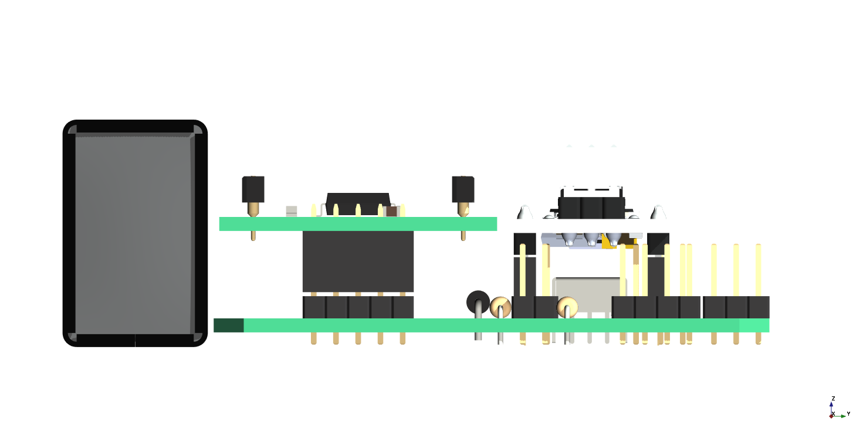
fabricate/renders/BagTag_04.png
