MakersAsylumIndia/Arcade/fabricate/renders/BagTag_05.png

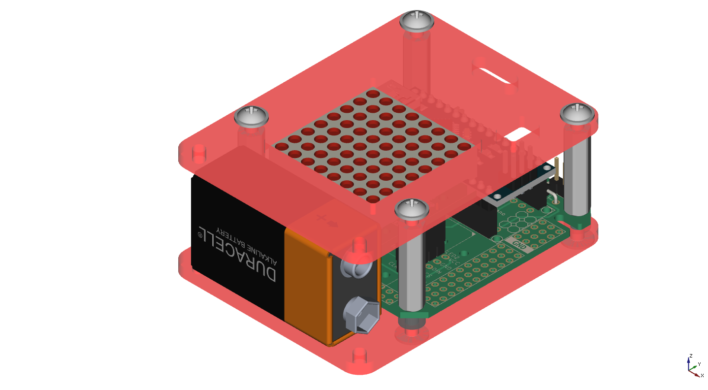
fabricate/renders/BagTag_05.png
