MakersAsylumIndia/Arcade/fabricate/renders/BagTag_06.png

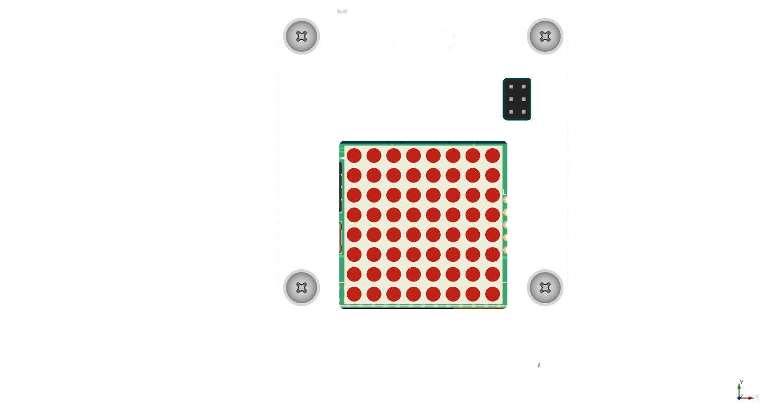
fabricate/renders/BagTag_06.png
