MakersAsylumIndia/Arcade/fabricate/renders/BagTag_08.png

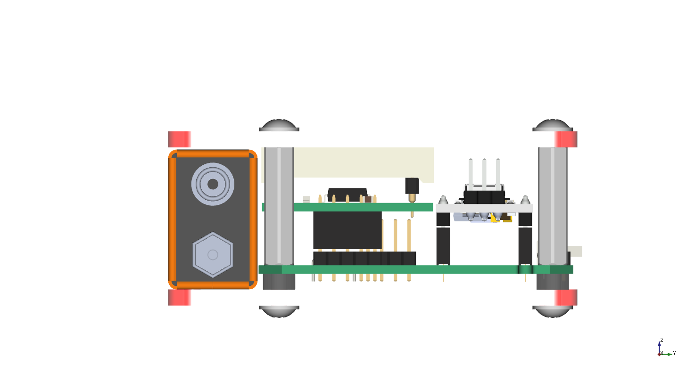
fabricate/renders/BagTag_08.png
