MakersAsylumIndia/Arcade/fabricate/renders/BagTag_10.png

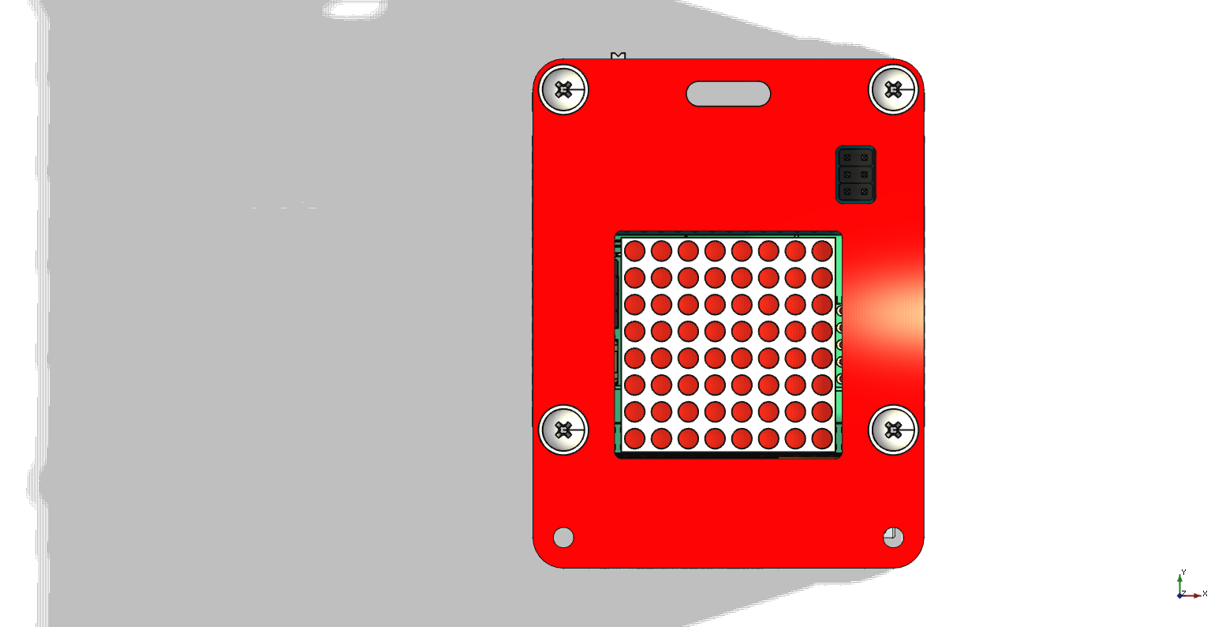
fabricate/renders/BagTag_10.png
