MakersAsylumIndia/Arcade/fabricate/renders/BagTag_11.png

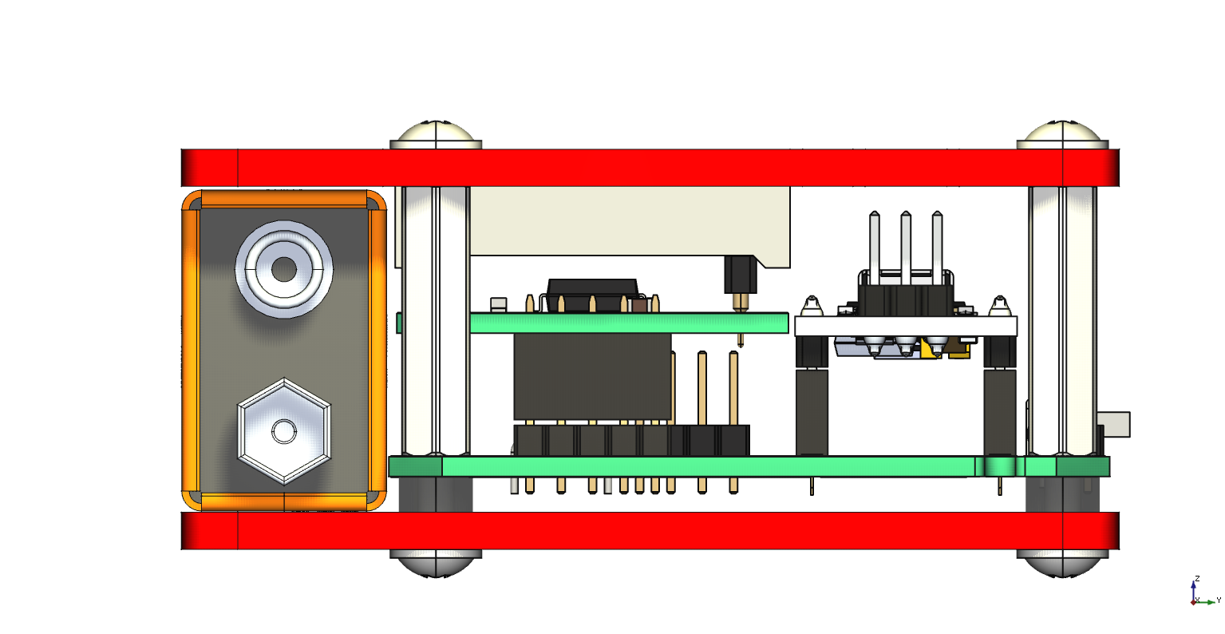
fabricate/renders/BagTag_11.png
