MakersAsylumIndia/Arcade/fabricate/renders/BagTag_12.png

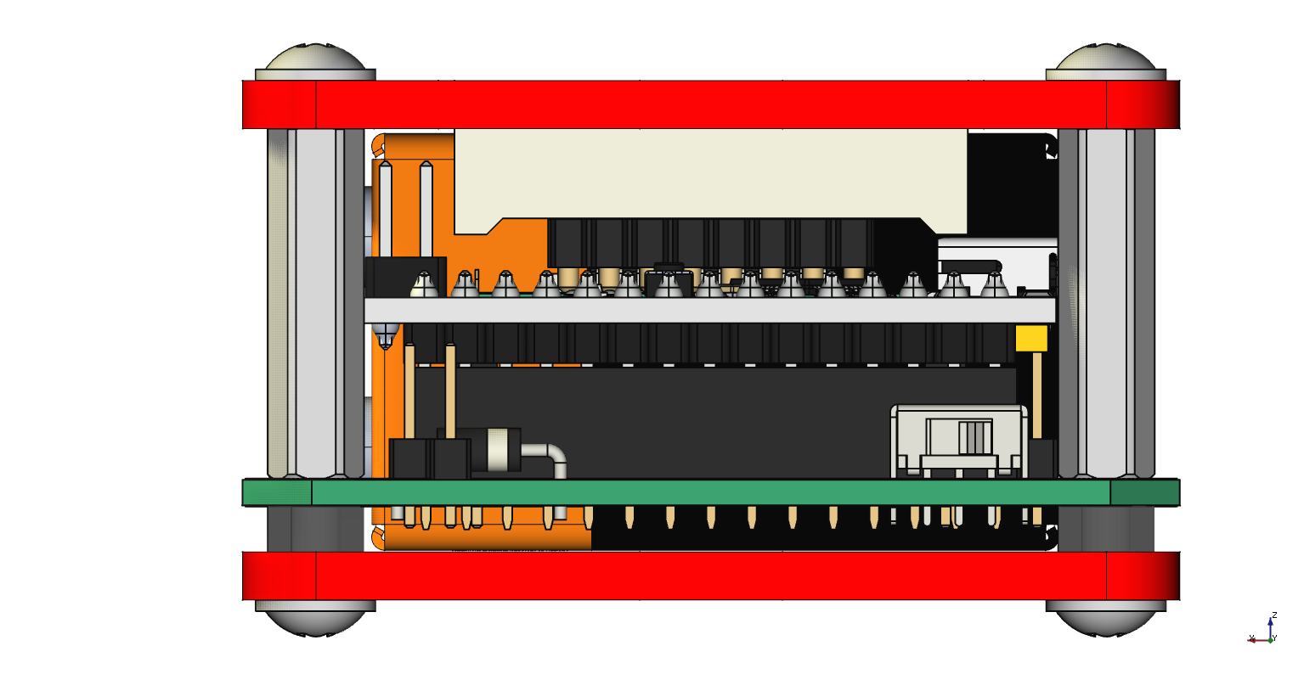
fabricate/renders/BagTag_12.png
