MakersAsylumIndia/Arcade/fabricate/renders/BagTag_13.png

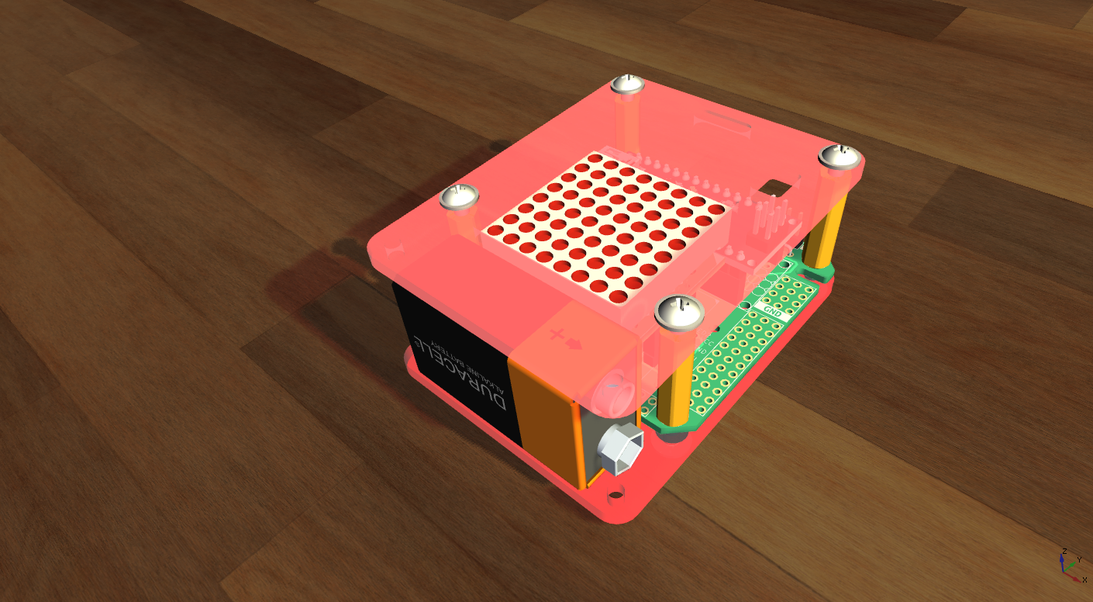
fabricate/renders/BagTag_13.png
