MakersAsylumIndia/Arcade/code/codes_testing/07_ULTRASONIC_SENSOR_TEST/07_ULTRASONIC_SENSOR_TEST.ino

/* =============================================================================
   ULTRASONIC SENSOR TEST
   Hardware: Trigger → D7, Echo → D6
   Purpose : Measure and print distance to Serial Monitor
   =============================================================================
*/

#define TRIG_PIN 7
#define ECHO_PIN 6

void setup() {
  pinMode(TRIG_PIN, OUTPUT);
  pinMode(ECHO_PIN, INPUT);
  Serial.begin(9600);
}

void loop() {
  digitalWrite(TRIG_PIN, LOW);
  delayMicroseconds(2);
  digitalWrite(TRIG_PIN, HIGH);
  delayMicroseconds(10);
  digitalWrite(TRIG_PIN, LOW);

  long duration = pulseIn(ECHO_PIN, HIGH);
  int distance = duration * 0.034 / 2;

  Serial.print("Distance: ");
  Serial.print(distance);
  Serial.println(" cm");
  delay(500);
}
