MakersAsylumIndia/Arcade/code/codes_demo/05_ultrasonic/05_ultrasonic.ino

/*  Ultrasonic distance sensor HC-SR04 demo sketch 
 * 
 * This sketch calculates the distance between the HC-SR04 sensor and
 * an object directly infront of it.
 * 
 * 
 * This sketch was written for Arduino Step by Step by Peter Dalmaris.
 * 
 * Components
 * ----------
 *  - Arduino Uno
 *  - HC-SR04 sensor
 *  
 *  Libraries
 *  ---------
 *  - NONE
 *
 * Connections
 * -----------
 *  Break out    |    Arduino Uno
 *  -----------------------------
 *      VCC      |      5V
 *      GND      |      GND
 *      Echo     |      6
 *      Trig     |      7
 *   
 * 
 * Other information
 * -----------------
 *  For information on the ultrasonic transducer: https://en.wikipedia.org/wiki/Ultrasonic_transducer
 *  For information on ultrasounds: https://en.wikipedia.org/wiki/Ultrasound
 *  HC-SR04 datasheet: https://docs.google.com/document/d/1Y-yZnNhMYy7rwhAgyL_pfa39RsB-x2qR4vP8saG73rE
 *  Information about the pulseIn function: https://www.arduino.cc/en/Reference/PulseIn
 *  
 *  Created on October 21 2016 by Peter Dalmaris
 * 
 */


#define trigPin 7
#define echoPin 6

void setup() {
  Serial.begin (9600);
  pinMode(trigPin, OUTPUT);
  pinMode(echoPin, INPUT);
}

void loop() {
  long duration, distance;
  digitalWrite(trigPin, LOW); 
  delayMicroseconds(2); 
  digitalWrite(trigPin, HIGH);
  delayMicroseconds(10);
  digitalWrite(trigPin, LOW);
  duration = pulseIn(echoPin, HIGH);
  distance = (duration/2) / 29.1;

  if (distance >= 200 || distance <= 0){
    Serial.println("Out of range");
  }
  else {
    Serial.print(distance);
    Serial.println(" cm");
  }
  delay(500);
}
